vaelen/mini-xt/hardware/sheets/addr_decode.kicad_sch

## KiCad design hardware/sheets/addr_decode.kicad_sch (2026-07-23)

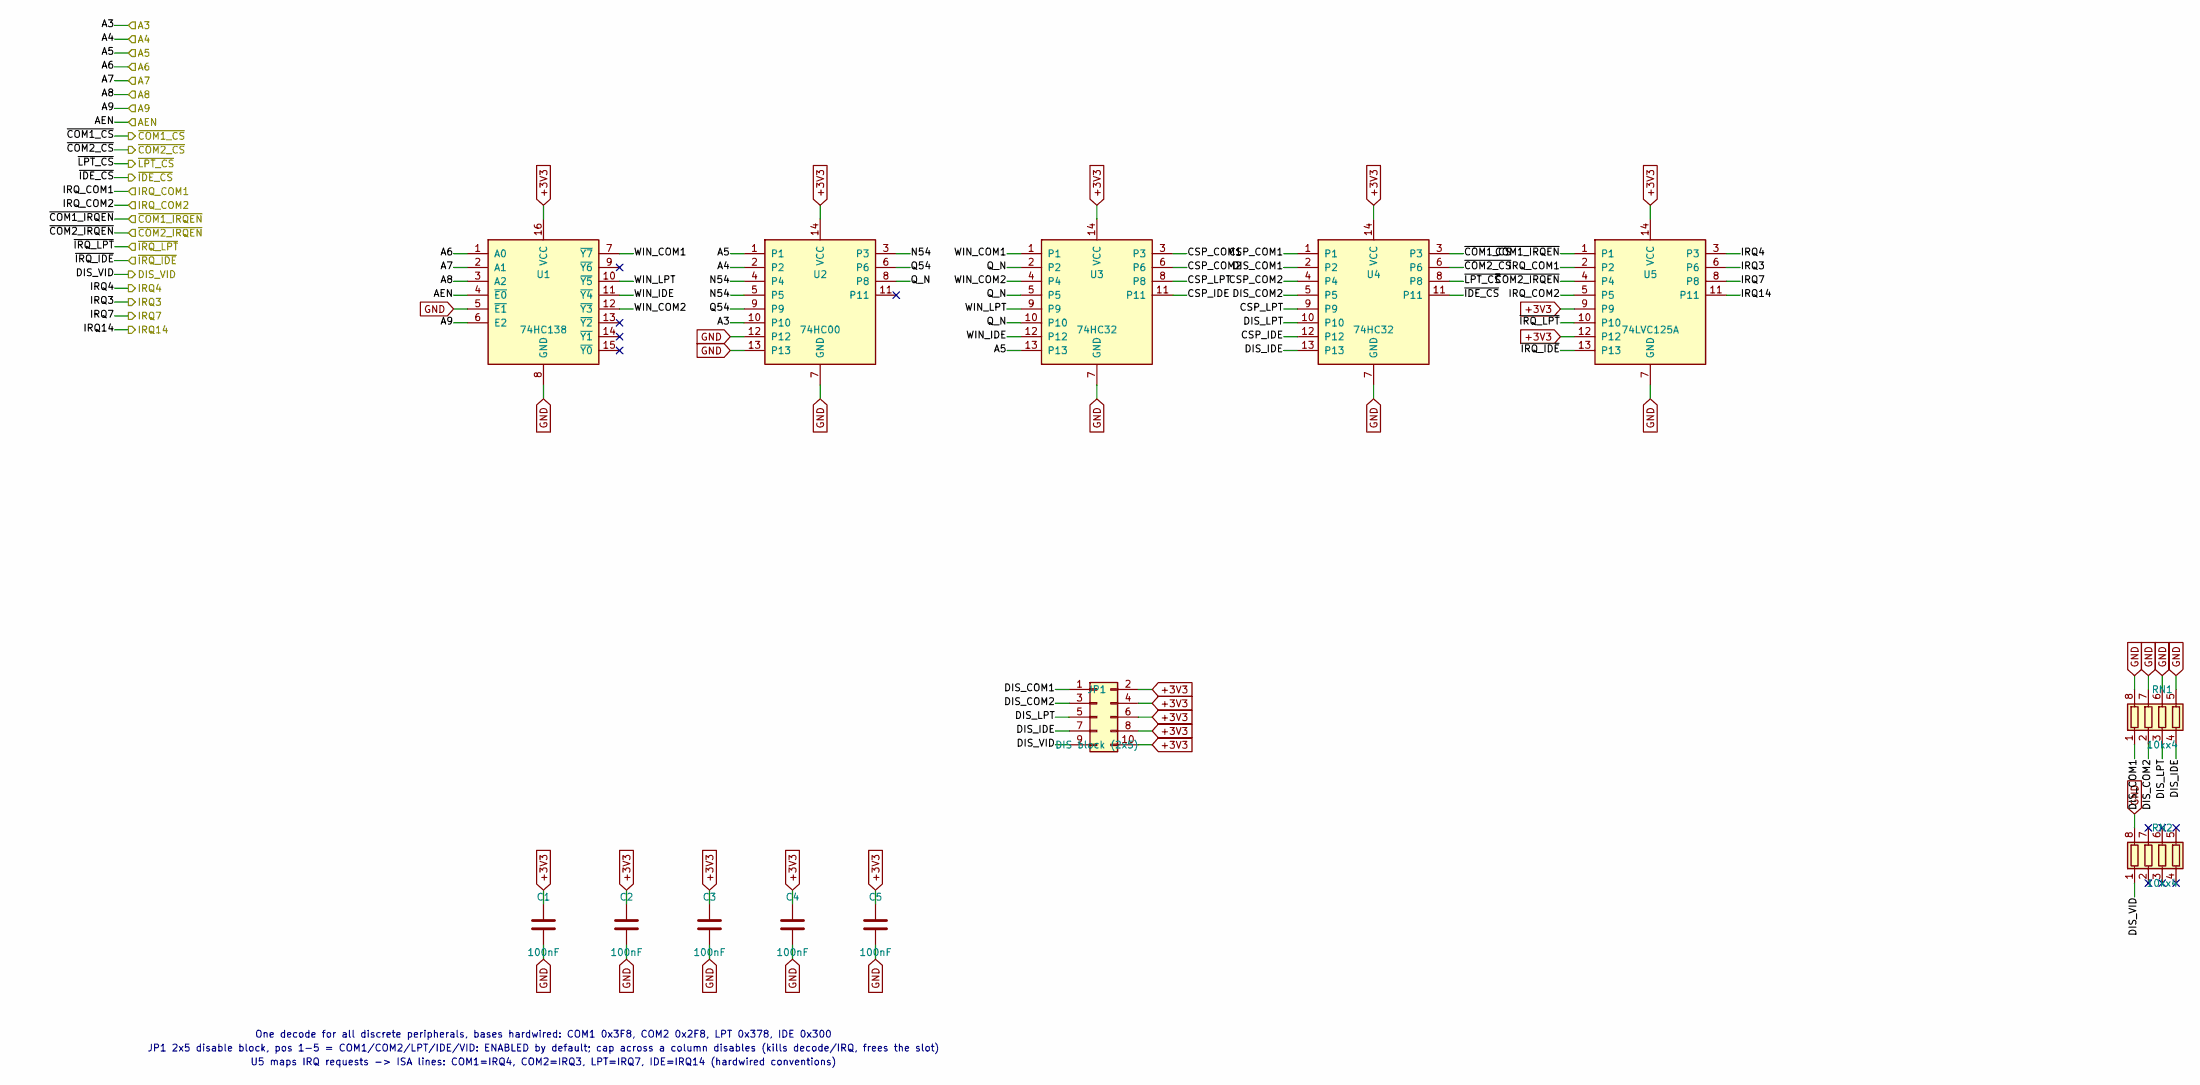
[picture p21: schematic addr_decode.kicad_sch]

Parts:
C1, C2, C3, C4, C5: 100nF; C_0603_1608Metric; LCSC Part Num C14663
JP1: DIS block (2x5); PinHeader_2x05_P2.54mm_Vertical; LCSC Part Num C492422
RN1, RN2: 10kx4; R_Array_Convex_4x0603; LCSC Part Num C29718
U1: 74HC138; SOIC-16_3.9x9.9mm_P1.27mm; LCSC Part Num C5602
U2: 74HC00; SOIC-14_3.9x8.7mm_P1.27mm; LCSC Part Num C699445
U3, U4: 74HC32; SOIC-14_3.9x8.7mm_P1.27mm; LCSC Part Num C52140395
U5: 74LVC125A; SOIC-14_3.9x8.7mm_P1.27mm; LCSC Part Num C6057

Connections:
+3V3: C1.1, C2.1, C3.1, C4.1, C5.1, JP1.2, JP1.4, JP1.6, JP1.8, JP1.10, U1.16 (VCC), U2.14 (VCC), U3.14 (VCC), U4.14 (VCC), U5.9, U5.12, U5.14 (VCC)
A3: U2.10
A4: U2.2
A5: U2.1, U3.13
A6: U1.1 (A0)
A7: U1.2 (A1)
A8: U1.3 (A2)
A9: U1.6 (E2)
AEN: U1.4 (~E0)
CSP_COM1: U3.3, U4.1
CSP_COM2: U3.6, U4.4
CSP_IDE: U3.11, U4.12
CSP_LPT: U3.8, U4.9
DIS_COM1: JP1.1, RN1.1 (R1.1), U4.2
DIS_COM2: JP1.3, RN1.2 (R2.1), U4.5
DIS_IDE: JP1.7, RN1.4 (R4.1), U4.13
DIS_LPT: JP1.5, RN1.3 (R3.1), U4.10
DIS_VID: JP1.9, RN2.1 (R1.1)
GND: C1.2, C2.2, C3.2, C4.2, C5.2, RN1.5 (R4.2), RN1.6 (R3.2), RN1.7 (R2.2), RN1.8 (R1.2), RN2.8 (R1.2), U1.5 (~E1), U1.8 (GND), U2.7 (GND), U2.12, U2.13, U3.7 (GND), U4.7 (GND), U5.7 (GND)
IRQ3: U5.6
IRQ4: U5.3
IRQ7: U5.8
IRQ14: U5.11
IRQ_COM1: U5.2
IRQ_COM2: U5.5
N54: U2.3, U2.4, U2.5
Q54: U2.6, U2.9
Q_N: U2.8, U3.2, U3.5, U3.10
WIN_COM1: U1.7 (~Y7), U3.1
WIN_COM2: U1.12 (~Y3), U3.4
WIN_IDE: U1.11 (~Y4), U3.12
WIN_LPT: U1.10 (~Y5), U3.9
~COM1_CS: U4.3
~COM1_IRQEN: U5.1
~COM2_CS: U4.6
~COM2_IRQEN: U5.4
~IDE_CS: U4.11
~IRQ_IDE: U5.13
~IRQ_LPT: U5.10
~LPT_CS: U4.8

Notes on the sheet:
One decode for all discrete peripherals, bases hardwired: COM1 0x3F8, COM2 0x2F8, LPT 0x378, IDE 0x300
JP1 2x5 disable block, pos 1-5 = COM1/COM2/LPT/IDE/VID: ENABLED by default; cap across a column disables (kills decode/IRQ, frees the slot)
U5 maps IRQ requests -> ISA lines: COM1=IRQ4, COM2=IRQ3, LPT=IRQ7, IDE=IRQ14 (hardwired conventions)
