vaelen/mini-xt/hardware/sheets/audio.kicad_sch

## KiCad design hardware/sheets/audio.kicad_sch (2026-07-23)

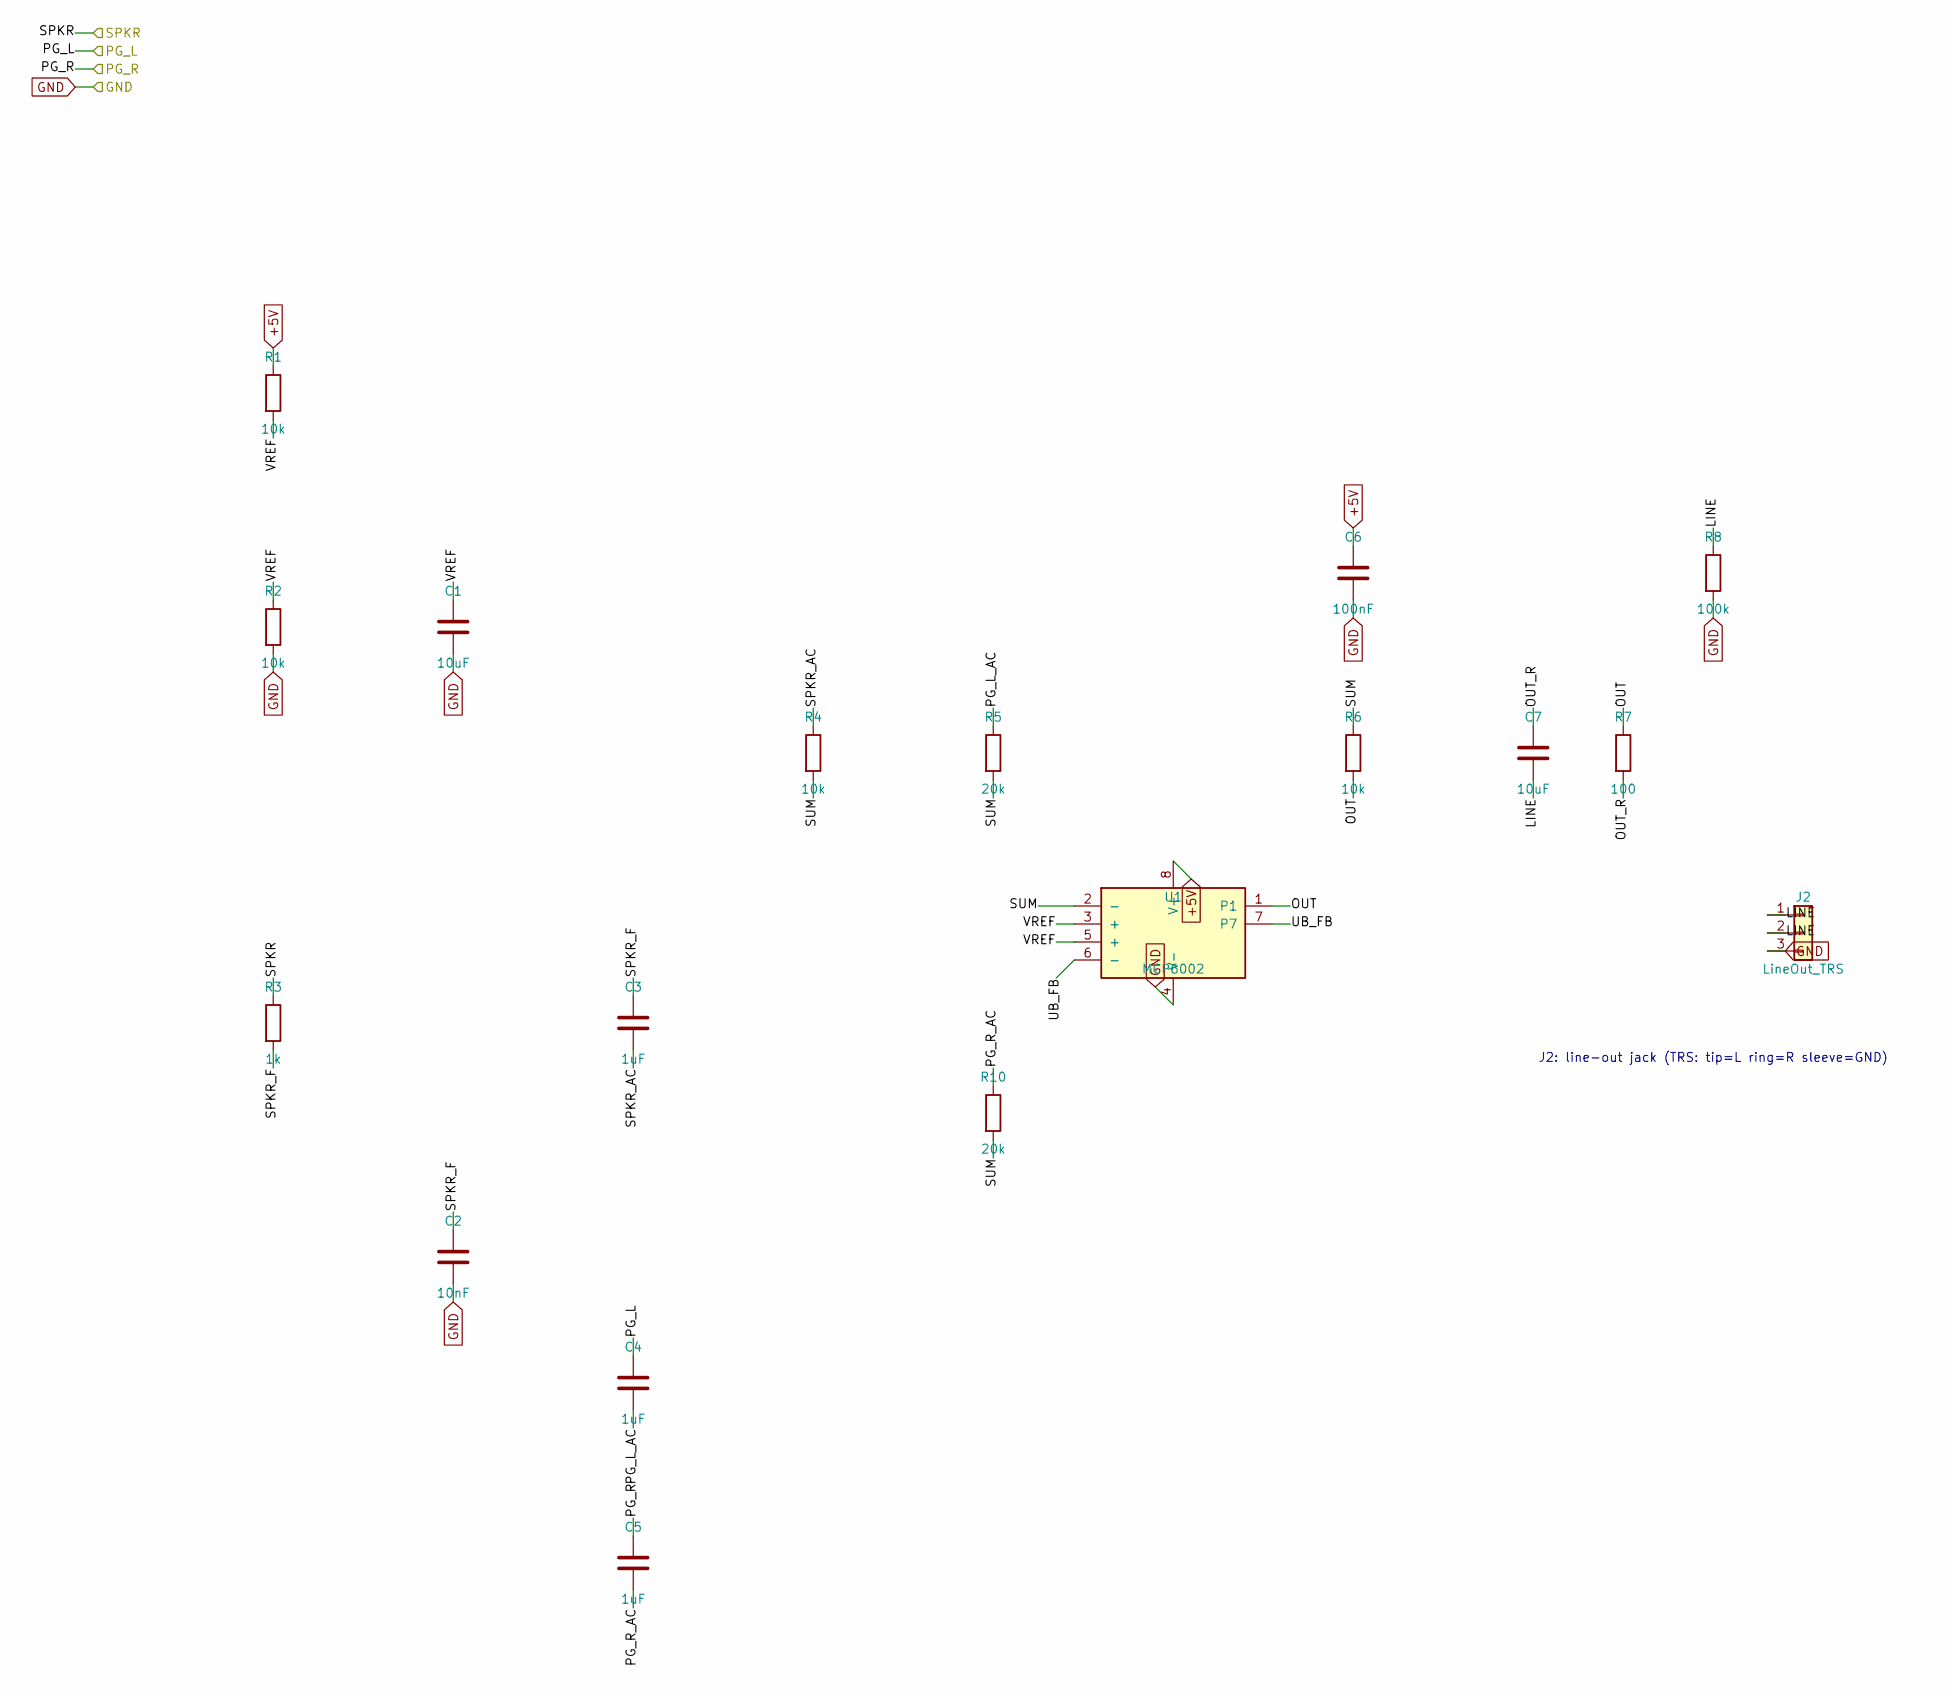
[picture p22: schematic audio.kicad_sch]

Parts:
C1, C7: 10uF; C_0805_2012Metric; LCSC Part Num C15850
C2: 10nF; C_0603_1608Metric; LCSC Part Num C57112
C3, C4, C5: 1uF; C_0603_1608Metric; LCSC Part Num C15849
C6: 100nF; C_0603_1608Metric; LCSC Part Num C14663
J2: LineOut_TRS; PinHeader_1x03_P2.54mm_Vertical; LCSC Part Num C2337
R1, R2, R4, R6: 10k; R_0805_2012Metric; LCSC Part Num C17414
R3: 1k; R_0603_1608Metric; LCSC Part Num C21190
R5, R10: 20k; R_0603_1608Metric; LCSC Part Num C4184
R7: 100; R_0603_1608Metric; LCSC Part Num C22775
R8: 100k; R_0603_1608Metric; LCSC Part Num C25803
U1: MCP6002; SOIC-8_3.9x4.9mm_P1.27mm; LCSC Part Num C7377

Connections:
+5V: C6.1, R1.1, U1.8 (V+)
GND: C1.2, C2.2, C6.2, J2.3, R2.2, R8.2, U1.4 (V-)
LINE: C7.2, J2.1, J2.2, R8.1
OUT: R6.2, R7.1, U1.1
OUT_R: C7.1, R7.2
PG_L: C4.1
PG_L_AC: C4.2, R5.1
PG_R: C5.1
PG_R_AC: C5.2, R10.1
SPKR: R3.1
SPKR_AC: C3.2, R4.1
SPKR_F: C2.1, C3.1, R3.2
SUM: R4.2, R5.2, R6.1, R10.2, U1.2 (-)
UB_FB: U1.6 (-), U1.7
VREF: C1.1, R1.2, R2.1, U1.3 (+), U1.5 (+)

Notes on the sheet:
J2: line-out jack (TRS: tip=L ring=R sleeve=GND)
