vaelen/mini-xt/hardware/sheets/bus_mcu.kicad_sch

## KiCad design hardware/sheets/bus_mcu.kicad_sch (2026-07-23)

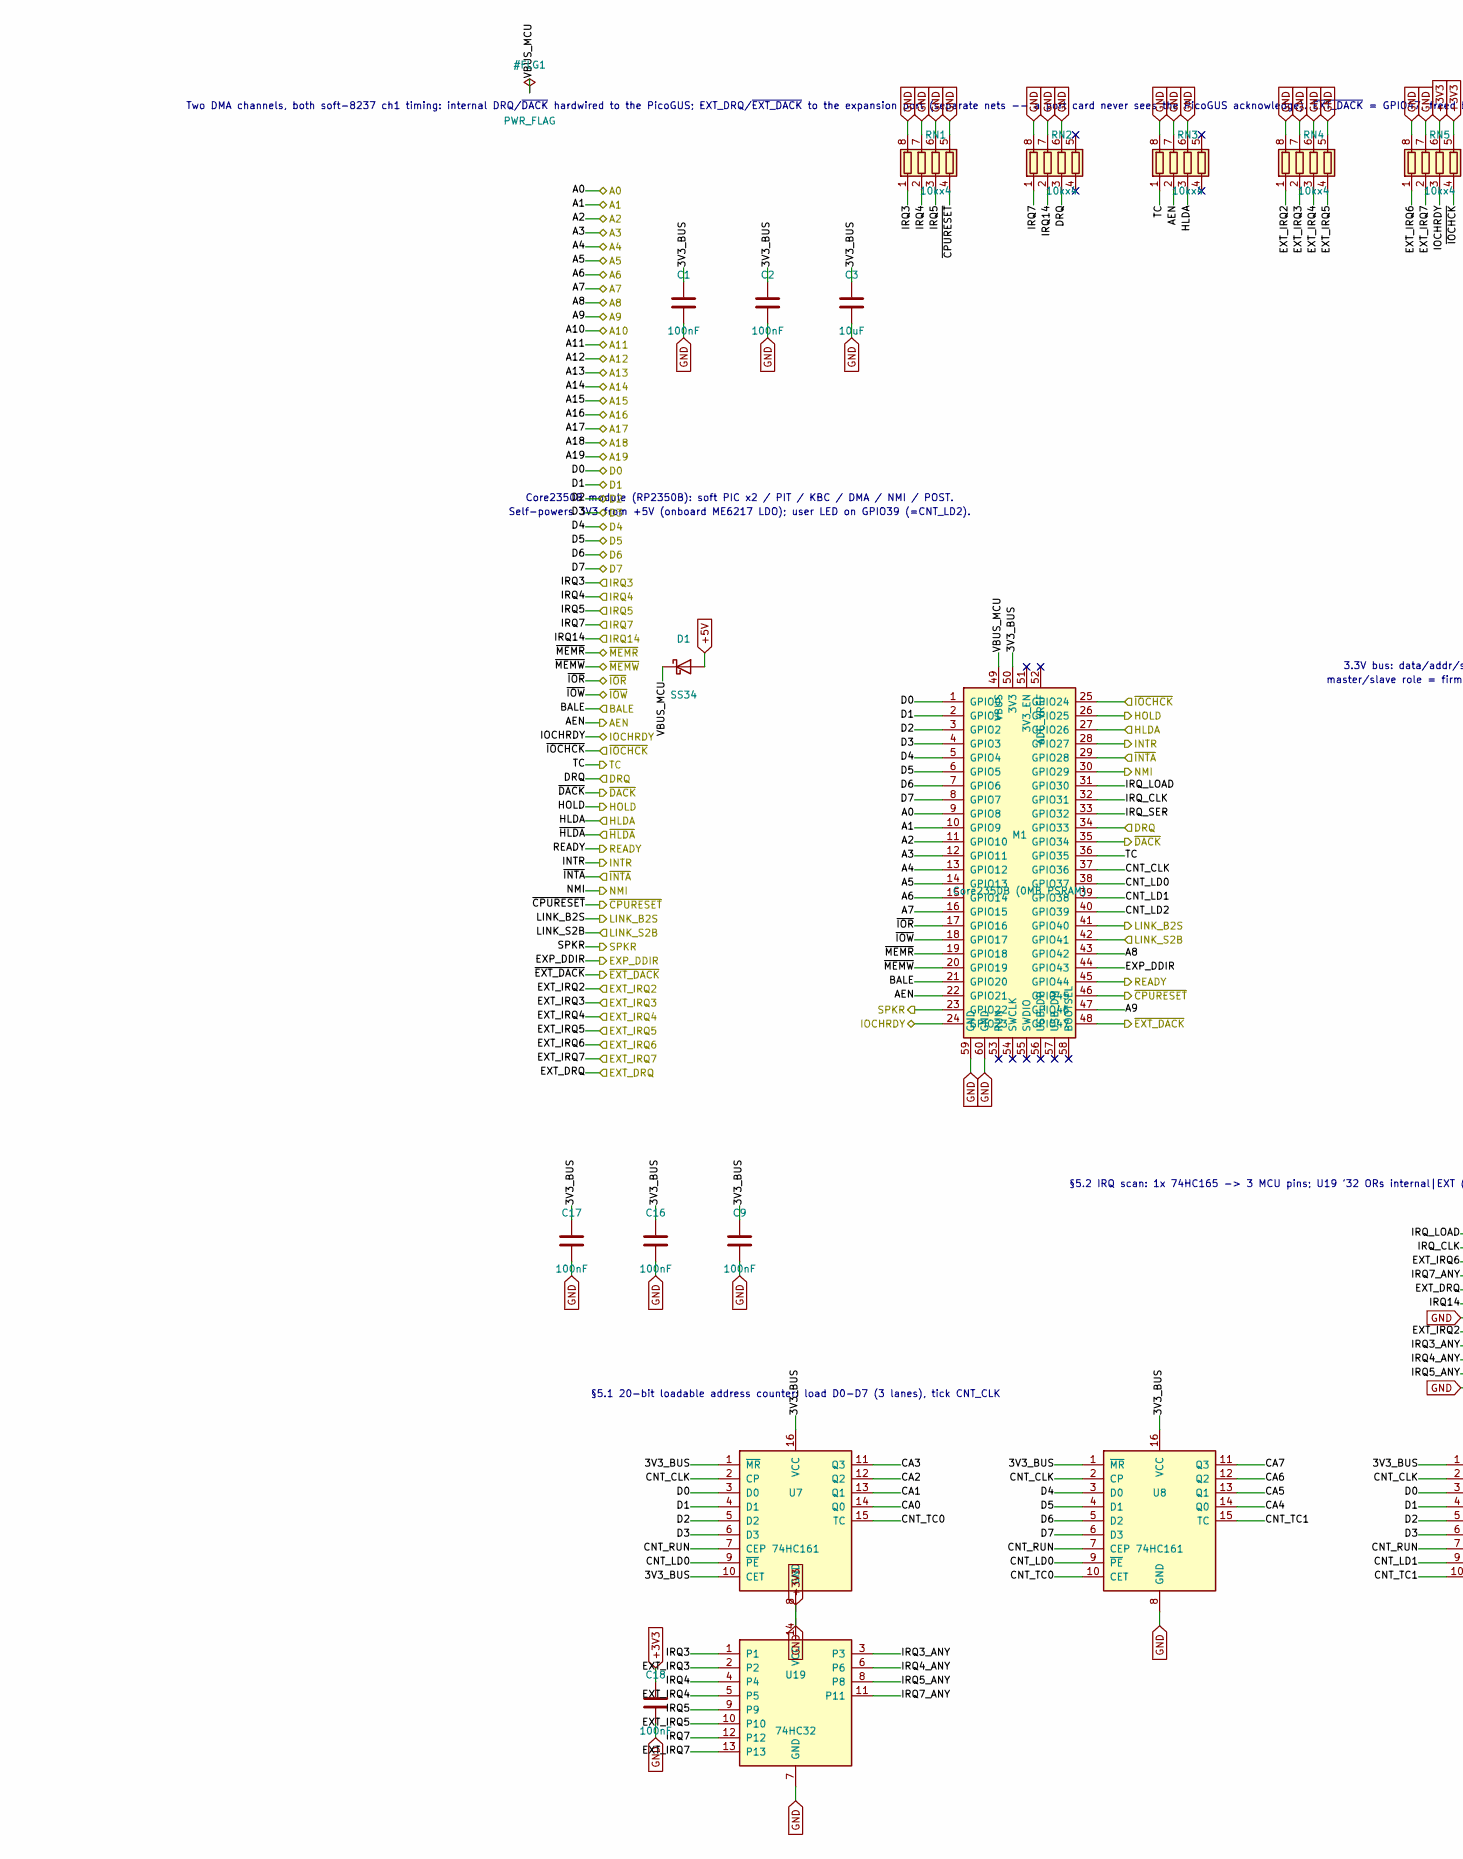
[picture p23: schematic bus_mcu.kicad_sch, part in row 1, column 1]

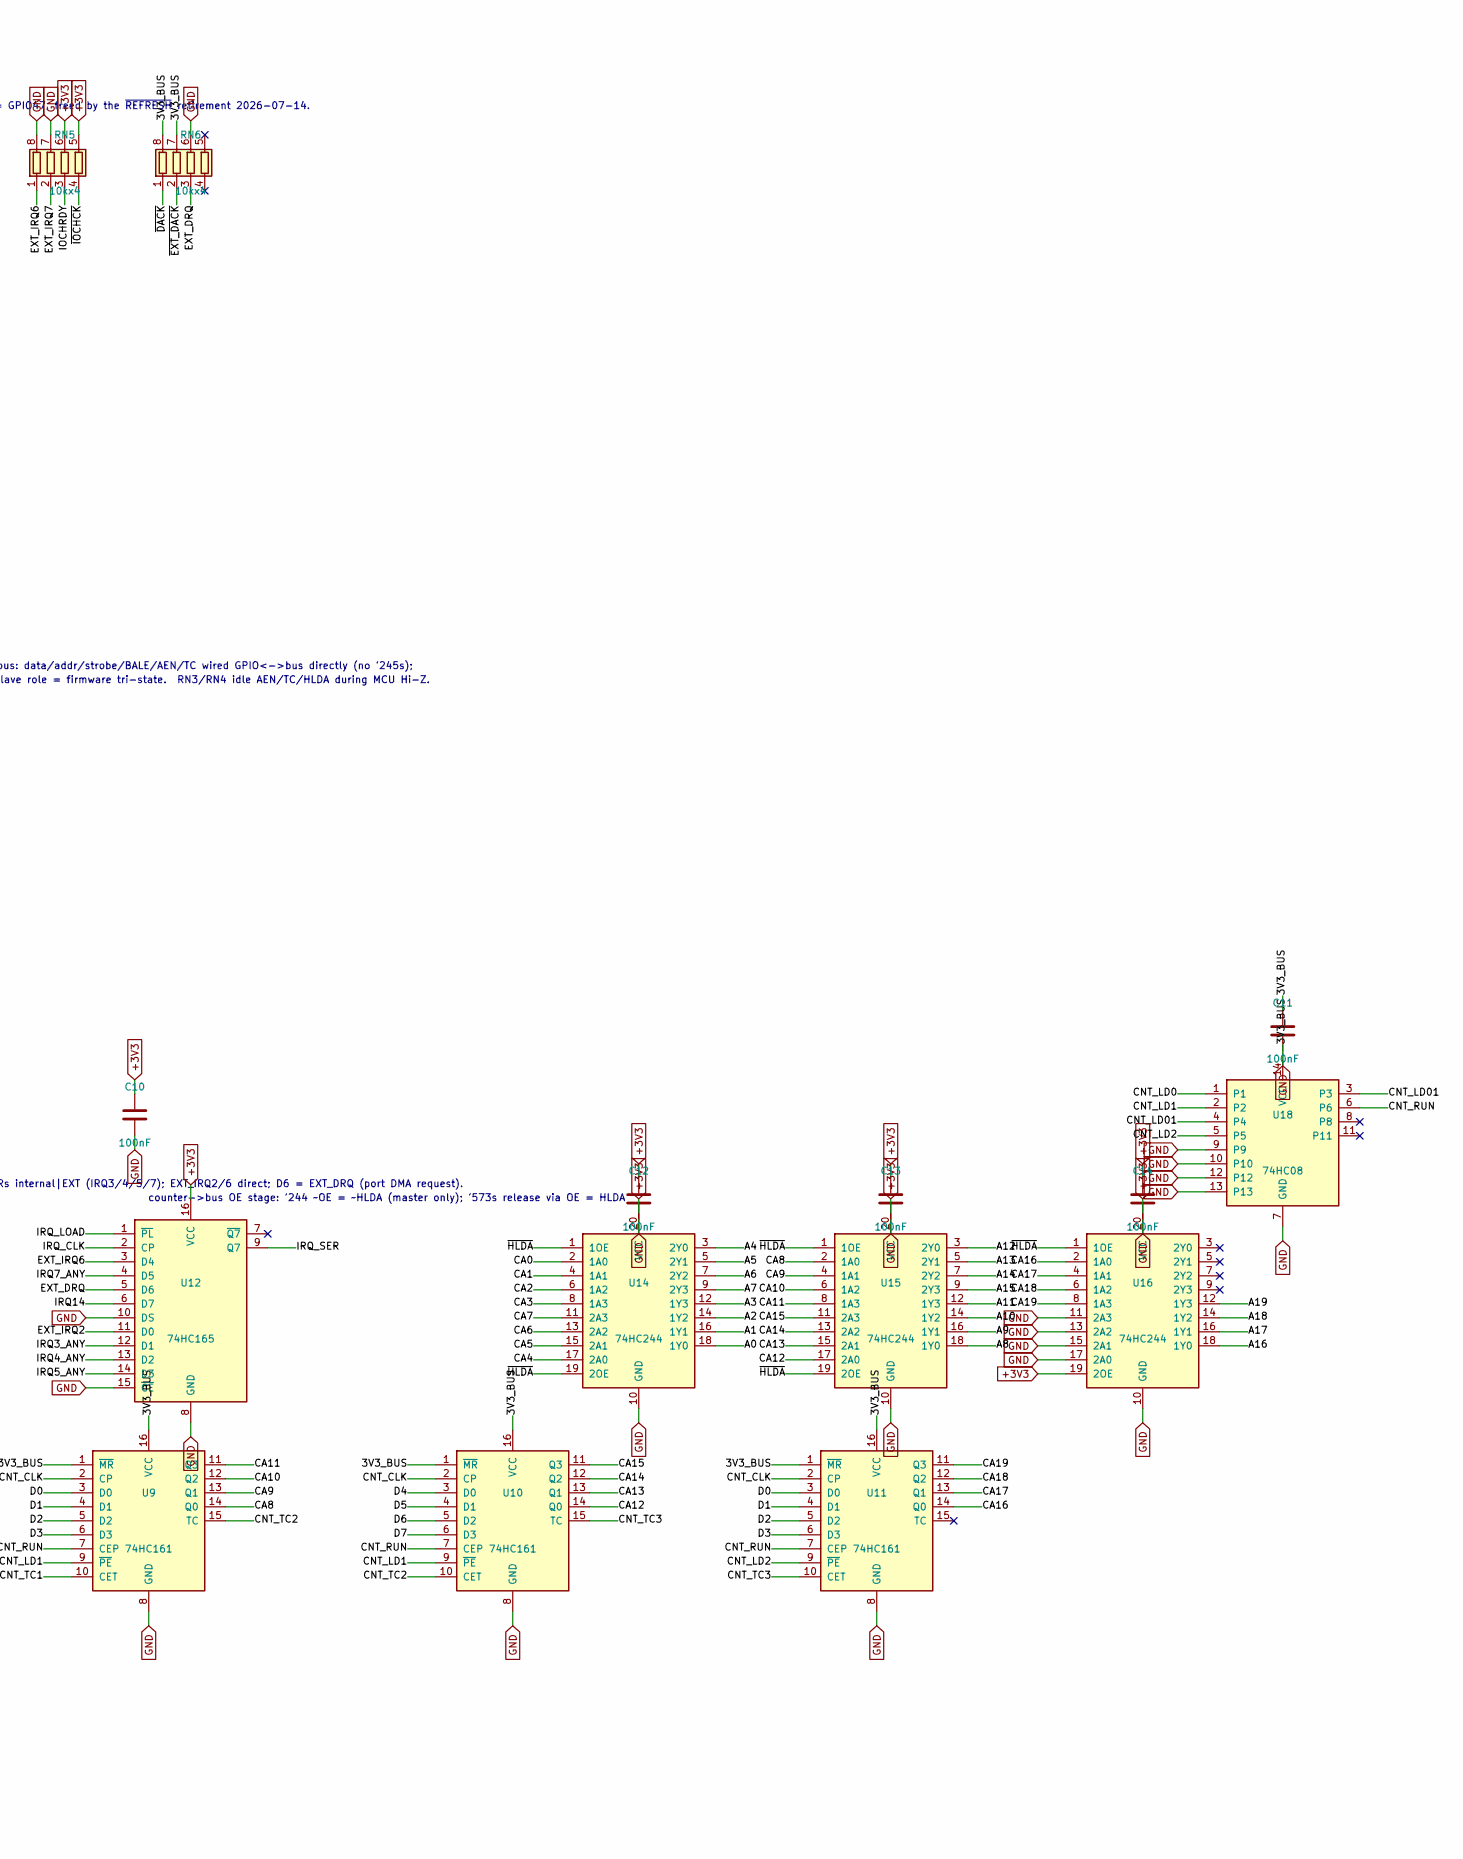
[picture p24: schematic bus_mcu.kicad_sch, part in row 1, column 2]

Parts:
C1, C2, C9, C10, C11, C12, C13, C14, C16, C17, C18: 100nF; C_0603_1608Metric; LCSC Part Num C14663
C3: 10uF; C_0805_2012Metric; LCSC Part Num C15850
D1: SS34; D_SMA; LCSC Part Num C8678
M1: Core2350B (0MB PSRAM); Core2350B_PGA; LCSC Part Num C2897411
RN1, RN2, RN3, RN4, RN5, RN6: 10kx4; R_Array_Convex_4x0603; LCSC Part Num C29718
U7, U8, U9, U10, U11: 74HC161; SOIC-16_3.9x9.9mm_P1.27mm; LCSC Part Num C5610
U12: 74HC165; SOIC-16_3.9x9.9mm_P1.27mm; LCSC Part Num C5613
U14, U15, U16: 74HC244; SOIC-20W_7.5x12.8mm_P1.27mm; LCSC Part Num C52140409
U18: 74HC08; SOIC-14_3.9x8.7mm_P1.27mm; LCSC Part Num C5593
U19: 74HC32; SOIC-14_3.9x8.7mm_P1.27mm; LCSC Part Num C52140395

Connections:
3V3_BUS: C1.1, C2.1, C3.1, C9.1, C11.1, C16.1, C17.1, M1.50 (3V3), RN6.7 (R2.2), RN6.8 (R1.2), U7.1 (~MR), U7.10 (CET), U7.16 (VCC), U8.1 (~MR), U8.16 (VCC), U9.1 (~MR), U9.16 (VCC), U10.1 (~MR), U10.16 (VCC), U11.1 (~MR), U11.16 (VCC), U18.14 (VCC)
+3V3: C10.1, C12.1, C13.1, C14.1, C18.1, RN5.5 (R4.2), RN5.6 (R3.2), U12.16 (VCC), U14.20 (VCC), U15.20 (VCC), U16.19 (2OE), U16.20 (VCC), U19.14 (VCC)
+5V: D1.2 (A)
A0: M1.9 (GPIO8), U14.18 (1Y0)
A1: M1.10 (GPIO9), U14.16 (1Y1)
A2: M1.11 (GPIO10), U14.14 (1Y2)
A3: M1.12 (GPIO11), U14.12 (1Y3)
A4: M1.13 (GPIO12), U14.3 (2Y0)
A5: M1.14 (GPIO13), U14.5 (2Y1)
A6: M1.15 (GPIO14), U14.7 (2Y2)
A7: M1.16 (GPIO15), U14.9 (2Y3)
A8: M1.43 (GPIO42), U15.18 (1Y0)
A9: M1.47 (GPIO46), U15.16 (1Y1)
A10: U15.14 (1Y2)
A11: U15.12 (1Y3)
A12: U15.3 (2Y0)
A13: U15.5 (2Y1)
A14: U15.7 (2Y2)
A15: U15.9 (2Y3)
A16: U16.18 (1Y0)
A17: U16.16 (1Y1)
A18: U16.14 (1Y2)
A19: U16.12 (1Y3)
AEN: M1.22 (GPIO21), RN3.2 (R2.1)
BALE: M1.21 (GPIO20)
CA0: U7.14 (Q0), U14.2 (1A0)
CA1: U7.13 (Q1), U14.4 (1A1)
CA2: U7.12 (Q2), U14.6 (1A2)
CA3: U7.11 (Q3), U14.8 (1A3)
CA4: U8.14 (Q0), U14.17 (2A0)
CA5: U8.13 (Q1), U14.15 (2A1)
CA6: U8.12 (Q2), U14.13 (2A2)
CA7: U8.11 (Q3), U14.11 (2A3)
CA8: U9.14 (Q0), U15.2 (1A0)
CA9: U9.13 (Q1), U15.4 (1A1)
CA10: U9.12 (Q2), U15.6 (1A2)
CA11: U9.11 (Q3), U15.8 (1A3)
CA12: U10.14 (Q0), U15.17 (2A0)
CA13: U10.13 (Q1), U15.15 (2A1)
CA14: U10.12 (Q2), U15.13 (2A2)
CA15: U10.11 (Q3), U15.11 (2A3)
CA16: U11.14 (Q0), U16.2 (1A0)
CA17: U11.13 (Q1), U16.4 (1A1)
CA18: U11.12 (Q2), U16.6 (1A2)
CA19: U11.11 (Q3), U16.8 (1A3)
CNT_CLK: M1.37 (GPIO36), U7.2 (CP), U8.2 (CP), U9.2 (CP), U10.2 (CP), U11.2 (CP)
CNT_LD0: M1.38 (GPIO37), U7.9 (~PE), U8.9 (~PE), U18.1
CNT_LD1: M1.39 (GPIO38), U9.9 (~PE), U10.9 (~PE), U18.2
CNT_LD01: U18.3, U18.4
CNT_LD2: M1.40 (GPIO39), U11.9 (~PE), U18.5
CNT_RUN: U7.7 (CEP), U8.7 (CEP), U9.7 (CEP), U10.7 (CEP), U11.7 (CEP), U18.6
CNT_TC0: U7.15 (TC), U8.10 (CET)
CNT_TC1: U8.15 (TC), U9.10 (CET)
CNT_TC2: U9.15 (TC), U10.10 (CET)
CNT_TC3: U10.15 (TC), U11.10 (CET)
D0: M1.1 (GPIO0), U7.3 (D0), U9.3 (D0), U11.3 (D0)
D1: M1.2 (GPIO1), U7.4 (D1), U9.4 (D1), U11.4 (D1)
D2: M1.3 (GPIO2), U7.5 (D2), U9.5 (D2), U11.5 (D2)
D3: M1.4 (GPIO3), U7.6 (D3), U9.6 (D3), U11.6 (D3)
D4: M1.5 (GPIO4), U8.3 (D0), U10.3 (D0)
D5: M1.6 (GPIO5), U8.4 (D1), U10.4 (D1)
D6: M1.7 (GPIO6), U8.5 (D2), U10.5 (D2)
D7: M1.8 (GPIO7), U8.6 (D3), U10.6 (D3)
DRQ: M1.34 (GPIO33), RN2.3 (R3.1)
EXP_DDIR: M1.44 (GPIO43)
EXT_DRQ: RN6.3 (R3.1), U12.5 (D6)
EXT_IRQ2: RN4.1 (R1.1), U12.11 (D0)
EXT_IRQ3: RN4.2 (R2.1), U19.2
EXT_IRQ4: RN4.3 (R3.1), U19.5
EXT_IRQ5: RN4.4 (R4.1), U19.10
EXT_IRQ6: RN5.1 (R1.1), U12.3 (D4)
EXT_IRQ7: RN5.2 (R2.1), U19.13
GND: C1.2, C2.2, C3.2, C9.2, C10.2, C11.2, C12.2, C13.2, C14.2, C16.2, C17.2, C18.2, M1.59 (GND), M1.60 (GND), RN1.5 (R4.2), RN1.6 (R3.2), RN1.7 (R2.2), RN1.8 (R1.2), RN2.6 (R3.2), RN2.7 (R2.2), RN2.8 (R1.2), RN3.6 (R3.2), RN3.7 (R2.2), RN3.8 (R1.2), RN4.5 (R4.2), RN4.6 (R3.2), RN4.7 (R2.2), RN4.8 (R1.2), RN5.7 (R2.2), RN5.8 (R1.2), RN6.6 (R3.2), U7.8 (GND), U8.8 (GND), U9.8 (GND), U10.8 (GND), U11.8 (GND), U12.8 (GND), U12.10 (DS), U12.15 (~CE), U14.10 (GND), U15.10 (GND), U16.10 (GND), U16.11 (2A3), U16.13 (2A2), U16.15 (2A1), U16.17 (2A0), U18.7 (GND), U18.9, U18.10, U18.12, U18.13, U19.7 (GND)
HLDA: M1.27 (GPIO26), RN3.3 (R3.1)
HOLD: M1.26 (GPIO25)
INTR: M1.28 (GPIO27)
IOCHRDY: M1.24 (GPIO23), RN5.3 (R3.1)
IRQ3: RN1.1 (R1.1), U19.1
IRQ3_ANY: U12.12 (D1), U19.3
IRQ4: RN1.2 (R2.1), U19.4
IRQ4_ANY: U12.13 (D2), U19.6
IRQ5: RN1.3 (R3.1), U19.9
IRQ5_ANY: U12.14 (D3), U19.8
IRQ7: RN2.1 (R1.1), U19.12
IRQ7_ANY: U12.4 (D5), U19.11
IRQ14: RN2.2 (R2.1), U12.6 (D7)
IRQ_CLK: M1.32 (GPIO31), U12.2 (CP)
IRQ_LOAD: M1.31 (GPIO30), U12.1 (~PL)
IRQ_SER: M1.33 (GPIO32), U12.9 (Q7)
LINK_B2S: M1.41 (GPIO40)
LINK_S2B: M1.42 (GPIO41)
NMI: M1.30 (GPIO29)
READY: M1.45 (GPIO44)
SPKR: M1.23 (GPIO22)
TC: M1.36 (GPIO35), RN3.1 (R1.1)
VBUS_MCU: D1.1 (K), M1.49 (VBUS)
~CPURESET: M1.46 (GPIO45), RN1.4 (R4.1)
~DACK: M1.35 (GPIO34), RN6.1 (R1.1)
~EXT_DACK: M1.48 (GPIO47), RN6.2 (R2.1)
~HLDA: U14.1 (1OE), U14.19 (2OE), U15.1 (1OE), U15.19 (2OE), U16.1 (1OE)
~INTA: M1.29 (GPIO28)
~IOCHCK: M1.25 (GPIO24), RN5.4 (R4.1)
~IOR: M1.17 (GPIO16)
~IOW: M1.18 (GPIO17)
~MEMR: M1.19 (GPIO18)
~MEMW: M1.20 (GPIO19)

Notes on the sheet:
Core2350B module (RP2350B): soft PIC x2 / PIT / KBC / DMA / NMI / POST.
Self-powers 3V3 from +5V (onboard ME6217 LDO); user LED on GPIO39 (=CNT_LD2).
§5.1 20-bit loadable address counter: load D0-D7 (3 lanes), tick CNT_CLK
counter->bus OE stage: '244 ~OE = ~HLDA (master only); '573s release via OE = HLDA
§5.2 IRQ scan: 1x 74HC165 -> 3 MCU pins; U19 '32 ORs internal|EXT (IRQ3/4/5/7); EXT_IRQ2/6 direct; D6 = EXT_DRQ (port DMA request).
Two DMA channels, both soft-8237 ch1 timing: internal DRQ/~{DACK} hardwired to the PicoGUS; EXT_DRQ/~{EXT_DACK} to the expansion port (separate nets -- a port card never sees the PicoGUS acknowledge). ~{EXT_DACK} = GPIO47, freed by the ~{REFRESH} retirement 2026-07-14.
3.3V bus: data/addr/strobe/BALE/AEN/TC wired GPIO<->bus directly (no '245s);
master/slave role = firmware tri-state. RN3/RN4 idle AEN/TC/HLDA during MCU Hi-Z.
