vaelen/mini-xt/hardware/sheets/com_port.kicad_sch

## KiCad design hardware/sheets/com_port.kicad_sch (2026-07-23)

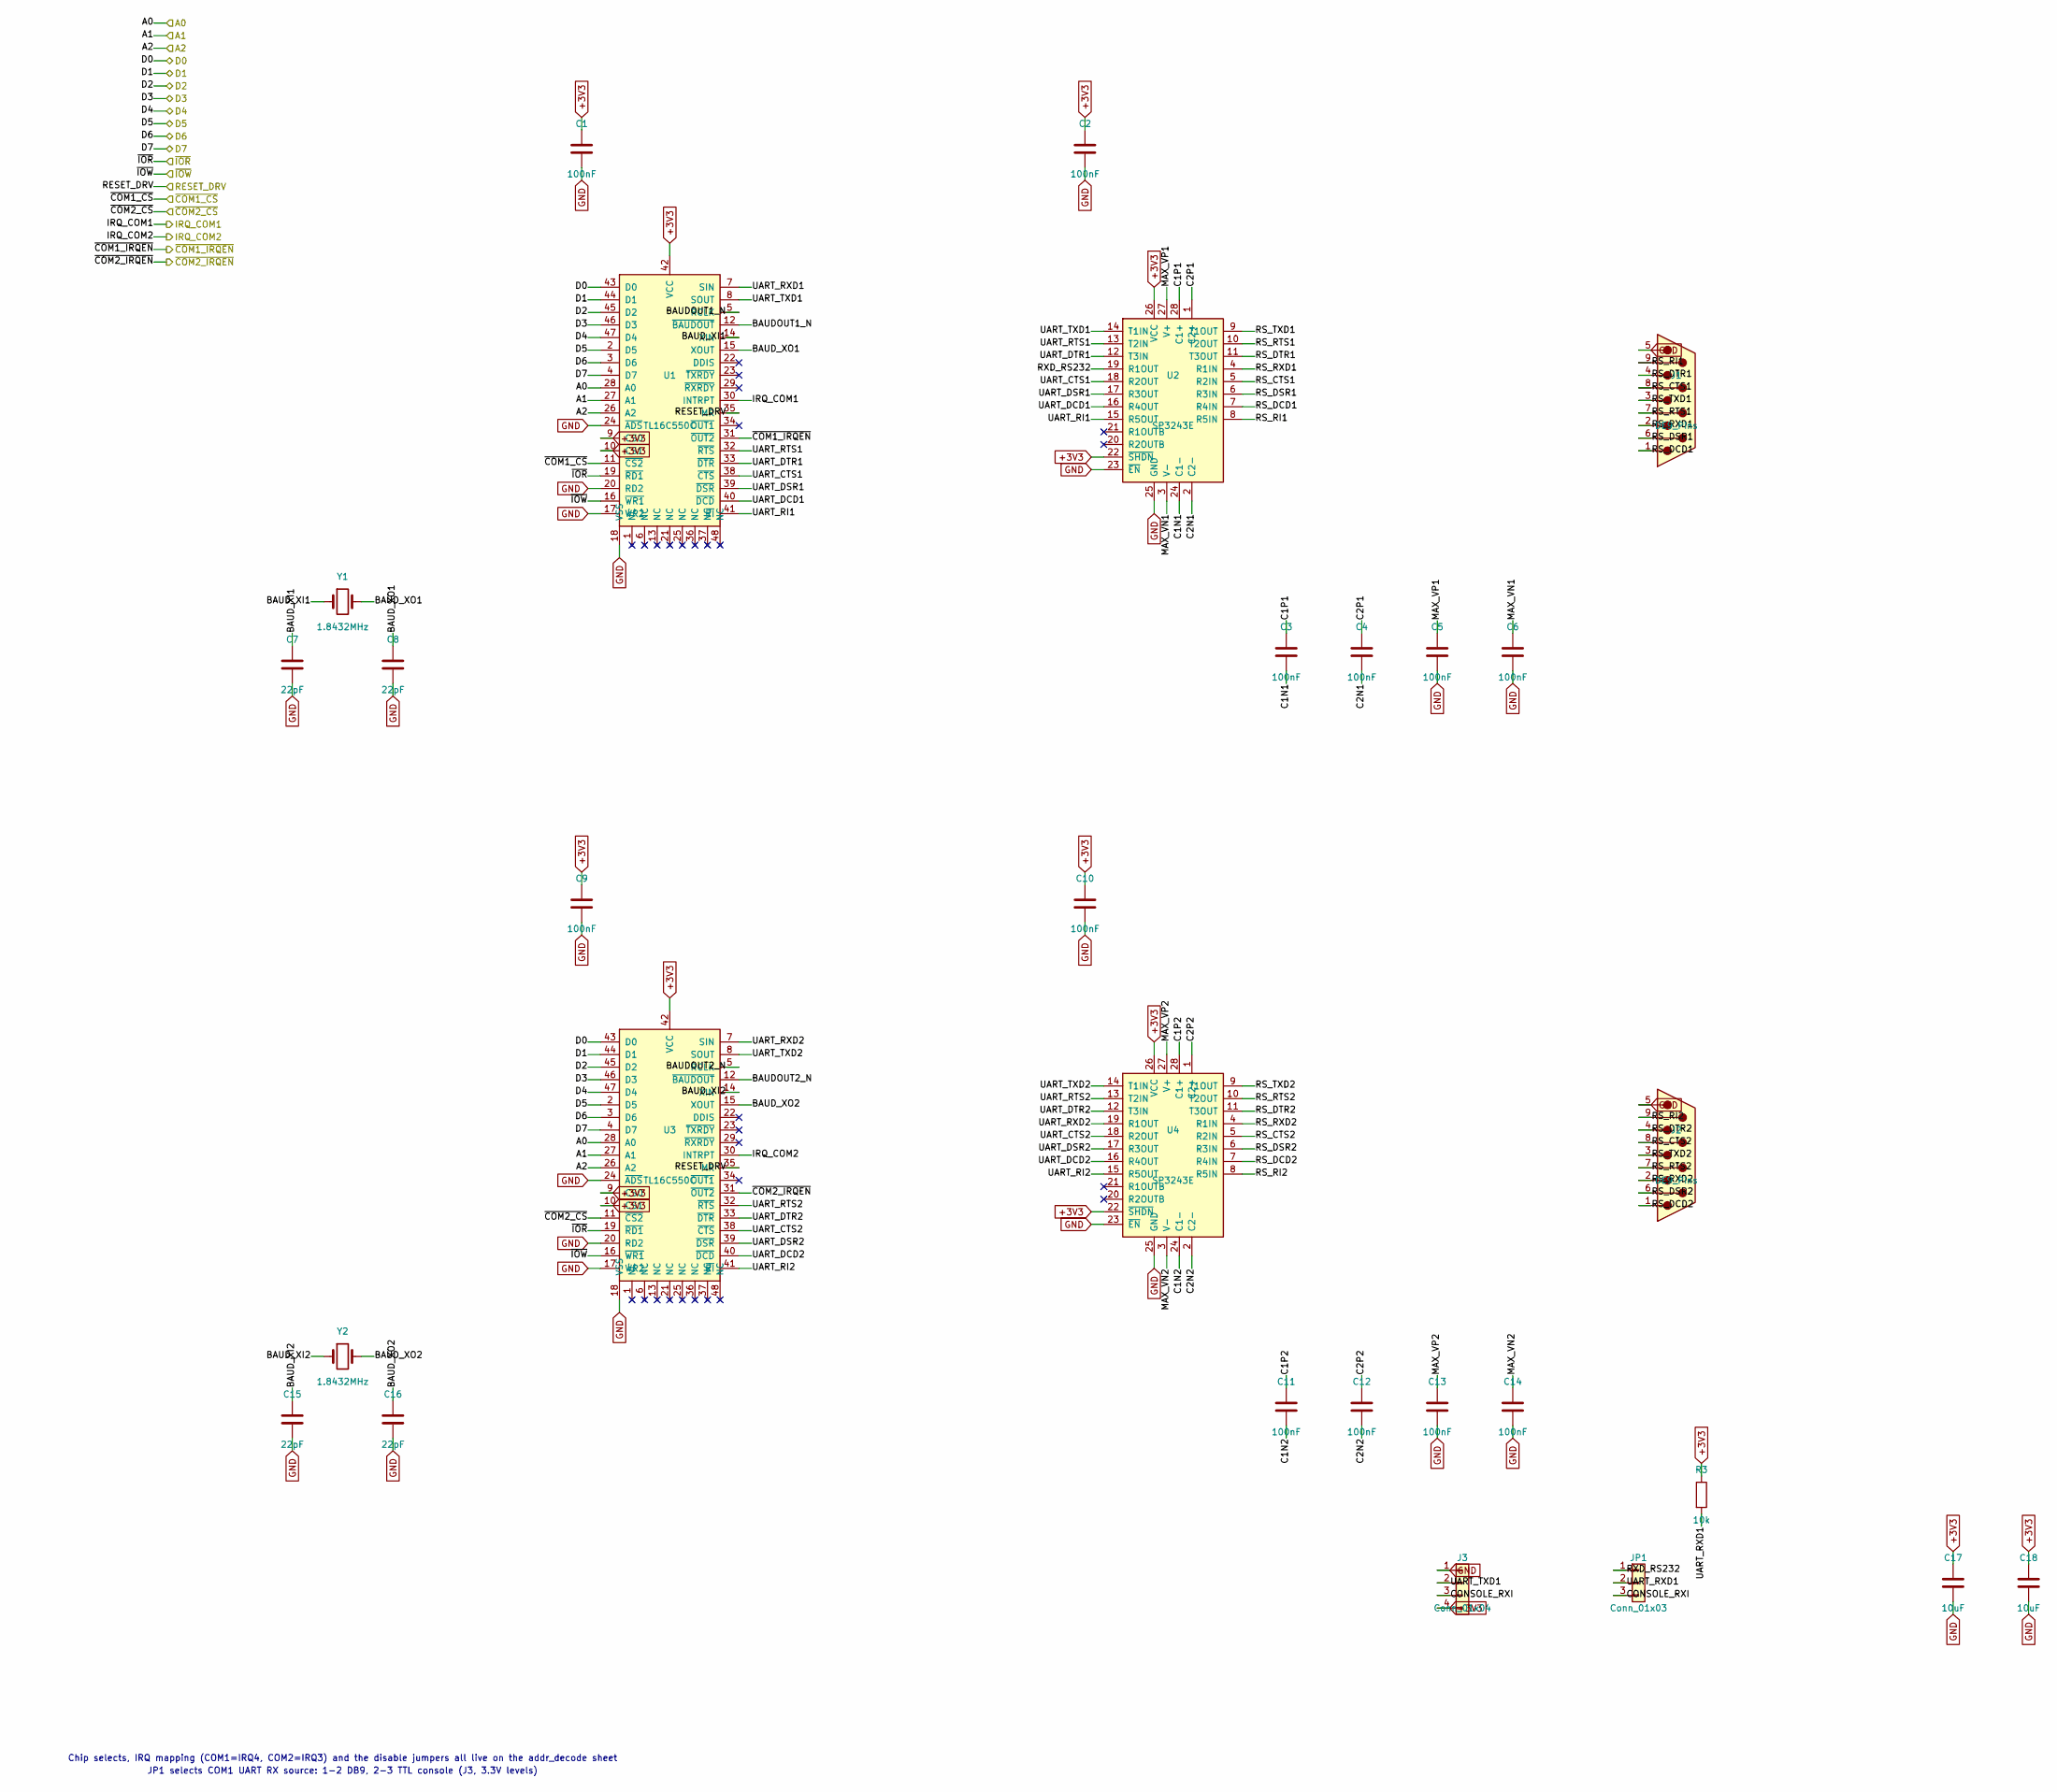
[picture p25: schematic com_port.kicad_sch]

Parts:
C1, C2, C3, C4, C5, C6, C9, C10, C11, C12, C13, C14: 100nF; C_0603_1608Metric; LCSC Part Num C14663
C7, C8, C15, C16: 22pF; C_0603_1608Metric; LCSC Part Num C1653
C17, C18: 10uF; C_0805_2012Metric; LCSC Part Num C15850
J1, J2: DE9_Pins; DSUB-9_Pins_Horizontal_P2.77x2.84mm_EdgePinOffset9.90mm_Hou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; LCSC Part Num C141880
J3: Conn_01x04; PinHeader_1x04_P2.54mm_Vertical; LCSC Part Num C2337
JP1: Conn_01x03; PinHeader_1x03_P2.54mm_Vertical; LCSC Part Num C2337
R3: 10k; R_0805_2012Metric; LCSC Part Num C17414
U1, U3: TL16C550C; TQFP-48_7x7mm_P0.5mm; LCSC Part Num C882798
U2, U4: SP3243E; SSOP-28_5.3x10.2mm_P0.65mm; LCSC Part Num C916165
Y1, Y2: 1.8432MHz; Crystal_HC49-U_Vertical; LCSC Part Num C47345430

Connections:
+3V3: C1.1, C2.1, C9.1, C10.1, C17.1, C18.1, J3.4, R3.1, U1.9 (CS0), U1.10 (CS1), U1.42 (VCC), U2.22 (~SHDN), U2.26 (VCC), U3.9 (CS0), U3.10 (CS1), U3.42 (VCC), U4.22 (~SHDN), U4.26 (VCC)
A0: U1.28 (A0), U3.28 (A0)
A1: U1.27 (A1), U3.27 (A1)
A2: U1.26 (A2), U3.26 (A2)
BAUDOUT1_N: U1.5 (RCLK), U1.12 (~BAUDOUT)
BAUDOUT2_N: U3.5 (RCLK), U3.12 (~BAUDOUT)
BAUD_XI1: C7.1, U1.14 (XIN), Y1.1
BAUD_XI2: C15.1, U3.14 (XIN), Y2.1
BAUD_XO1: C8.1, U1.15 (XOUT), Y1.2
BAUD_XO2: C16.1, U3.15 (XOUT), Y2.2
C1N1: C3.2, U2.24 (C1-)
C1N2: C11.2, U4.24 (C1-)
C1P1: C3.1, U2.28 (C1+)
C1P2: C11.1, U4.28 (C1+)
C2N1: C4.2, U2.2 (C2-)
C2N2: C12.2, U4.2 (C2-)
C2P1: C4.1, U2.1 (C2+)
C2P2: C12.1, U4.1 (C2+)
CONSOLE_RXI: J3.3, JP1.3
D0: U1.43 (D0), U3.43 (D0)
D1: U1.44 (D1), U3.44 (D1)
D2: U1.45 (D2), U3.45 (D2)
D3: U1.46 (D3), U3.46 (D3)
D4: U1.47 (D4), U3.47 (D4)
D5: U1.2 (D5), U3.2 (D5)
D6: U1.3 (D6), U3.3 (D6)
D7: U1.4 (D7), U3.4 (D7)
GND: C1.2, C2.2, C5.2, C6.2, C7.2, C8.2, C9.2, C10.2, C13.2, C14.2, C15.2, C16.2, C17.2, C18.2, J1.5, J2.5, J3.1, U1.17 (WR2), U1.18 (VSS), U1.20 (RD2), U1.24 (~ADS), U2.23 (~EN), U2.25 (GND), U3.17 (WR2), U3.18 (VSS), U3.20 (RD2), U3.24 (~ADS), U4.23 (~EN), U4.25 (GND)
IRQ_COM1: U1.30 (INTRPT)
IRQ_COM2: U3.30 (INTRPT)
MAX_VN1: C6.1, U2.3 (V-)
MAX_VN2: C14.1, U4.3 (V-)
MAX_VP1: C5.1, U2.27 (V+)
MAX_VP2: C13.1, U4.27 (V+)
RESET_DRV: U1.35 (MR), U3.35 (MR)
RS_CTS1: J1.8, U2.5 (R2IN)
RS_CTS2: J2.8, U4.5 (R2IN)
RS_DCD1: J1.1, U2.7 (R4IN)
RS_DCD2: J2.1, U4.7 (R4IN)
RS_DSR1: J1.6, U2.6 (R3IN)
RS_DSR2: J2.6, U4.6 (R3IN)
RS_DTR1: J1.4, U2.11 (T3OUT)
RS_DTR2: J2.4, U4.11 (T3OUT)
RS_RI1: J1.9, U2.8 (R5IN)
RS_RI2: J2.9, U4.8 (R5IN)
RS_RTS1: J1.7, U2.10 (T2OUT)
RS_RTS2: J2.7, U4.10 (T2OUT)
RS_RXD1: J1.2, U2.4 (R1IN)
RS_RXD2: J2.2, U4.4 (R1IN)
RS_TXD1: J1.3, U2.9 (T1OUT)
RS_TXD2: J2.3, U4.9 (T1OUT)
RXD_RS232: JP1.1, U2.19 (R1OUT)
UART_CTS1: U1.38 (~CTS), U2.18 (R2OUT)
UART_CTS2: U3.38 (~CTS), U4.18 (R2OUT)
UART_DCD1: U1.40 (~DCD), U2.16 (R4OUT)
UART_DCD2: U3.40 (~DCD), U4.16 (R4OUT)
UART_DSR1: U1.39 (~DSR), U2.17 (R3OUT)
UART_DSR2: U3.39 (~DSR), U4.17 (R3OUT)
UART_DTR1: U1.33 (~DTR), U2.12 (T3IN)
UART_DTR2: U3.33 (~DTR), U4.12 (T3IN)
UART_RI1: U1.41 (~RI), U2.15 (R5OUT)
UART_RI2: U3.41 (~RI), U4.15 (R5OUT)
UART_RTS1: U1.32 (~RTS), U2.13 (T2IN)
UART_RTS2: U3.32 (~RTS), U4.13 (T2IN)
UART_RXD1: JP1.2, R3.2, U1.7 (SIN)
UART_RXD2: U3.7 (SIN), U4.19 (R1OUT)
UART_TXD1: J3.2, U1.8 (SOUT), U2.14 (T1IN)
UART_TXD2: U3.8 (SOUT), U4.14 (T1IN)
~COM1_CS: U1.11 (~CS2)
~COM1_IRQEN: U1.31 (~OUT2)
~COM2_CS: U3.11 (~CS2)
~COM2_IRQEN: U3.31 (~OUT2)
~IOR: U1.19 (~RD1), U3.19 (~RD1)
~IOW: U1.16 (~WR1), U3.16 (~WR1)

Notes on the sheet:
Chip selects, IRQ mapping (COM1=IRQ4, COM2=IRQ3) and the disable jumpers all live on the addr_decode sheet
JP1 selects COM1 UART RX source: 1-2 DB9, 2-3 TTL console (J3, 3.3V levels)
