vaelen/mini-xt/hardware/sheets/cpu_core.kicad_sch

## KiCad design hardware/sheets/cpu_core.kicad_sch (2026-07-23)

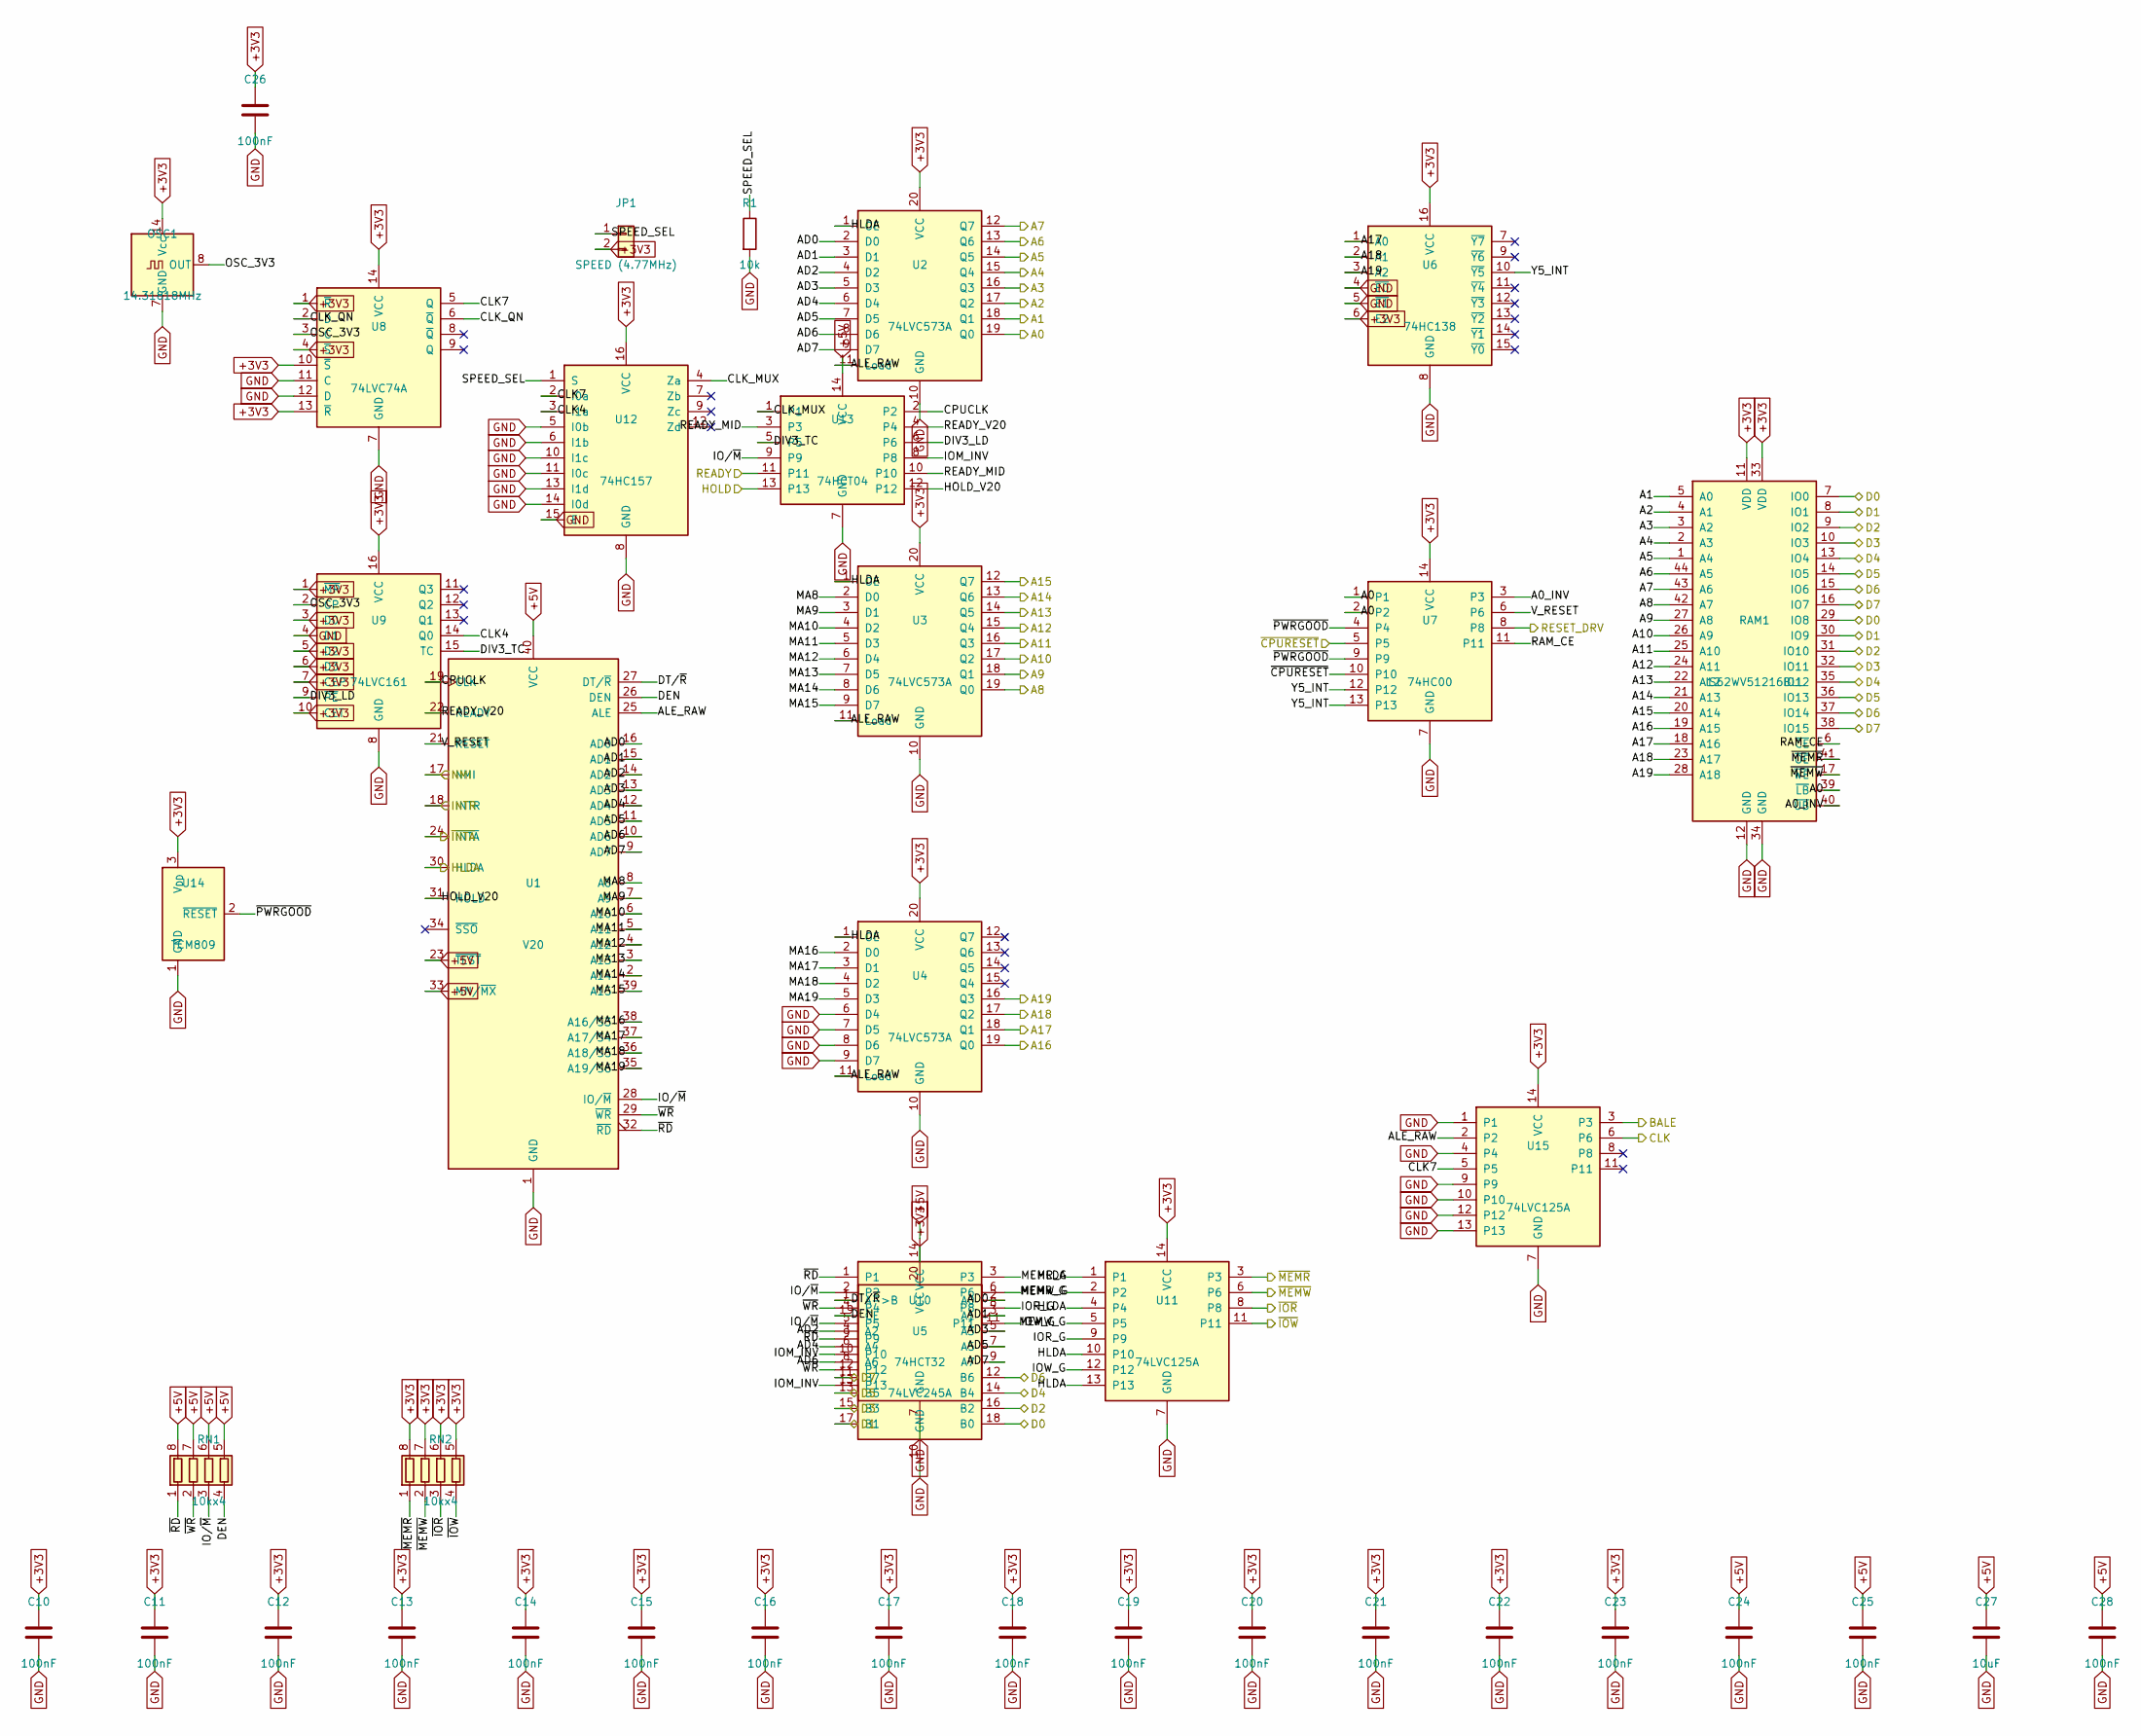
[picture p26: schematic cpu_core.kicad_sch]

Parts:
C10, C11, C12, C13, C14, C15, C16, C17, C18, C19, C20, C21, C22, C23, C24, C25, C26, C28: 100nF; C_0603_1608Metric; LCSC Part Num C14663
C27: 10uF; C_0805_2012Metric; LCSC Part Num C15850
JP1: SPEED (4.77MHz); PinHeader_1x02_P2.54mm_Vertical; LCSC Part Num C492401
OSC1: 14.31818MHz; Oscillator_SMD_EuroQuartz_XO32-4Pin_3.2x2.5mm; LCSC Part Num C49330311
R1: 10k; R_0805_2012Metric; LCSC Part Num C17414
RAM1: IS62WV51216BLL; TSOP-II-44_10.16x18.41mm_P0.8mm; LCSC Part Num C11315
RN1, RN2: 10kx4; R_Array_Convex_4x0603; LCSC Part Num C29718
U1: V20; DIP-40_W15.24mm_Socket; LCSC Part Num C2874018
U2, U3, U4: 74LVC573A; TSSOP-20_4.4x6.5mm_P0.65mm; LCSC Part Num C6096
U5: 74LVC245A; TSSOP-20_4.4x6.5mm_P0.65mm; LCSC Part Num C6082
U6: 74HC138; SOIC-16_3.9x9.9mm_P1.27mm; LCSC Part Num C5602
U7: 74HC00; SOIC-14_3.9x8.7mm_P1.27mm; LCSC Part Num C699445
U8: 74LVC74A; TSSOP-14_4.4x5mm_P0.65mm; LCSC Part Num C6100
U9: 74LVC161; TSSOP-16_4.4x5mm_P0.65mm; LCSC Part Num C548136
U10: 74HCT32; SOIC-14_3.9x8.7mm_P1.27mm; LCSC Part Num C5985
U11, U15: 74LVC125A; SOIC-14_3.9x8.7mm_P1.27mm; LCSC Part Num C6057
U12: 74HC157; SOIC-16_3.9x9.9mm_P1.27mm; LCSC Part Num C5609
U13: 74HCT04; SOIC-14_3.9x8.7mm_P1.27mm; LCSC Part Num C672096
U14: TCM809; SOT-23; LCSC Part Num C47195

Connections:
+3V3: C10.1, C11.1, C12.1, C13.1, C14.1, C15.1, C16.1, C17.1, C18.1, C19.1, C20.1, C21.1, C22.1, C23.1, C26.1, JP1.2, OSC1.14 (Vcc), RAM1.11 (VDD), RAM1.33 (VDD), RN2.5 (R4.2), RN2.6 (R3.2), RN2.7 (R2.2), RN2.8 (R1.2), U2.20 (VCC), U3.20 (VCC), U4.20 (VCC), U5.20 (VCC), U6.6 (E2), U6.16 (VCC), U7.14 (VCC), U8.1 (~R), U8.4 (~S), U8.10 (~S), U8.13 (~R), U8.14 (VCC), U9.1 (~MR), U9.3 (D0), U9.5 (D2), U9.6 (D3), U9.7 (CEP), U9.10 (CET), U9.16 (VCC), U11.14 (VCC), U12.16 (VCC), U14.3 (V_{DD}), U15.14 (VCC)
+5V: C24.1, C25.1, C27.1, C28.1, RN1.5 (R4.2), RN1.6 (R3.2), RN1.7 (R2.2), RN1.8 (R1.2), U1.23 (~TEST), U1.33 (MN/~MX), U1.40 (VCC), U10.14 (VCC), U13.14 (VCC)
A0: RAM1.39 (~LB), U2.19 (Q0), U7.1, U7.2
A0_INV: RAM1.40 (~UB), U7.3
A1: RAM1.5 (A0), U2.18 (Q1)
A2: RAM1.4 (A1), U2.17 (Q2)
A3: RAM1.3 (A2), U2.16 (Q3)
A4: RAM1.2 (A3), U2.15 (Q4)
A5: RAM1.1 (A4), U2.14 (Q5)
A6: RAM1.44 (A5), U2.13 (Q6)
A7: RAM1.43 (A6), U2.12 (Q7)
A8: RAM1.42 (A7), U3.19 (Q0)
A9: RAM1.27 (A8), U3.18 (Q1)
A10: RAM1.26 (A9), U3.17 (Q2)
A11: RAM1.25 (A10), U3.16 (Q3)
A12: RAM1.24 (A11), U3.15 (Q4)
A13: RAM1.22 (A12), U3.14 (Q5)
A14: RAM1.21 (A13), U3.13 (Q6)
A15: RAM1.20 (A14), U3.12 (Q7)
A16: RAM1.19 (A15), U4.19 (Q0)
A17: RAM1.18 (A16), U4.18 (Q1), U6.1 (A0)
A18: RAM1.23 (A17), U4.17 (Q2), U6.2 (A1)
A19: RAM1.28 (A18), U4.16 (Q3), U6.3 (A2)
AD0: U1.16 (AD0), U2.2 (D0), U5.2 (A0)
AD1: U1.15 (AD1), U2.3 (D1), U5.3 (A1)
AD2: U1.14 (AD2), U2.4 (D2), U5.4 (A2)
AD3: U1.13 (AD3), U2.5 (D3), U5.5 (A3)
AD4: U1.12 (AD4), U2.6 (D4), U5.6 (A4)
AD5: U1.11 (AD5), U2.7 (D5), U5.7 (A5)
AD6: U1.10 (AD6), U2.8 (D6), U5.8 (A6)
AD7: U1.9 (AD7), U2.9 (D7), U5.9 (A7)
ALE_RAW: U1.25 (ALE), U2.11 (Load), U3.11 (Load), U4.11 (Load), U15.2
BALE: U15.3
CLK: U15.6
CLK4: U9.14 (Q0), U12.3 (I1a)
CLK7: U8.5 (Q), U12.2 (I0a), U15.5
CLK_MUX: U12.4 (Za), U13.1
CLK_QN: U8.2 (D), U8.6 (~Q)
CPUCLK: U1.19 (CLK), U13.2
D0: RAM1.7 (IO0), RAM1.29 (IO8), U5.18 (B0)
D1: RAM1.8 (IO1), RAM1.30 (IO9), U5.17 (B1)
D2: RAM1.9 (IO2), RAM1.31 (IO10), U5.16 (B2)
D3: RAM1.10 (IO3), RAM1.32 (IO11), U5.15 (B3)
D4: RAM1.13 (IO4), RAM1.35 (IO12), U5.14 (B4)
D5: RAM1.14 (IO5), RAM1.36 (IO13), U5.13 (B5)
D6: RAM1.15 (IO6), RAM1.37 (IO14), U5.12 (B6)
D7: RAM1.16 (IO7), RAM1.38 (IO15), U5.11 (B7)
DEN: RN1.4 (R4.1), U1.26 (DEN), U5.19 (CE)
DIV3_LD: U9.9 (~PE), U13.6
DIV3_TC: U9.15 (TC), U13.5
DT/~R: U1.27 (DT/~R), U5.1 (A->B)
GND: C10.2, C11.2, C12.2, C13.2, C14.2, C15.2, C16.2, C17.2, C18.2, C19.2, C20.2, C21.2, C22.2, C23.2, C24.2, C25.2, C26.2, C27.2, C28.2, OSC1.7 (GND), R1.2, RAM1.12 (GND), RAM1.34 (GND), U1.1 (GND), U1.20 (GND), U2.10 (GND), U3.10 (GND), U4.6 (D4), U4.7 (D5), U4.8 (D6), U4.9 (D7), U4.10 (GND), U5.10 (GND), U6.4 (~E0), U6.5 (~E1), U6.8 (GND), U7.7 (GND), U8.7 (GND), U8.11 (C), U8.12 (D), U9.4 (D1), U9.8 (GND), U10.7 (GND), U11.7 (GND), U12.5 (I0b), U12.6 (I1b), U12.8 (GND), U12.10 (I1c), U12.11 (I0c), U12.13 (I1d), U12.14 (I0d), U12.15 (E), U13.7 (GND), U14.1 (GND), U15.1, U15.4, U15.7 (GND), U15.9, U15.10, U15.12, U15.13
HLDA: U1.30 (HLDA), U2.1 (OE), U3.1 (OE), U4.1 (OE), U11.1, U11.4, U11.10, U11.13
HOLD: U13.13
HOLD_V20: U1.31 (HOLD), U13.12
INTR: U1.18 (INTR)
IO/~M: RN1.3 (R3.1), U1.28 (IO/~M), U10.2, U10.5, U13.9
IOM_INV: U10.10, U10.13, U13.8
IOR_G: U10.8, U11.9
IOW_G: U10.11, U11.12
MA8: U1.8 (A8), U3.2 (D0)
MA9: U1.7 (A9), U3.3 (D1)
MA10: U1.6 (A10), U3.4 (D2)
MA11: U1.5 (A11), U3.5 (D3)
MA12: U1.4 (A12), U3.6 (D4)
MA13: U1.3 (A13), U3.7 (D5)
MA14: U1.2 (A14), U3.8 (D6)
MA15: U1.39 (A15), U3.9 (D7)
MA16: U1.38 (A16/S3), U4.2 (D0)
MA17: U1.37 (A17/S4), U4.3 (D1)
MA18: U1.36 (A18/S5), U4.4 (D2)
MA19: U1.35 (A19/S6), U4.5 (D3)
MEMR_G: U10.3, U11.2
MEMW_G: U10.6, U11.5
NMI: U1.17 (NMI)
OSC_3V3: OSC1.8 (OUT), U8.3 (C), U9.2 (CP)
RAM_CE: RAM1.6 (~CE), U7.11
READY: U13.11
READY_MID: U13.3, U13.10
READY_V20: U1.22 (READY), U13.4
RESET_DRV: U7.8
SPEED_SEL: JP1.1, R1.1, U12.1 (S)
V_RESET: U1.21 (RESET), U7.6
Y5_INT: U6.10 (~Y5), U7.12, U7.13
~CPURESET: U7.5, U7.10
~INTA: U1.24 (~INTA)
~IOR: RN2.3 (R3.1), U11.8
~IOW: RN2.4 (R4.1), U11.11
~MEMR: RAM1.41 (~OE), RN2.1 (R1.1), U11.3
~MEMW: RAM1.17 (~WE), RN2.2 (R2.1), U11.6
~PWRGOOD: U7.4, U7.9, U14.2 (~RESET)
~RD: RN1.1 (R1.1), U1.32 (~RD), U10.1, U10.9
~WR: RN1.2 (R2.1), U1.29 (~WR), U10.4, U10.12
