vaelen/mini-xt/hardware/sheets/parallel.kicad_sch

## KiCad design hardware/sheets/parallel.kicad_sch (2026-07-23)

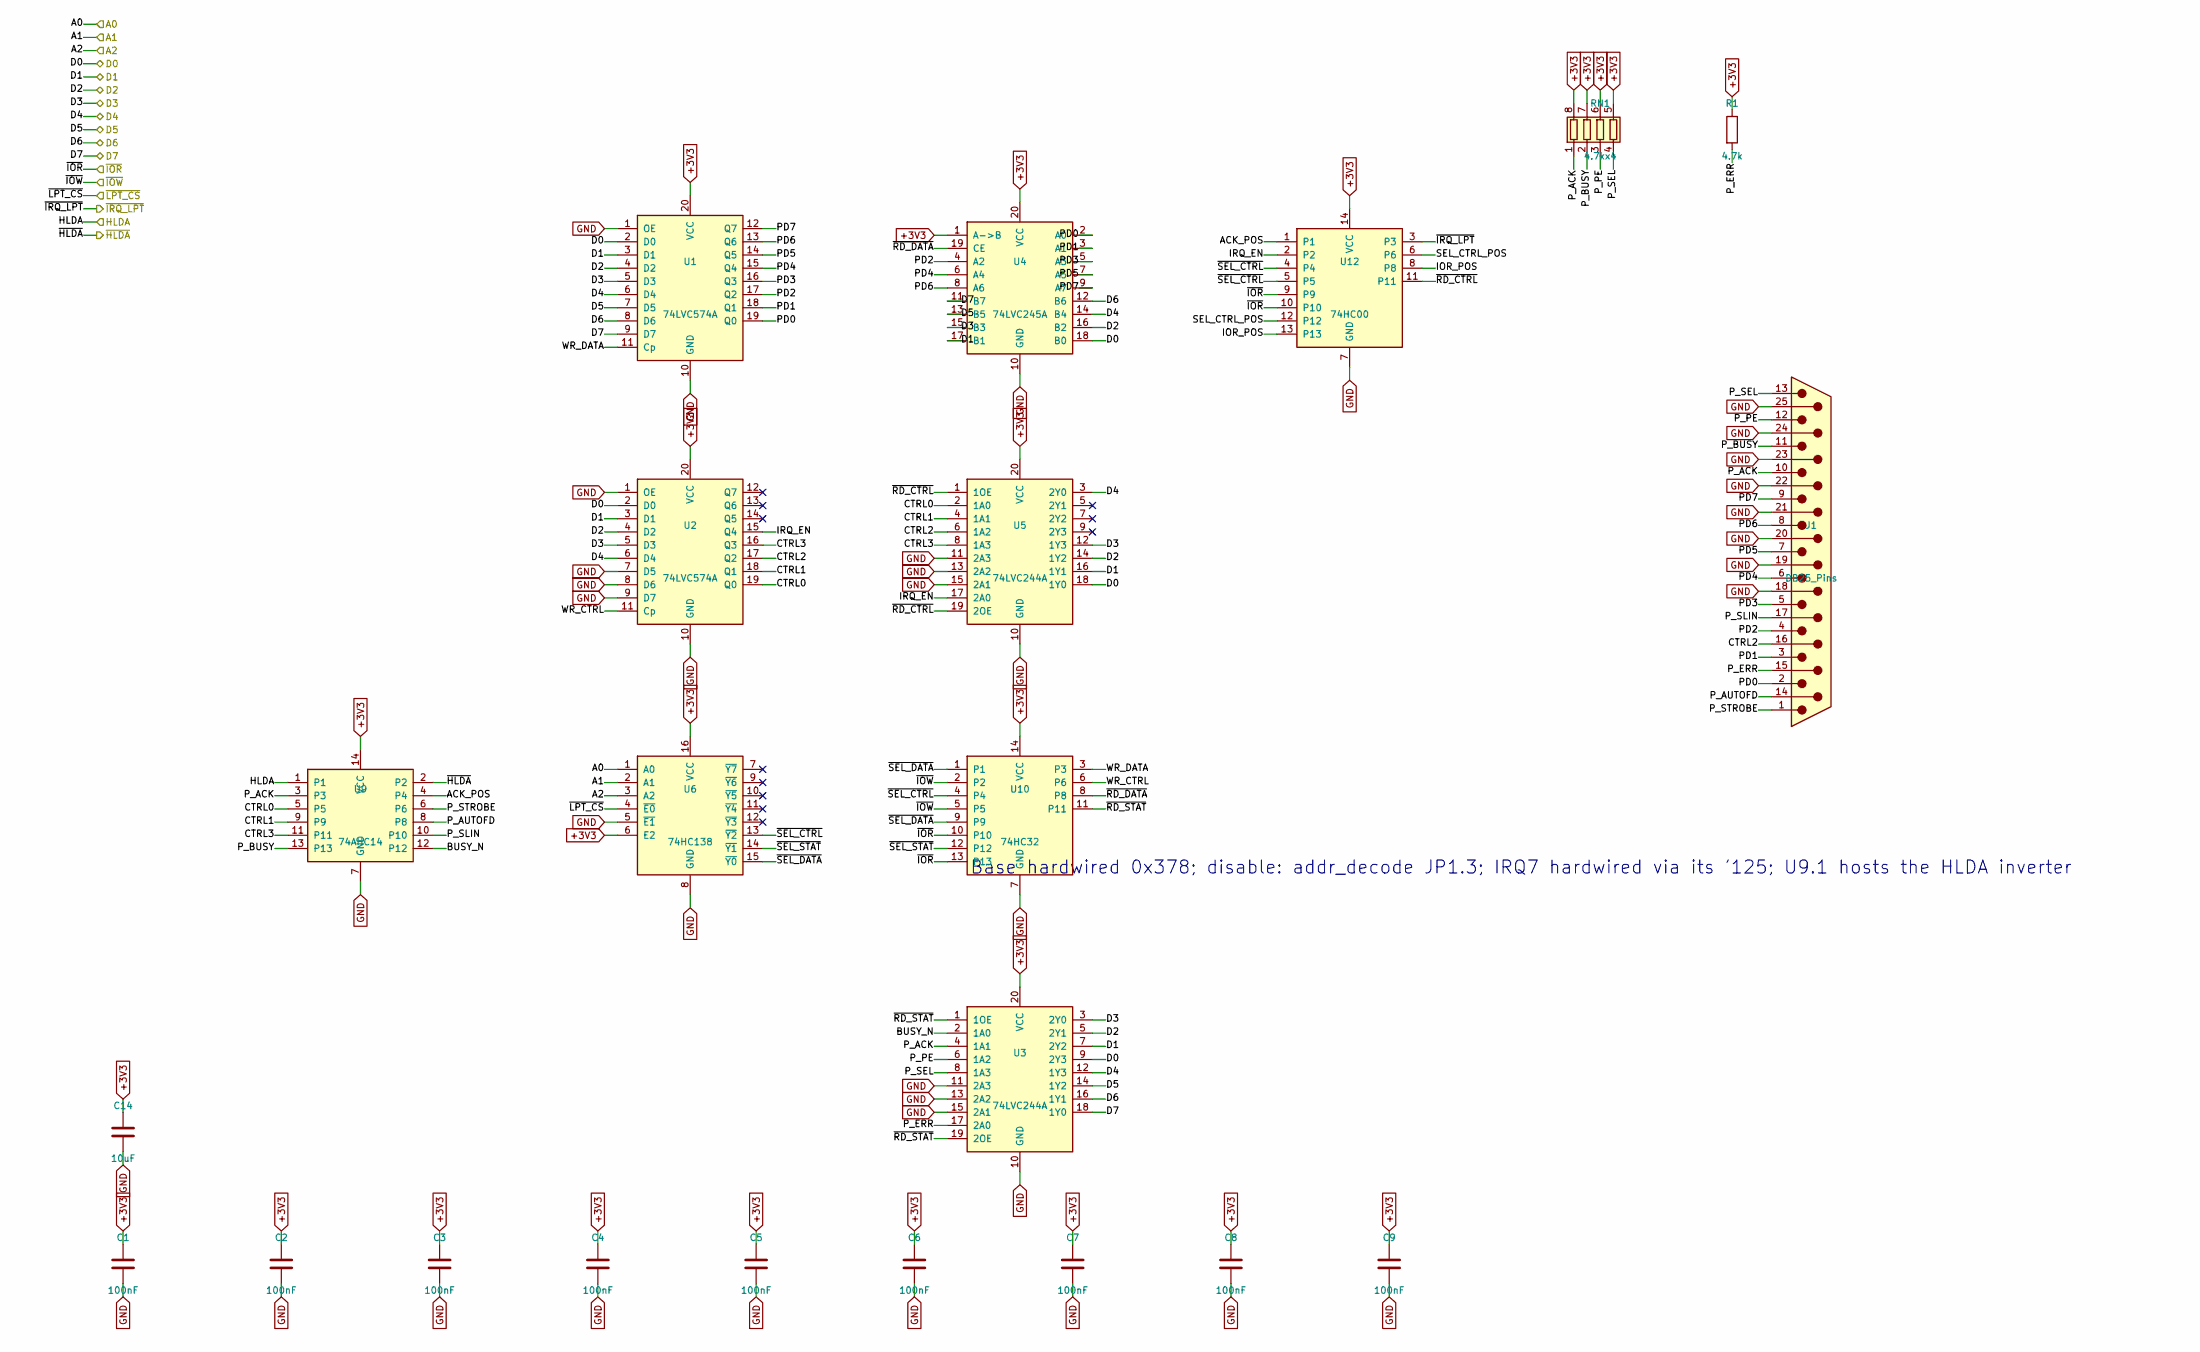
[picture p27: schematic parallel.kicad_sch]

Parts:
C1, C2, C3, C4, C5, C6, C7, C8, C9: 100nF; C_0603_1608Metric; LCSC Part Num C14663
C14: 10uF; C_0805_2012Metric; LCSC Part Num C15850
J1: DB25_Pins; DSUB-25_Socket_Horizontal_P2.77x2.84mm_EdgePinOffset9.90mm_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; LCSC Part Num C190083
R1: 4.7k; R_0603_1608Metric; LCSC Part Num C23162
RN1: 4.7kx4; R_Array_Convex_4x0603; LCSC Part Num C1980
U1, U2: 74LVC574A; TSSOP-20_4.4x6.5mm_P0.65mm; LCSC Part Num C842658
U3, U5: 74LVC244A; TSSOP-20_4.4x6.5mm_P0.65mm; LCSC Part Num C6079
U4: 74LVC245A; TSSOP-20_4.4x6.5mm_P0.65mm; LCSC Part Num C6082
U6: 74HC138; SOIC-16_3.9x9.9mm_P1.27mm; LCSC Part Num C5602
U9: 74AHC14; TSSOP-14_4.4x5mm_P0.65mm; LCSC Part Num C54561786
U10: 74HC32; SOIC-14_3.9x8.7mm_P1.27mm; LCSC Part Num C52140395
U12: 74HC00; SOIC-14_3.9x8.7mm_P1.27mm; LCSC Part Num C699445

Connections:
+3V3: C1.1, C2.1, C3.1, C4.1, C5.1, C6.1, C7.1, C8.1, C9.1, C14.1, R1.1, RN1.5 (R4.2), RN1.6 (R3.2), RN1.7 (R2.2), RN1.8 (R1.2), U1.20 (VCC), U2.20 (VCC), U3.20 (VCC), U4.1 (A->B), U4.20 (VCC), U5.20 (VCC), U6.6 (E2), U6.16 (VCC), U9.14 (VCC), U10.14 (VCC), U12.14 (VCC)
A0: U6.1 (A0)
A1: U6.2 (A1)
A2: U6.3 (A2)
ACK_POS: U9.4, U12.1
BUSY_N: U3.2 (1A0), U9.12
CTRL0: U2.19 (Q0), U5.2 (1A0), U9.5
CTRL1: U2.18 (Q1), U5.4 (1A1), U9.9
CTRL2: J1.16, U2.17 (Q2), U5.6 (1A2)
CTRL3: U2.16 (Q3), U5.8 (1A3), U9.11
D0: U1.2 (D0), U2.2 (D0), U3.9 (2Y3), U4.18 (B0), U5.18 (1Y0)
D1: U1.3 (D1), U2.3 (D1), U3.7 (2Y2), U4.17 (B1), U5.16 (1Y1)
D2: U1.4 (D2), U2.4 (D2), U3.5 (2Y1), U4.16 (B2), U5.14 (1Y2)
D3: U1.5 (D3), U2.5 (D3), U3.3 (2Y0), U4.15 (B3), U5.12 (1Y3)
D4: U1.6 (D4), U2.6 (D4), U3.12 (1Y3), U4.14 (B4), U5.3 (2Y0)
D5: U1.7 (D5), U3.14 (1Y2), U4.13 (B5)
D6: U1.8 (D6), U3.16 (1Y1), U4.12 (B6)
D7: U1.9 (D7), U3.18 (1Y0), U4.11 (B7)
GND: C1.2, C2.2, C3.2, C4.2, C5.2, C6.2, C7.2, C8.2, C9.2, C14.2, J1.18, J1.19, J1.20, J1.21, J1.22, J1.23, J1.24, J1.25, U1.1 (OE), U1.10 (GND), U2.1 (OE), U2.7 (D5), U2.8 (D6), U2.9 (D7), U2.10 (GND), U3.10 (GND), U3.11 (2A3), U3.13 (2A2), U3.15 (2A1), U4.10 (GND), U5.10 (GND), U5.11 (2A3), U5.13 (2A2), U5.15 (2A1), U6.5 (~E1), U6.8 (GND), U9.7 (GND), U10.7 (GND), U12.7 (GND)
HLDA: U9.1
IOR_POS: U12.8, U12.13
IRQ_EN: U2.15 (Q4), U5.17 (2A0), U12.2
PD0: J1.2, U1.19 (Q0), U4.2 (A0)
PD1: J1.3, U1.18 (Q1), U4.3 (A1)
PD2: J1.4, U1.17 (Q2), U4.4 (A2)
PD3: J1.5, U1.16 (Q3), U4.5 (A3)
PD4: J1.6, U1.15 (Q4), U4.6 (A4)
PD5: J1.7, U1.14 (Q5), U4.7 (A5)
PD6: J1.8, U1.13 (Q6), U4.8 (A6)
PD7: J1.9, U1.12 (Q7), U4.9 (A7)
P_ACK: J1.10, RN1.1 (R1.1), U3.4 (1A1), U9.3
P_AUTOFD: J1.14, U9.8
P_BUSY: J1.11, RN1.2 (R2.1), U9.13
P_ERR: J1.15, R1.2, U3.17 (2A0)
P_PE: J1.12, RN1.3 (R3.1), U3.6 (1A2)
P_SEL: J1.13, RN1.4 (R4.1), U3.8 (1A3)
P_SLIN: J1.17, U9.10
P_STROBE: J1.1, U9.6
SEL_CTRL_POS: U12.6, U12.12
WR_CTRL: U2.11 (Cp), U10.6
WR_DATA: U1.11 (Cp), U10.3
~HLDA: U9.2
~IOR: U10.10, U10.13, U12.9, U12.10
~IOW: U10.2, U10.5
~IRQ_LPT: U12.3
~LPT_CS: U6.4 (~E0)
~RD_CTRL: U5.1 (1OE), U5.19 (2OE), U12.11
~RD_DATA: U4.19 (CE), U10.8
~RD_STAT: U3.1 (1OE), U3.19 (2OE), U10.11
~SEL_CTRL: U6.13 (~Y2), U10.4, U12.4, U12.5
~SEL_DATA: U6.15 (~Y0), U10.1, U10.9
~SEL_STAT: U6.14 (~Y1), U10.12

Notes on the sheet:
Base hardwired 0x378; disable: addr_decode JP1.3; IRQ7 hardwired via its '125; U9.1 hosts the HLDA inverter
