vaelen/mini-xt/hardware/sheets/picogus.kicad_sch

## KiCad design hardware/sheets/picogus.kicad_sch (2026-07-23)

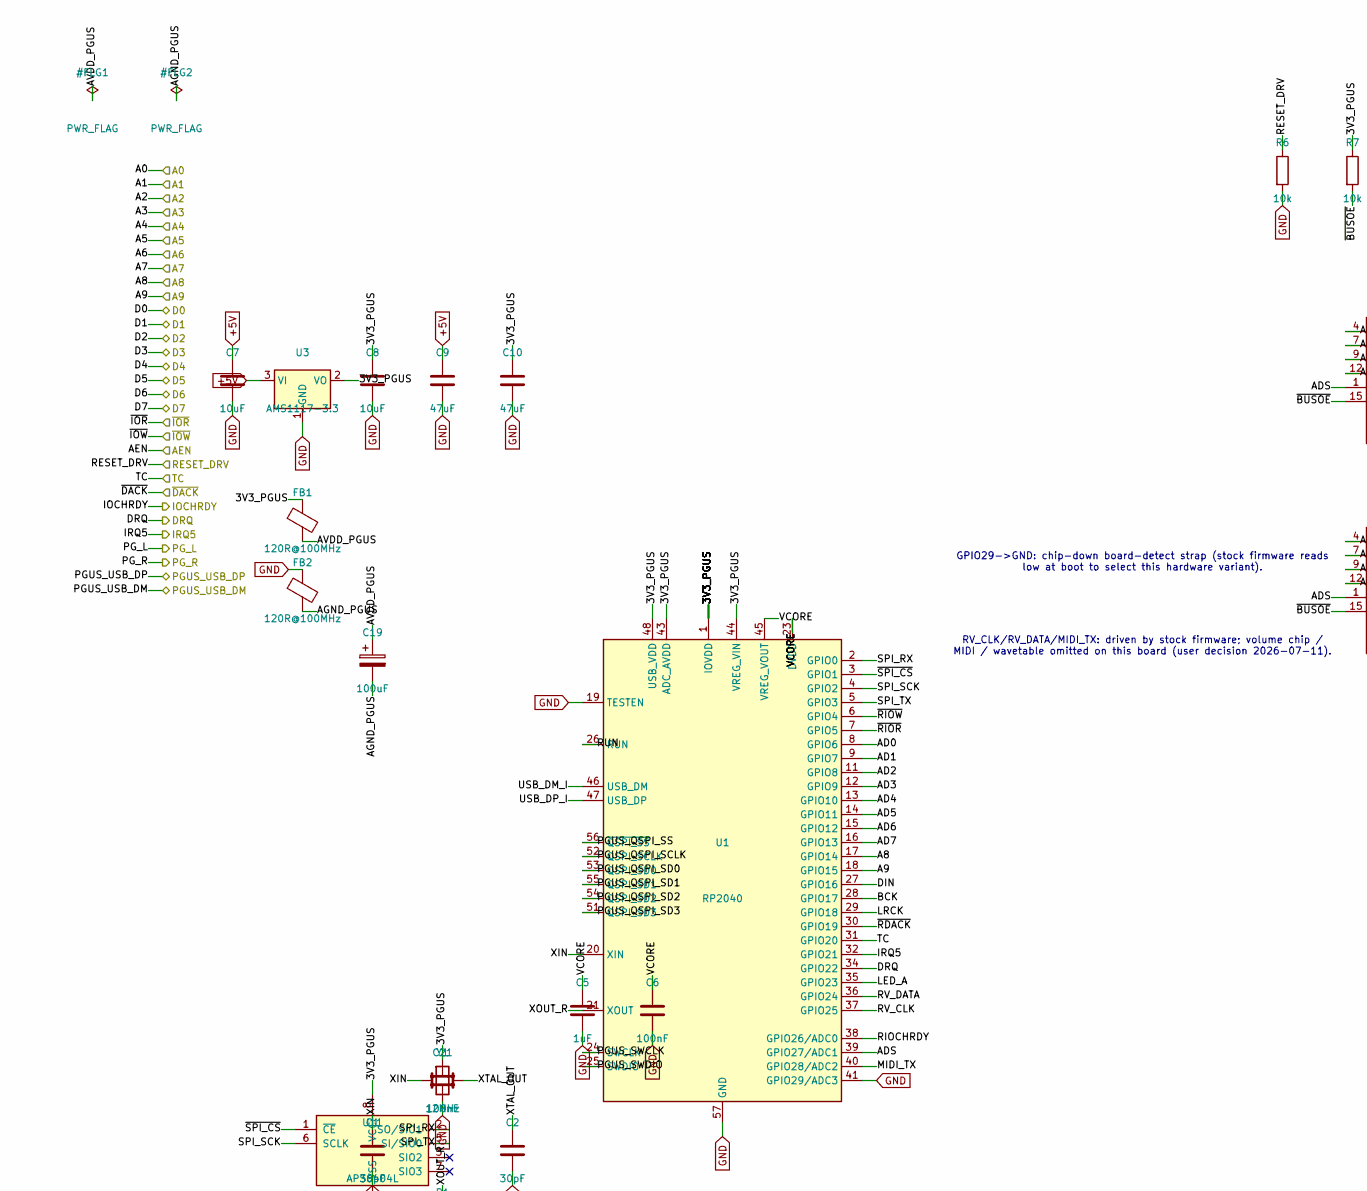
[picture p28: schematic picogus.kicad_sch, part in row 1, column 1]

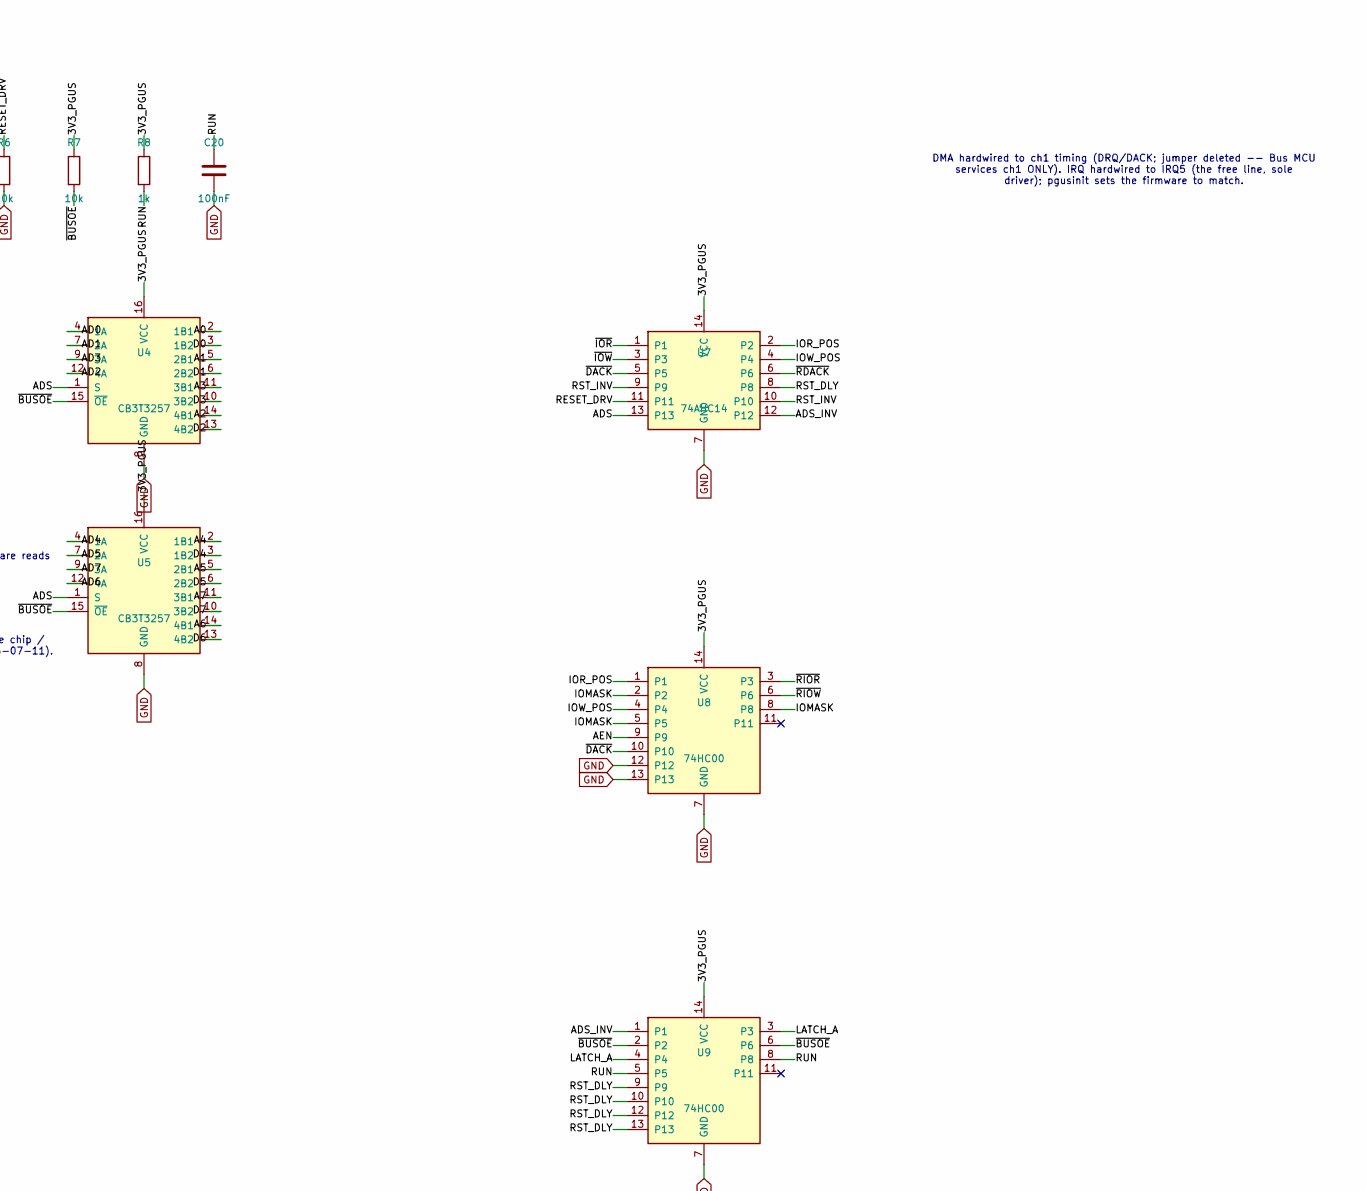
[picture p29: schematic picogus.kicad_sch, part in row 1, column 2]

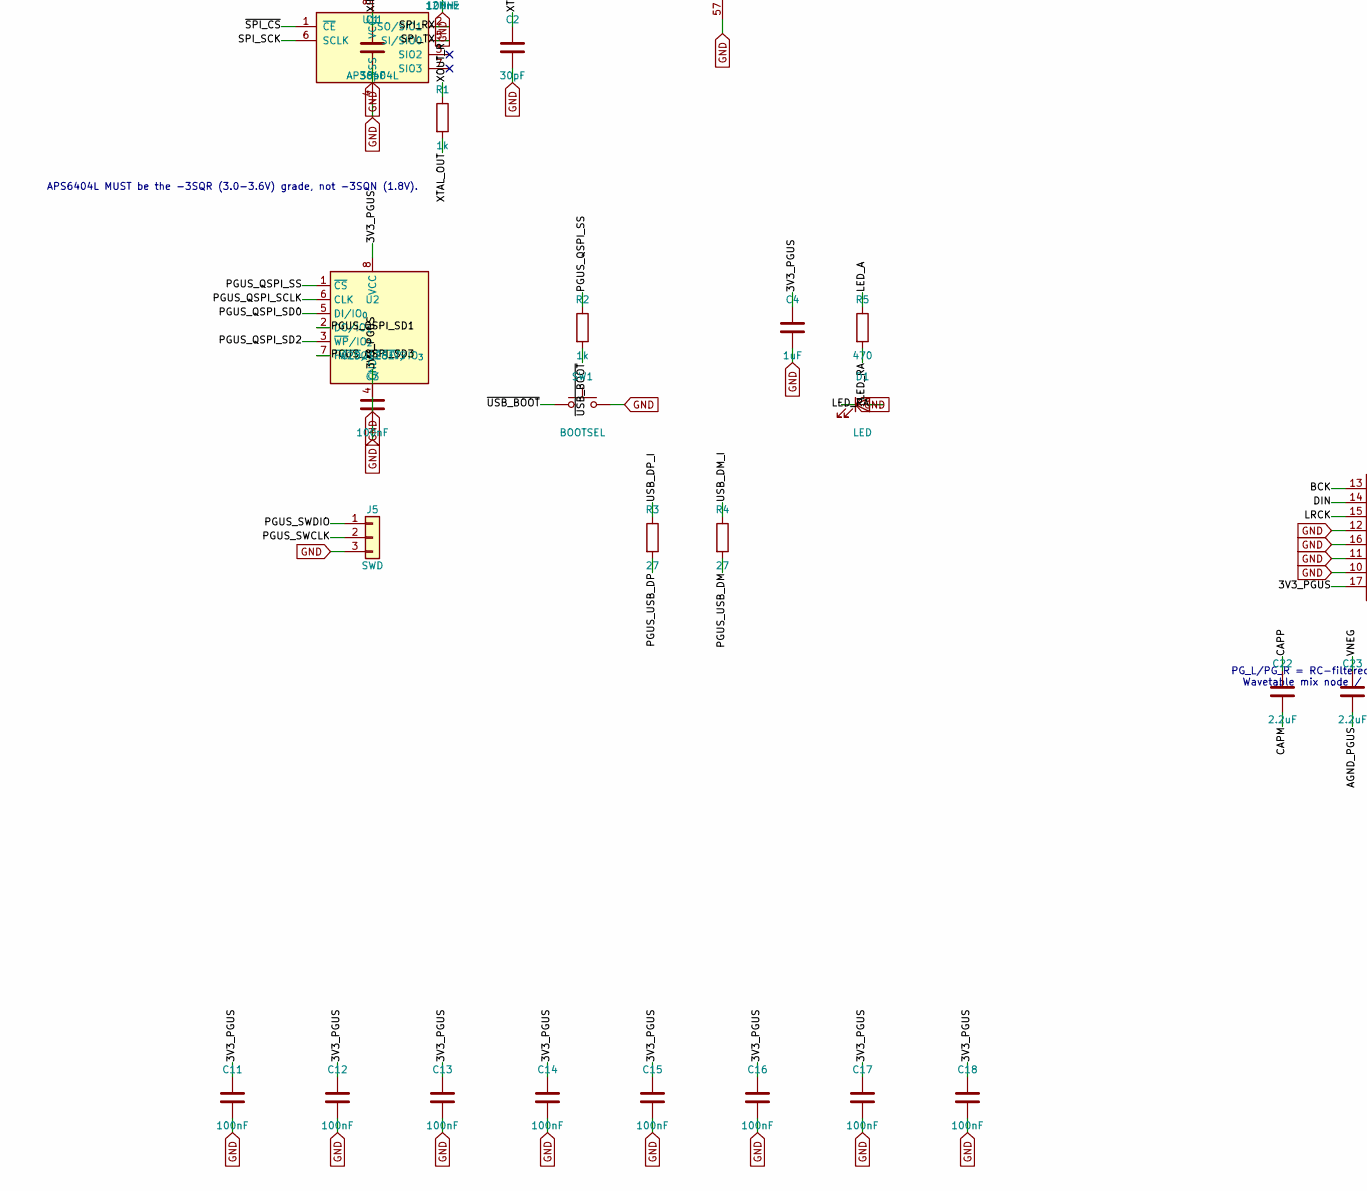
[picture p30: schematic picogus.kicad_sch, part in row 2, column 1]

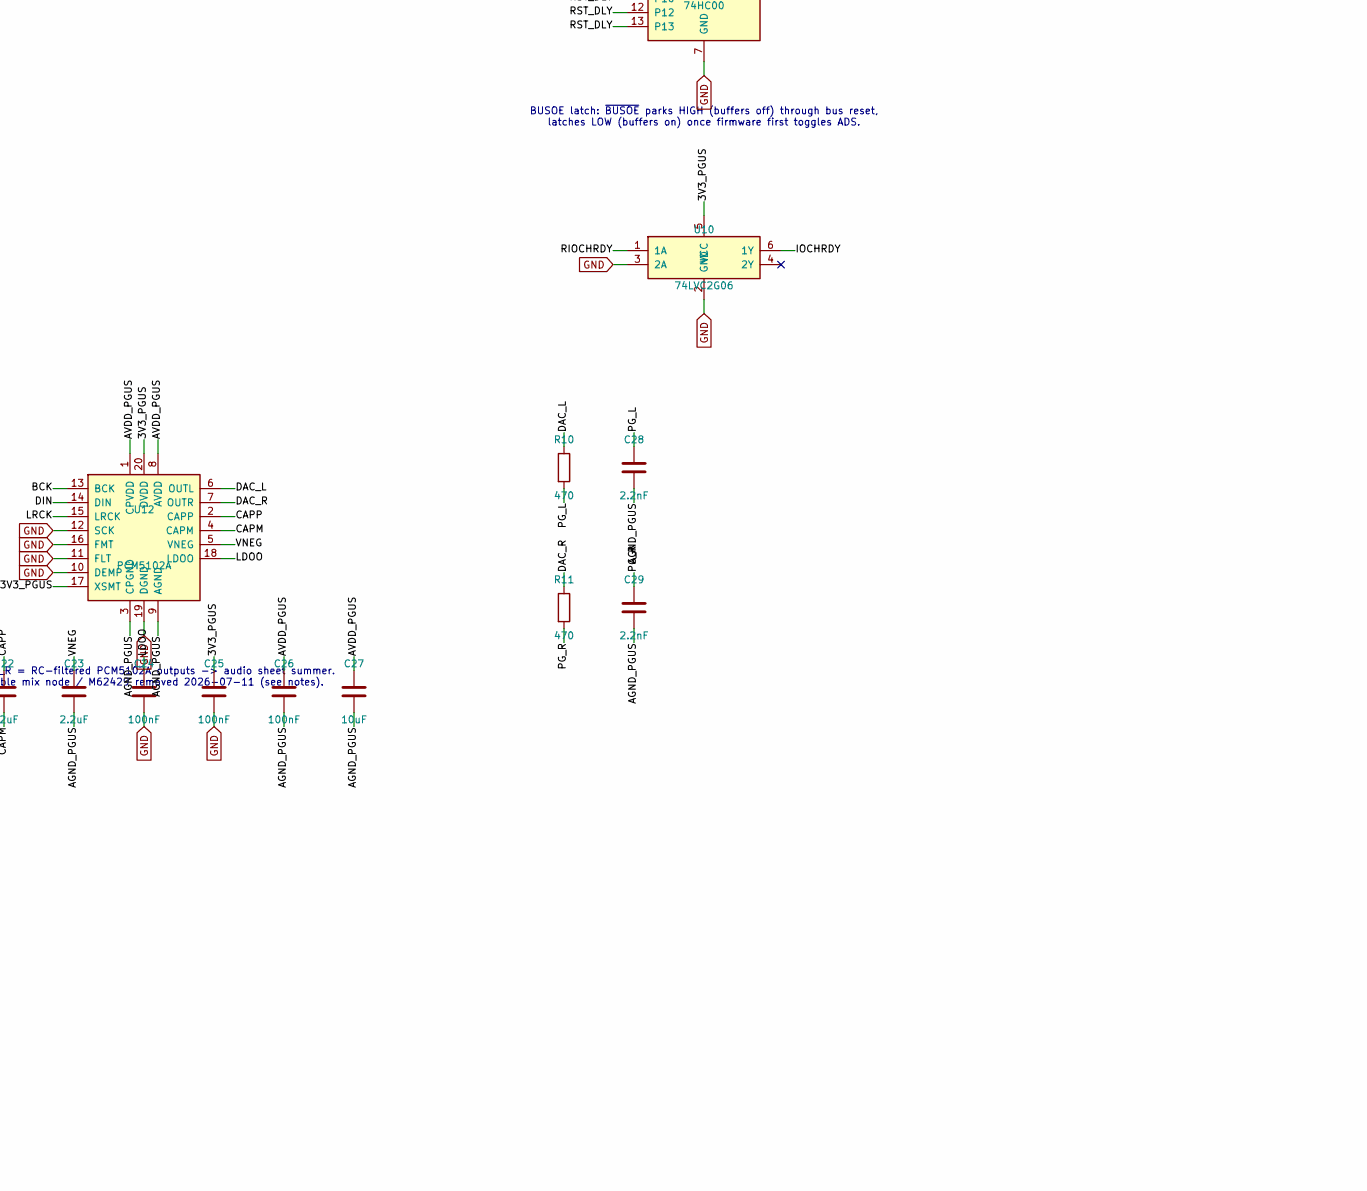
[picture p31: schematic picogus.kicad_sch, part in row 2, column 2]

Parts:
C1, C2: 30pF; C_0603_1608Metric; LCSC Part Num C1658
C3, C6, C11, C12, C13, C14, C15, C16, C17, C18, C20, C21, C24, C25, C26: 100nF; C_0603_1608Metric; LCSC Part Num C14663
C4, C5: 1uF; C_0603_1608Metric; LCSC Part Num C15849
C7, C8, C27: 10uF; C_0805_2012Metric; LCSC Part Num C15850
C9, C10: 47uF; C_0805_2012Metric; LCSC Part Num C16780
C19: 100uF; CP_Elec_6.3x5.4; LCSC Part Num C2887276
C22, C23: 2.2uF; C_0603_1608Metric; LCSC Part Num C23630
C28, C29: 2.2nF; C_0603_1608Metric; LCSC Part Num C1604
D1: LED; LED_0603_1608Metric; LCSC Part Num C2286
FB1, FB2: 120R@100MHz; L_0603_1608Metric; LCSC Part Num C14709
J5: SWD; PinHeader_1x03_P2.54mm_Vertical; LCSC Part Num C2337
R1, R2, R8: 1k; R_0603_1608Metric; LCSC Part Num C21190
R3, R4: 27; R_0603_1608Metric; LCSC Part Num C25190
R5, R10, R11: 470; R_0603_1608Metric; LCSC Part Num C23179
R6, R7: 10k; R_0805_2012Metric; LCSC Part Num C17414
SW1: BOOTSEL; SW_TS-1187A_5.1x5.1mm; LCSC Part Num C318884
U1: RP2040; QFN-56-1EP_7x7mm_P0.4mm_EP3.2x3.2mm; LCSC Part Num C2040
U2: W25Q128JVS; SOIC-8_5.3x5.3mm_P1.27mm; LCSC Part Num C97521
U3: AMS1117-3.3; SOT-223-3_TabPin2; LCSC Part Num C6186
U4, U5: CB3T3257; TSSOP-16_4.4x5mm_P0.65mm; LCSC Part Num C544573
U7: 74AHC14; TSSOP-14_4.4x5mm_P0.65mm; LCSC Part Num C54561786
U8, U9: 74HC00; SOIC-14_3.9x8.7mm_P1.27mm; LCSC Part Num C699445
U10: 74LVC2G06; SOT-23-6; LCSC Part Num C52145914
U11: APS6404L; SOIC-8_3.9x4.9mm_P1.27mm; LCSC Part Num C5333729
U12: PCM5102A; TSSOP-20_4.4x6.5mm_P0.65mm; LCSC Part Num C107671
Y1: 12MHz; Crystal_SMD_3225-4Pin_3.2x2.5mm; LCSC Part Num C9002

Connections:
3V3_PGUS: C3.1, C4.1, C8.1, C10.1, C11.1, C12.1, C13.1, C14.1, C15.1, C16.1, C17.1, C18.1, C21.1, C25.1, FB1.1, R7.1, R8.1, U1.1 (IOVDD), U1.10 (IOVDD), U1.22 (IOVDD), U1.33 (IOVDD), U1.42 (IOVDD), U1.43 (ADC_AVDD), U1.44 (VREG_VIN), U1.48 (USB_VDD), U1.49 (IOVDD), U2.8 (VCC), U3.2 (VO), U4.16 (VCC), U5.16 (VCC), U7.14 (VCC), U8.14 (VCC), U9.14 (VCC), U10.5 (VCC), U11.8 (VCC), U12.17 (XSMT), U12.20 (DVDD)
+5V: C7.1, C9.1, U3.3 (VI)
A0: U4.2 (1B1)
A1: U4.5 (2B1)
A2: U4.14 (4B1)
A3: U4.11 (3B1)
A4: U5.2 (1B1)
A5: U5.5 (2B1)
A6: U5.14 (4B1)
A7: U5.11 (3B1)
A8: U1.17 (GPIO14)
A9: U1.18 (GPIO15)
AD0: U1.8 (GPIO6), U4.4 (1A)
AD1: U1.9 (GPIO7), U4.7 (2A)
AD2: U1.11 (GPIO8), U4.12 (4A)
AD3: U1.12 (GPIO9), U4.9 (3A)
AD4: U1.13 (GPIO10), U5.4 (1A)
AD5: U1.14 (GPIO11), U5.7 (2A)
AD6: U1.15 (GPIO12), U5.12 (4A)
AD7: U1.16 (GPIO13), U5.9 (3A)
ADS: U1.39 (GPIO27/ADC1), U4.1 (S), U5.1 (S), U7.13
ADS_INV: U7.12, U9.1
AEN: U8.9
AGND_PGUS: C19.2, C23.2, C26.2, C27.2, C28.2, C29.2, FB2.2, U12.3 (CPGND), U12.9 (AGND)
AVDD_PGUS: C19.1, C26.1, C27.1, FB1.2, U12.1 (CPVDD), U12.8 (AVDD)
BCK: U1.28 (GPIO17), U12.13 (BCK)
CAPM: C22.2, U12.4 (CAPM)
CAPP: C22.1, U12.2 (CAPP)
D0: U4.3 (1B2)
D1: U4.6 (2B2)
D2: U4.13 (4B2)
D3: U4.10 (3B2)
D4: U5.3 (1B2)
D5: U5.6 (2B2)
D6: U5.13 (4B2)
D7: U5.10 (3B2)
DAC_L: R10.1, U12.6 (OUTL)
DAC_R: R11.1, U12.7 (OUTR)
DIN: U1.27 (GPIO16), U12.14 (DIN)
DRQ: U1.34 (GPIO22)
GND: C1.2, C2.2, C3.2, C4.2, C5.2, C6.2, C7.2, C8.2, C9.2, C10.2, C11.2, C12.2, C13.2, C14.2, C15.2, C16.2, C17.2, C18.2, C20.2, C21.2, C24.2, C25.2, D1.1 (K), FB2.1, J5.3, R6.2, SW1.2, U1.19 (TESTEN), U1.41 (GPIO29/ADC3), U1.57 (GND), U2.4 (GND), U3.1 (GND), U4.8 (GND), U5.8 (GND), U7.7 (GND), U8.7 (GND), U8.12, U8.13, U9.7 (GND), U10.2 (GND), U10.3 (2A), U11.4 (VSS), U12.10 (DEMP), U12.11 (FLT), U12.12 (SCK), U12.16 (FMT), U12.19 (DGND)
IOCHRDY: U10.6 (1Y)
IOMASK: U8.2, U8.5, U8.8
IOR_POS: U7.2, U8.1
IOW_POS: U7.4, U8.4
IRQ5: U1.32 (GPIO21)
LATCH_A: U9.3, U9.4
LDOO: C24.1, U12.18 (LDOO)
LED_A: R5.1, U1.35 (GPIO23)
LED_RA: D1.2 (A), R5.2
LRCK: U1.29 (GPIO18), U12.15 (LRCK)
MIDI_TX: U1.40 (GPIO28/ADC2)
PGUS_QSPI_SCLK: U1.52 (QSPI_SCLK), U2.6 (CLK)
PGUS_QSPI_SD0: U1.53 (QSPI_SD0), U2.5 (DI/IO_{0})
PGUS_QSPI_SD1: U1.55 (QSPI_SD1), U2.2 (DO/IO_{1})
PGUS_QSPI_SD2: U1.54 (QSPI_SD2), U2.3 (~WP/IO_{2})
PGUS_QSPI_SD3: U1.51 (QSPI_SD3), U2.7 (~HOLD/~RESET/IO_{3})
PGUS_QSPI_SS: R2.1, U1.56 (~QSPI_SS), U2.1 (~CS)
PGUS_SWCLK: J5.2, U1.24 (SWCLK)
PGUS_SWDIO: J5.1, U1.25 (SWDIO)
PGUS_USB_DM: R4.2
PGUS_USB_DP: R3.2
PG_L: C28.1, R10.2
PG_R: C29.1, R11.2
RESET_DRV: R6.1, U7.11
RIOCHRDY: U1.38 (GPIO26/ADC0), U10.1 (1A)
RST_DLY: U7.8, U9.9, U9.10, U9.12, U9.13
RST_INV: U7.9, U7.10
RUN: C20.1, R8.2, U1.26 (RUN), U9.5, U9.8
RV_CLK: U1.37 (GPIO25)
RV_DATA: U1.36 (GPIO24)
SPI_RX: U1.2 (GPIO0), U11.2 (SO/SIO1)
SPI_SCK: U1.4 (GPIO2), U11.6 (SCLK)
SPI_TX: U1.5 (GPIO3), U11.5 (SI/SIO0)
TC: U1.31 (GPIO20)
USB_DM_I: R4.1, U1.46 (USB_DM)
USB_DP_I: R3.1, U1.47 (USB_DP)
VCORE: C5.1, C6.1, U1.23 (DVDD), U1.45 (VREG_VOUT), U1.50 (DVDD)
VNEG: C23.1, U12.5 (VNEG)
XIN: C1.1, U1.20 (XIN), Y1.1
XOUT_R: R1.1, U1.21 (XOUT)
XTAL_OUT: C2.1, R1.2, Y1.2
~BUSOE: R7.2, U4.15 (~OE), U5.15 (~OE), U9.2, U9.6
~DACK: U7.5, U8.10
~IOR: U7.1
~IOW: U7.3
~RDACK: U1.30 (GPIO19), U7.6
~RIOR: U1.7 (GPIO5), U8.3
~RIOW: U1.6 (GPIO4), U8.6
~SPI_CS: U1.3 (GPIO1), U11.1 (~CE)
~USB_BOOT: R2.2, SW1.1

Notes on the sheet:
GPIO29->GND: chip-down board-detect strap (stock firmware reads low at boot to select this hardware variant).
RV_CLK/RV_DATA/MIDI_TX: driven by stock firmware; volume chip / MIDI / wavetable omitted on this board (user decision 2026-07-11).
BUSOE latch: ~{BUSOE} parks HIGH (buffers off) through bus reset, latches LOW (buffers on) once firmware first toggles ADS.
DMA hardwired to ch1 timing (DRQ/DACK; jumper deleted -- Bus MCU services ch1 ONLY). IRQ hardwired to IRQ5 (the free line, sole driver); pgusinit sets the firmware to match.
APS6404L MUST be the -3SQR (3.0-3.6V) grade, not -3SQN (1.8V).
PG_L/PG_R = RC-filtered PCM5102A outputs -> audio sheet summer. Wavetable mix node / M62429 removed 2026-07-11 (see notes).
