vaelen/mini-xt/hardware/sheets/power.kicad_sch

## KiCad design hardware/sheets/power.kicad_sch (2026-07-23)

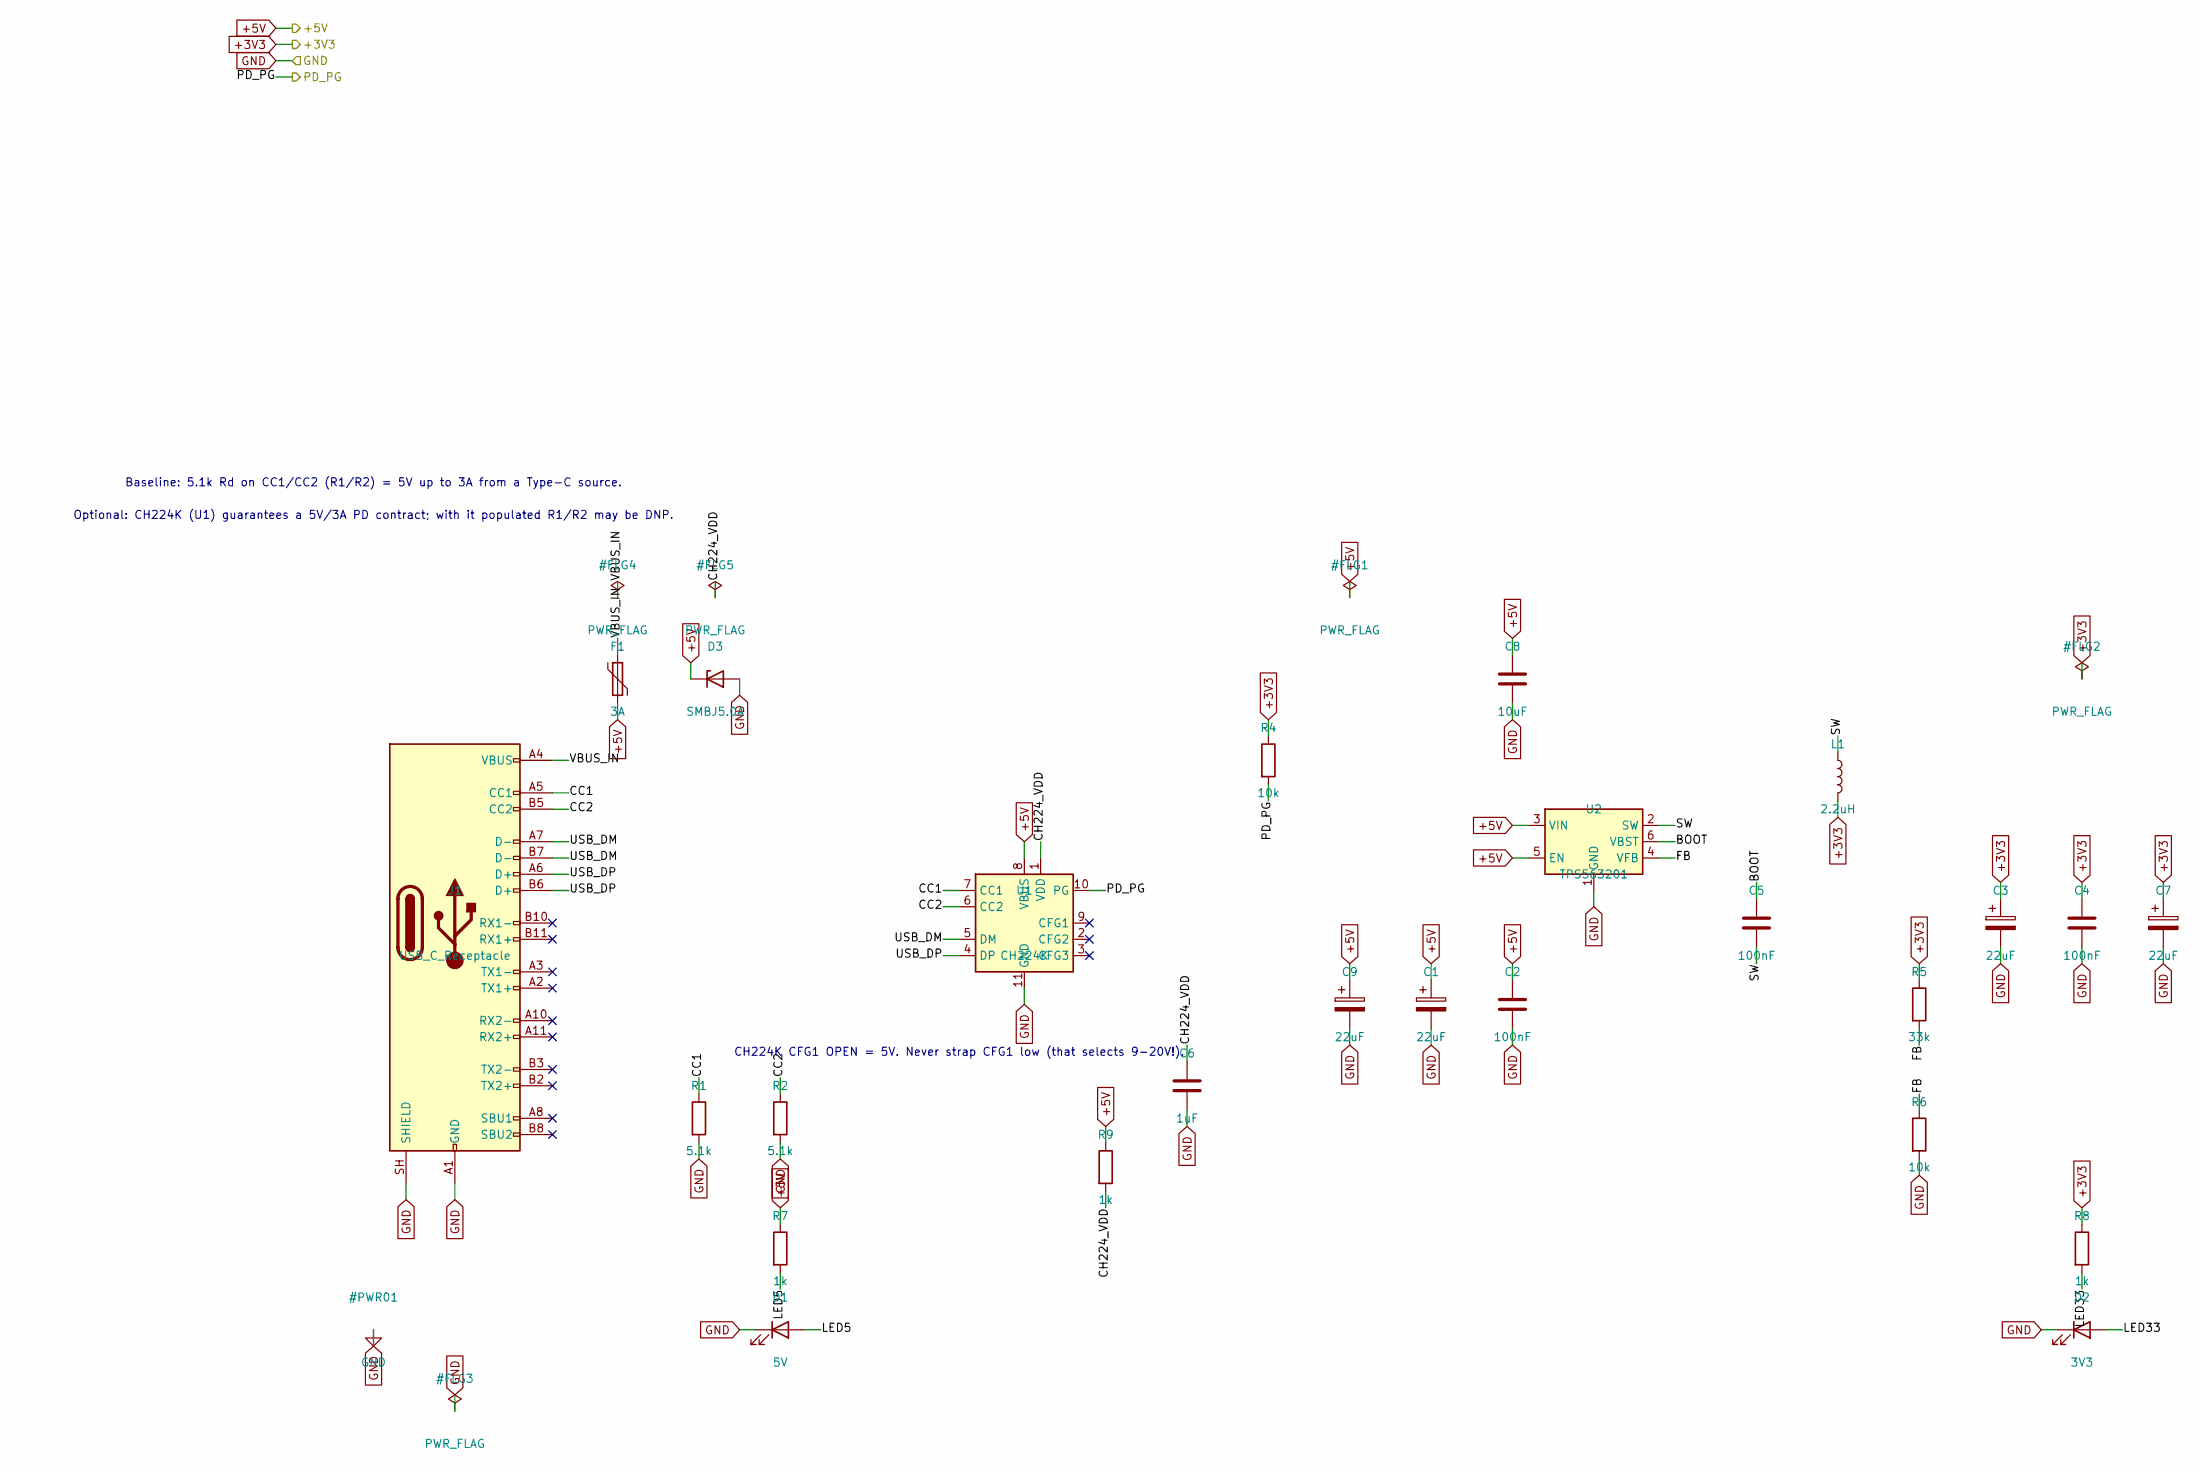
[picture p32: schematic power.kicad_sch]

Parts:
C1, C3, C7, C9: 22uF; C_1206_3216Metric; LCSC Part Num C12891
C2, C4, C5: 100nF; C_0603_1608Metric; LCSC Part Num C14663
C6: 1uF; C_0603_1608Metric; LCSC Part Num C15849
C8: 10uF; C_0805_2012Metric; LCSC Part Num C15850
D1: 5V; LED_0603_1608Metric; LCSC Part Num C2286
D2: 3V3; LED_0603_1608Metric; LCSC Part Num C2286
D3: SMBJ5.0A; D_SMB; LCSC Part Num C19077558
F1: 3A; Fuse_1812_4532Metric; LCSC Part Num C7500481
J1: USB_C_Receptacle; USB_C_Receptacle_HRO_TYPE-C-31-M-12; LCSC Part Num C2765186
L1: 2.2uH; L_Taiyo-Yuden_NR-40xx; LCSC Part Num C602029
R1, R2: 5.1k; R_0603_1608Metric; LCSC Part Num C23186
R4, R6: 10k; R_0805_2012Metric; LCSC Part Num C17414
R5: 33k; R_0603_1608Metric; LCSC Part Num C4216
R7, R8, R9: 1k; R_0603_1608Metric; LCSC Part Num C21190
U1: CH224K; ESSOP-10_150mil_P1.0mm; LCSC Part Num C970725
U2: TPS563201; TSOT-23-6; LCSC Part Num C116592

Connections:
+3V3: C3.1, C4.1, C7.1, L1.2, R4.1, R5.1, R8.1
+5V: C1.1, C2.1, C8.1, C9.1, D3.1 (K), F1.2, R7.1, R9.1, U1.8 (VBUS), U2.3 (VIN), U2.5 (EN)
BOOT: C5.1, U2.6 (VBST)
CC1: J1.A5 (CC1), R1.1, U1.7 (CC1)
CC2: J1.B5 (CC2), R2.1, U1.6 (CC2)
CH224_VDD: C6.1, R9.2, U1.1 (VDD)
FB: R5.2, R6.1, U2.4 (VFB)
GND: C1.2, C2.2, C3.2, C4.2, C6.2, C7.2, C8.2, C9.2, D1.1 (K), D2.1 (K), D3.2 (A), J1.A1 (GND), J1.A12 (GND), J1.B1 (GND), J1.B12 (GND), J1.SH (SHIELD), R1.2, R2.2, R6.2, U1.11 (GND), U2.1 (GND)
LED5: D1.2 (A), R7.2
LED33: D2.2 (A), R8.2
PD_PG: R4.2, U1.10 (PG)
SW: C5.2, L1.1, U2.2 (SW)
USB_DM: J1.A7 (D-), J1.B7 (D-), U1.5 (DM)
USB_DP: J1.A6 (D+), J1.B6 (D+), U1.4 (DP)
VBUS_IN: F1.1, J1.A4 (VBUS), J1.A9 (VBUS), J1.B4 (VBUS), J1.B9 (VBUS)

Notes on the sheet:
CH224K CFG1 OPEN = 5V. Never strap CFG1 low (that selects 9-20V!).
Baseline: 5.1k Rd on CC1/CC2 (R1/R2) = 5V up to 3A from a Type-C source.
Optional: CH224K (U1) guarantees a 5V/3A PD contract; with it populated R1/R2 may be DNP.
