vaelen/mini-xt/hardware/sheets/sidecar.kicad_sch

## KiCad design hardware/sheets/sidecar.kicad_sch (2026-07-23)

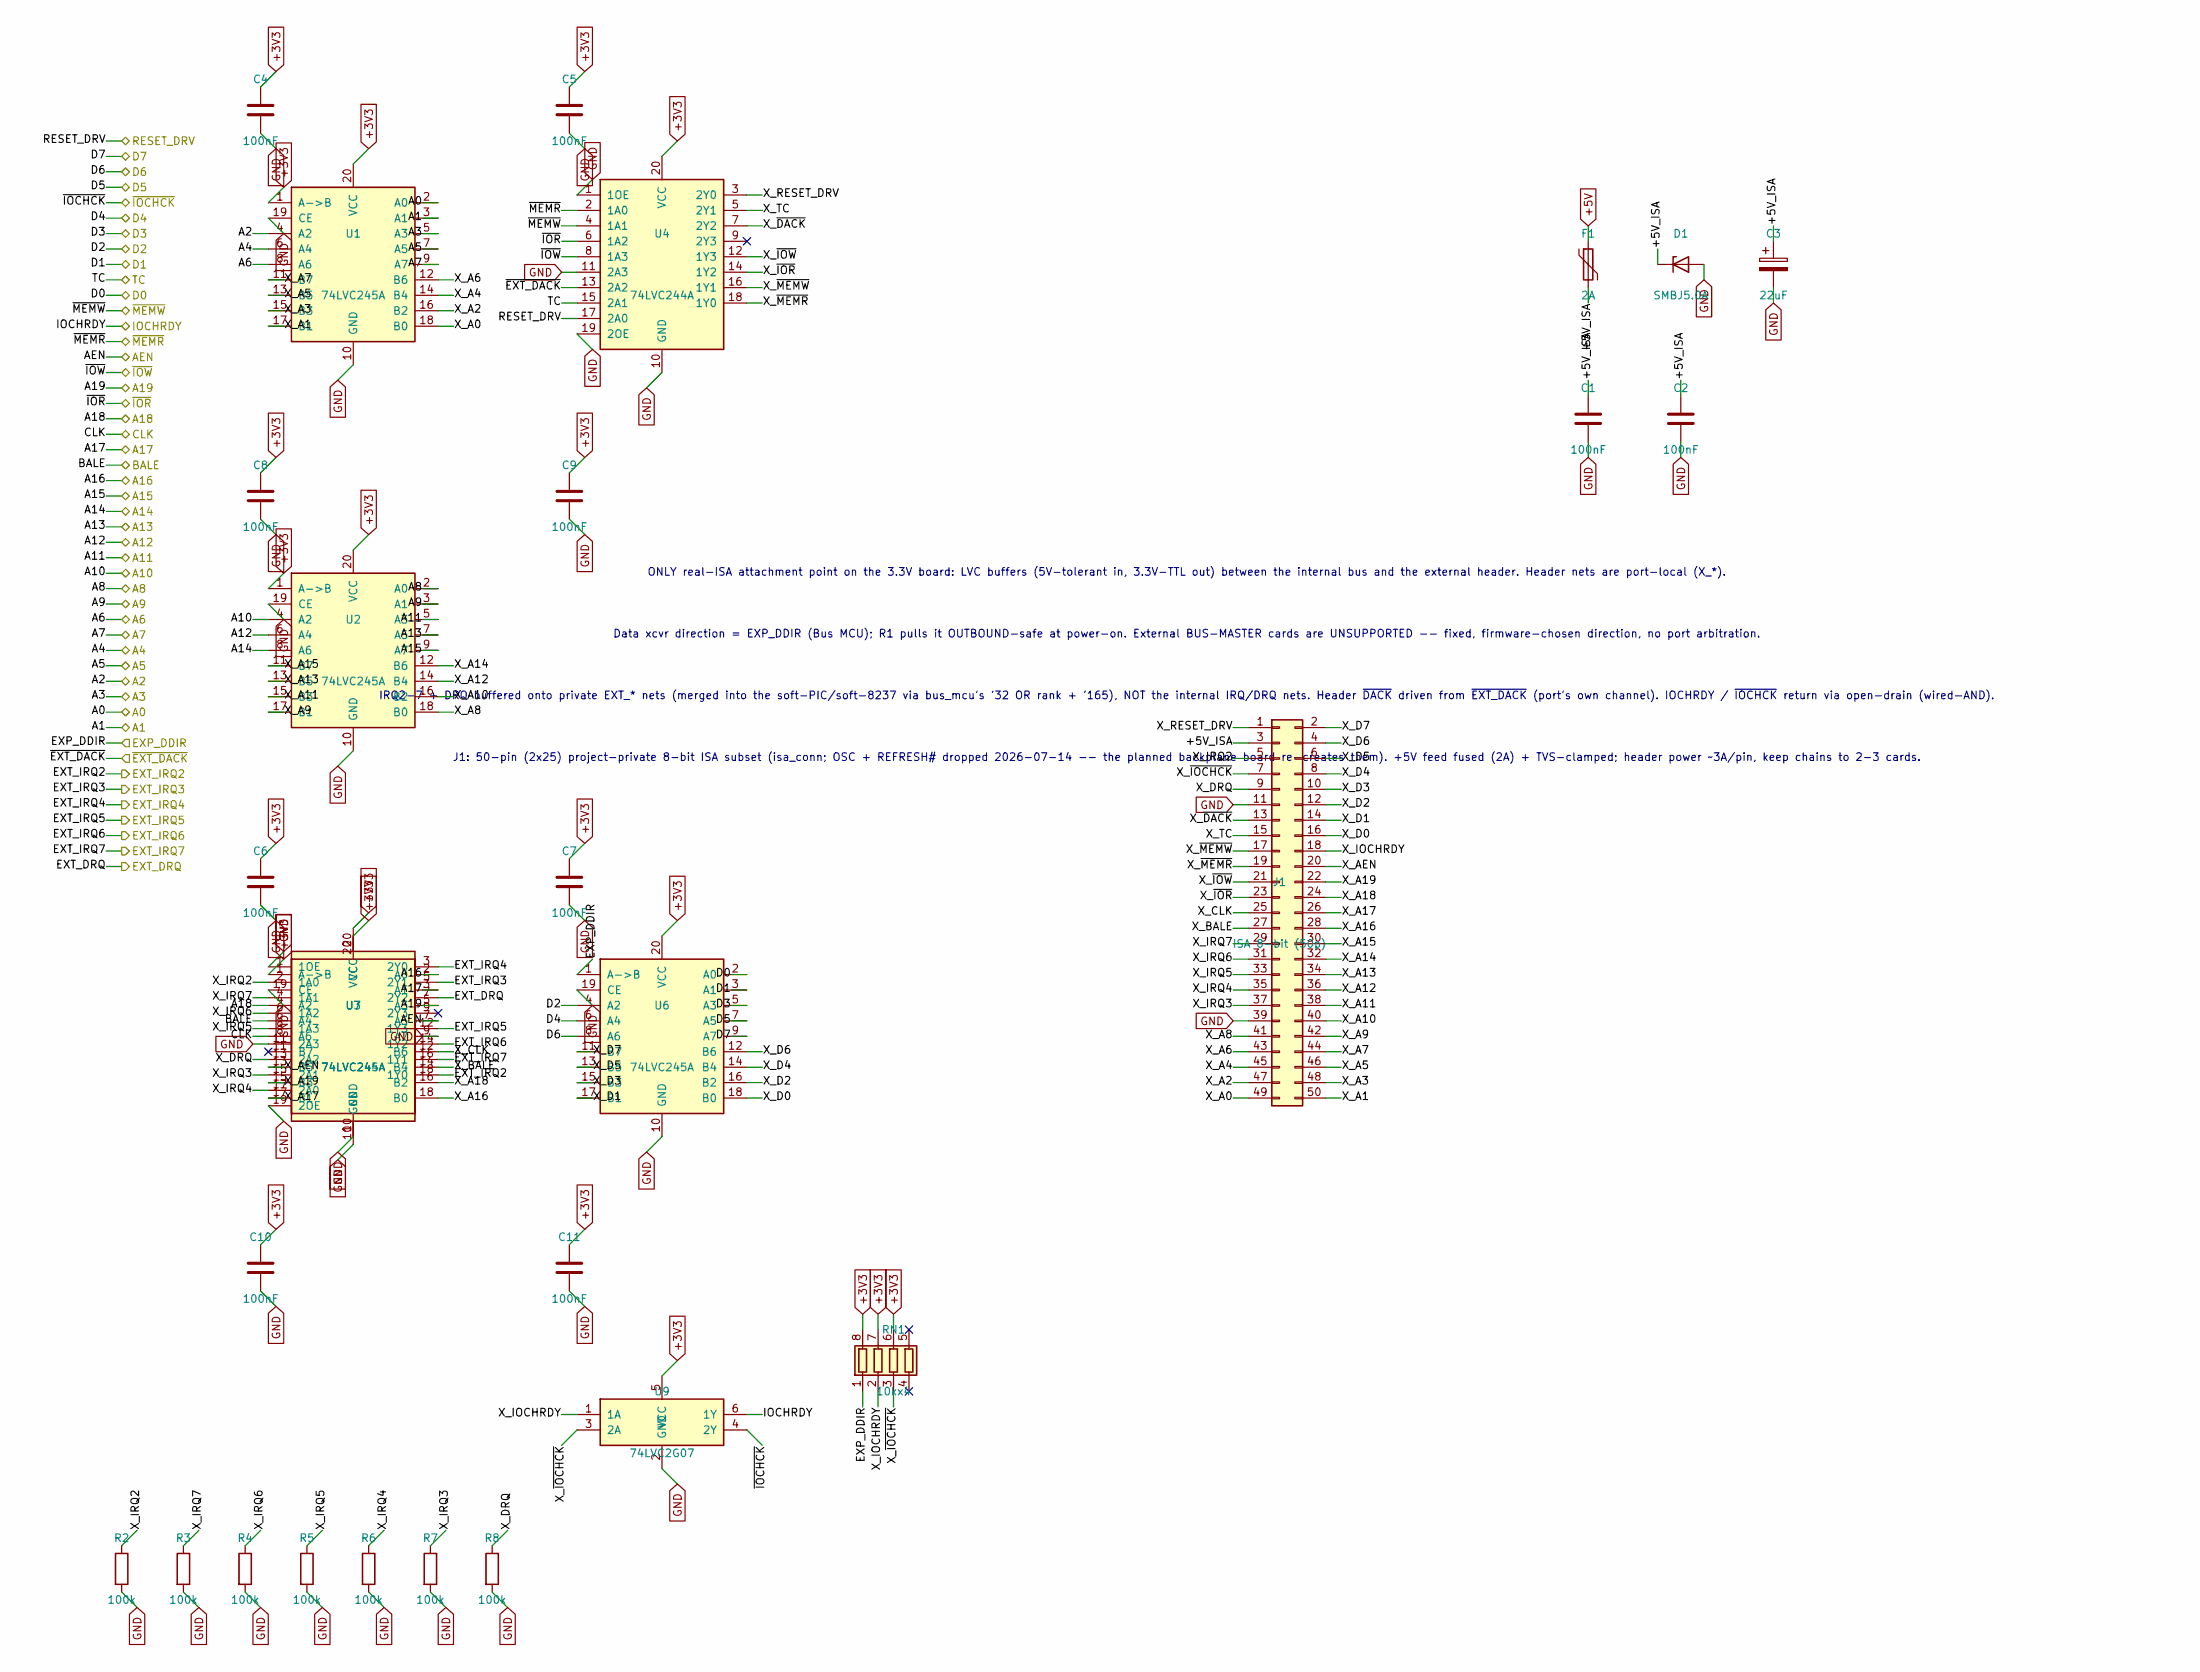
[picture p33: schematic sidecar.kicad_sch]

Parts:
C1, C2, C4, C5, C6, C7, C8, C9, C10, C11: 100nF; C_0603_1608Metric; LCSC Part Num C14663
C3: 22uF; C_1206_3216Metric; LCSC Part Num C12891
D1: SMBJ5.0A; D_SMB; LCSC Part Num C19077558
F1: 2A; Fuse_1812_4532Metric; LCSC Part Num C883156
J1: ISA 8-bit (50p); PinSocket_2x25_P2.54mm_Horizontal; LCSC Part Num C21262364
R2, R3, R4, R5, R6, R7, R8: 100k; R_0603_1608Metric; LCSC Part Num C25803
RN1: 10kx4; R_Array_Convex_4x0603; LCSC Part Num C29718
U1, U2, U3, U6: 74LVC245A; TSSOP-20_4.4x6.5mm_P0.65mm; LCSC Part Num C6082
U4, U7: 74LVC244A; TSSOP-20_4.4x6.5mm_P0.65mm; LCSC Part Num C6079
U9: 74LVC2G07; SOT-23-6; LCSC Part Num C24478

Connections:
+3V3: C4.1, C5.1, C6.1, C7.1, C8.1, C9.1, C10.1, C11.1, RN1.6 (R3.2), RN1.7 (R2.2), RN1.8 (R1.2), U1.1 (A->B), U1.20 (VCC), U2.1 (A->B), U2.20 (VCC), U3.1 (A->B), U3.20 (VCC), U4.20 (VCC), U6.20 (VCC), U7.20 (VCC), U9.5 (VCC)
+5V: F1.1
+5V_ISA: C1.1, C2.1, C3.1, D1.1 (K), F1.2, J1.3
A0: U1.2 (A0)
A1: U1.3 (A1)
A2: U1.4 (A2)
A3: U1.5 (A3)
A4: U1.6 (A4)
A5: U1.7 (A5)
A6: U1.8 (A6)
A7: U1.9 (A7)
A8: U2.2 (A0)
A9: U2.3 (A1)
A10: U2.4 (A2)
A11: U2.5 (A3)
A12: U2.6 (A4)
A13: U2.7 (A5)
A14: U2.8 (A6)
A15: U2.9 (A7)
A16: U3.2 (A0)
A17: U3.3 (A1)
A18: U3.4 (A2)
A19: U3.5 (A3)
AEN: U3.7 (A5)
BALE: U3.6 (A4)
CLK: U3.8 (A6)
D0: U6.2 (A0)
D1: U6.3 (A1)
D2: U6.4 (A2)
D3: U6.5 (A3)
D4: U6.6 (A4)
D5: U6.7 (A5)
D6: U6.8 (A6)
D7: U6.9 (A7)
EXP_DDIR: RN1.1 (R1.1), U6.1 (A->B)
EXT_DRQ: U7.7 (2Y2)
EXT_IRQ2: U7.18 (1Y0)
EXT_IRQ3: U7.5 (2Y1)
EXT_IRQ4: U7.3 (2Y0)
EXT_IRQ5: U7.12 (1Y3)
EXT_IRQ6: U7.14 (1Y2)
EXT_IRQ7: U7.16 (1Y1)
GND: C1.2, C2.2, C3.2, C4.2, C5.2, C6.2, C7.2, C8.2, C9.2, C10.2, C11.2, D1.2 (A), J1.11, J1.39, R2.2, R3.2, R4.2, R5.2, R6.2, R7.2, R8.2, U1.10 (GND), U1.19 (CE), U2.10 (GND), U2.19 (CE), U3.9 (A7), U3.10 (GND), U3.19 (CE), U4.1 (1OE), U4.10 (GND), U4.11 (2A3), U4.19 (2OE), U6.10 (GND), U6.19 (CE), U7.1 (1OE), U7.10 (GND), U7.11 (2A3), U7.19 (2OE), U9.2 (GND)
IOCHRDY: U9.6 (1Y)
RESET_DRV: U4.17 (2A0)
TC: U4.15 (2A1)
X_A0: J1.49, U1.18 (B0)
X_A1: J1.50, U1.17 (B1)
X_A2: J1.47, U1.16 (B2)
X_A3: J1.48, U1.15 (B3)
X_A4: J1.45, U1.14 (B4)
X_A5: J1.46, U1.13 (B5)
X_A6: J1.43, U1.12 (B6)
X_A7: J1.44, U1.11 (B7)
X_A8: J1.41, U2.18 (B0)
X_A9: J1.42, U2.17 (B1)
X_A10: J1.40, U2.16 (B2)
X_A11: J1.38, U2.15 (B3)
X_A12: J1.36, U2.14 (B4)
X_A13: J1.34, U2.13 (B5)
X_A14: J1.32, U2.12 (B6)
X_A15: J1.30, U2.11 (B7)
X_A16: J1.28, U3.18 (B0)
X_A17: J1.26, U3.17 (B1)
X_A18: J1.24, U3.16 (B2)
X_A19: J1.22, U3.15 (B3)
X_AEN: J1.20, U3.13 (B5)
X_BALE: J1.27, U3.14 (B4)
X_CLK: J1.25, U3.12 (B6)
X_D0: J1.16, U6.18 (B0)
X_D1: J1.14, U6.17 (B1)
X_D2: J1.12, U6.16 (B2)
X_D3: J1.10, U6.15 (B3)
X_D4: J1.8, U6.14 (B4)
X_D5: J1.6, U6.13 (B5)
X_D6: J1.4, U6.12 (B6)
X_D7: J1.2, U6.11 (B7)
X_DRQ: J1.9, R8.1, U7.13 (2A2)
X_IOCHRDY: J1.18, RN1.2 (R2.1), U9.1 (1A)
X_IRQ2: J1.5, R2.1, U7.2 (1A0)
X_IRQ3: J1.37, R7.1, U7.15 (2A1)
X_IRQ4: J1.35, R6.1, U7.17 (2A0)
X_IRQ5: J1.33, R5.1, U7.8 (1A3)
X_IRQ6: J1.31, R4.1, U7.6 (1A2)
X_IRQ7: J1.29, R3.1, U7.4 (1A1)
X_RESET_DRV: J1.1, U4.3 (2Y0)
X_TC: J1.15, U4.5 (2Y1)
X_~DACK: J1.13, U4.7 (2Y2)
X_~IOCHCK: J1.7, RN1.3 (R3.1), U9.3 (2A)
X_~IOR: J1.23, U4.14 (1Y2)
X_~IOW: J1.21, U4.12 (1Y3)
X_~MEMR: J1.19, U4.18 (1Y0)
X_~MEMW: J1.17, U4.16 (1Y1)
~EXT_DACK: U4.13 (2A2)
~IOCHCK: U9.4 (2Y)
~IOR: U4.6 (1A2)
~IOW: U4.8 (1A3)
~MEMR: U4.2 (1A0)
~MEMW: U4.4 (1A1)

Notes on the sheet:
ONLY real-ISA attachment point on the 3.3V board: LVC buffers (5V-tolerant in, 3.3V-TTL out) between the internal bus and the external header. Header nets are port-local (X_*).
Data xcvr direction = EXP_DDIR (Bus MCU); R1 pulls it OUTBOUND-safe at power-on. External BUS-MASTER cards are UNSUPPORTED -- fixed, firmware-chosen direction, no port arbitration.
IRQ2-7 + DRQ buffered onto private EXT_* nets (merged into the soft-PIC/soft-8237 via bus_mcu's '32 OR rank + '165), NOT the internal IRQ/DRQ nets. Header ~{DACK} driven from ~{EXT_DACK} (port's own channel). IOCHRDY / ~{IOCHCK} return via open-drain (wired-AND).
J1: 50-pin (2x25) project-private 8-bit ISA subset (isa_conn; OSC + REFRESH# dropped 2026-07-14 -- the planned backplane board re-creates them). +5V feed fused (2A) + TVS-clamped; header power ~3A/pin, keep chains to 2-3 cards.
