vaelen/mini-xt/hardware/sheets/storage.kicad_sch

## KiCad design hardware/sheets/storage.kicad_sch (2026-07-23)

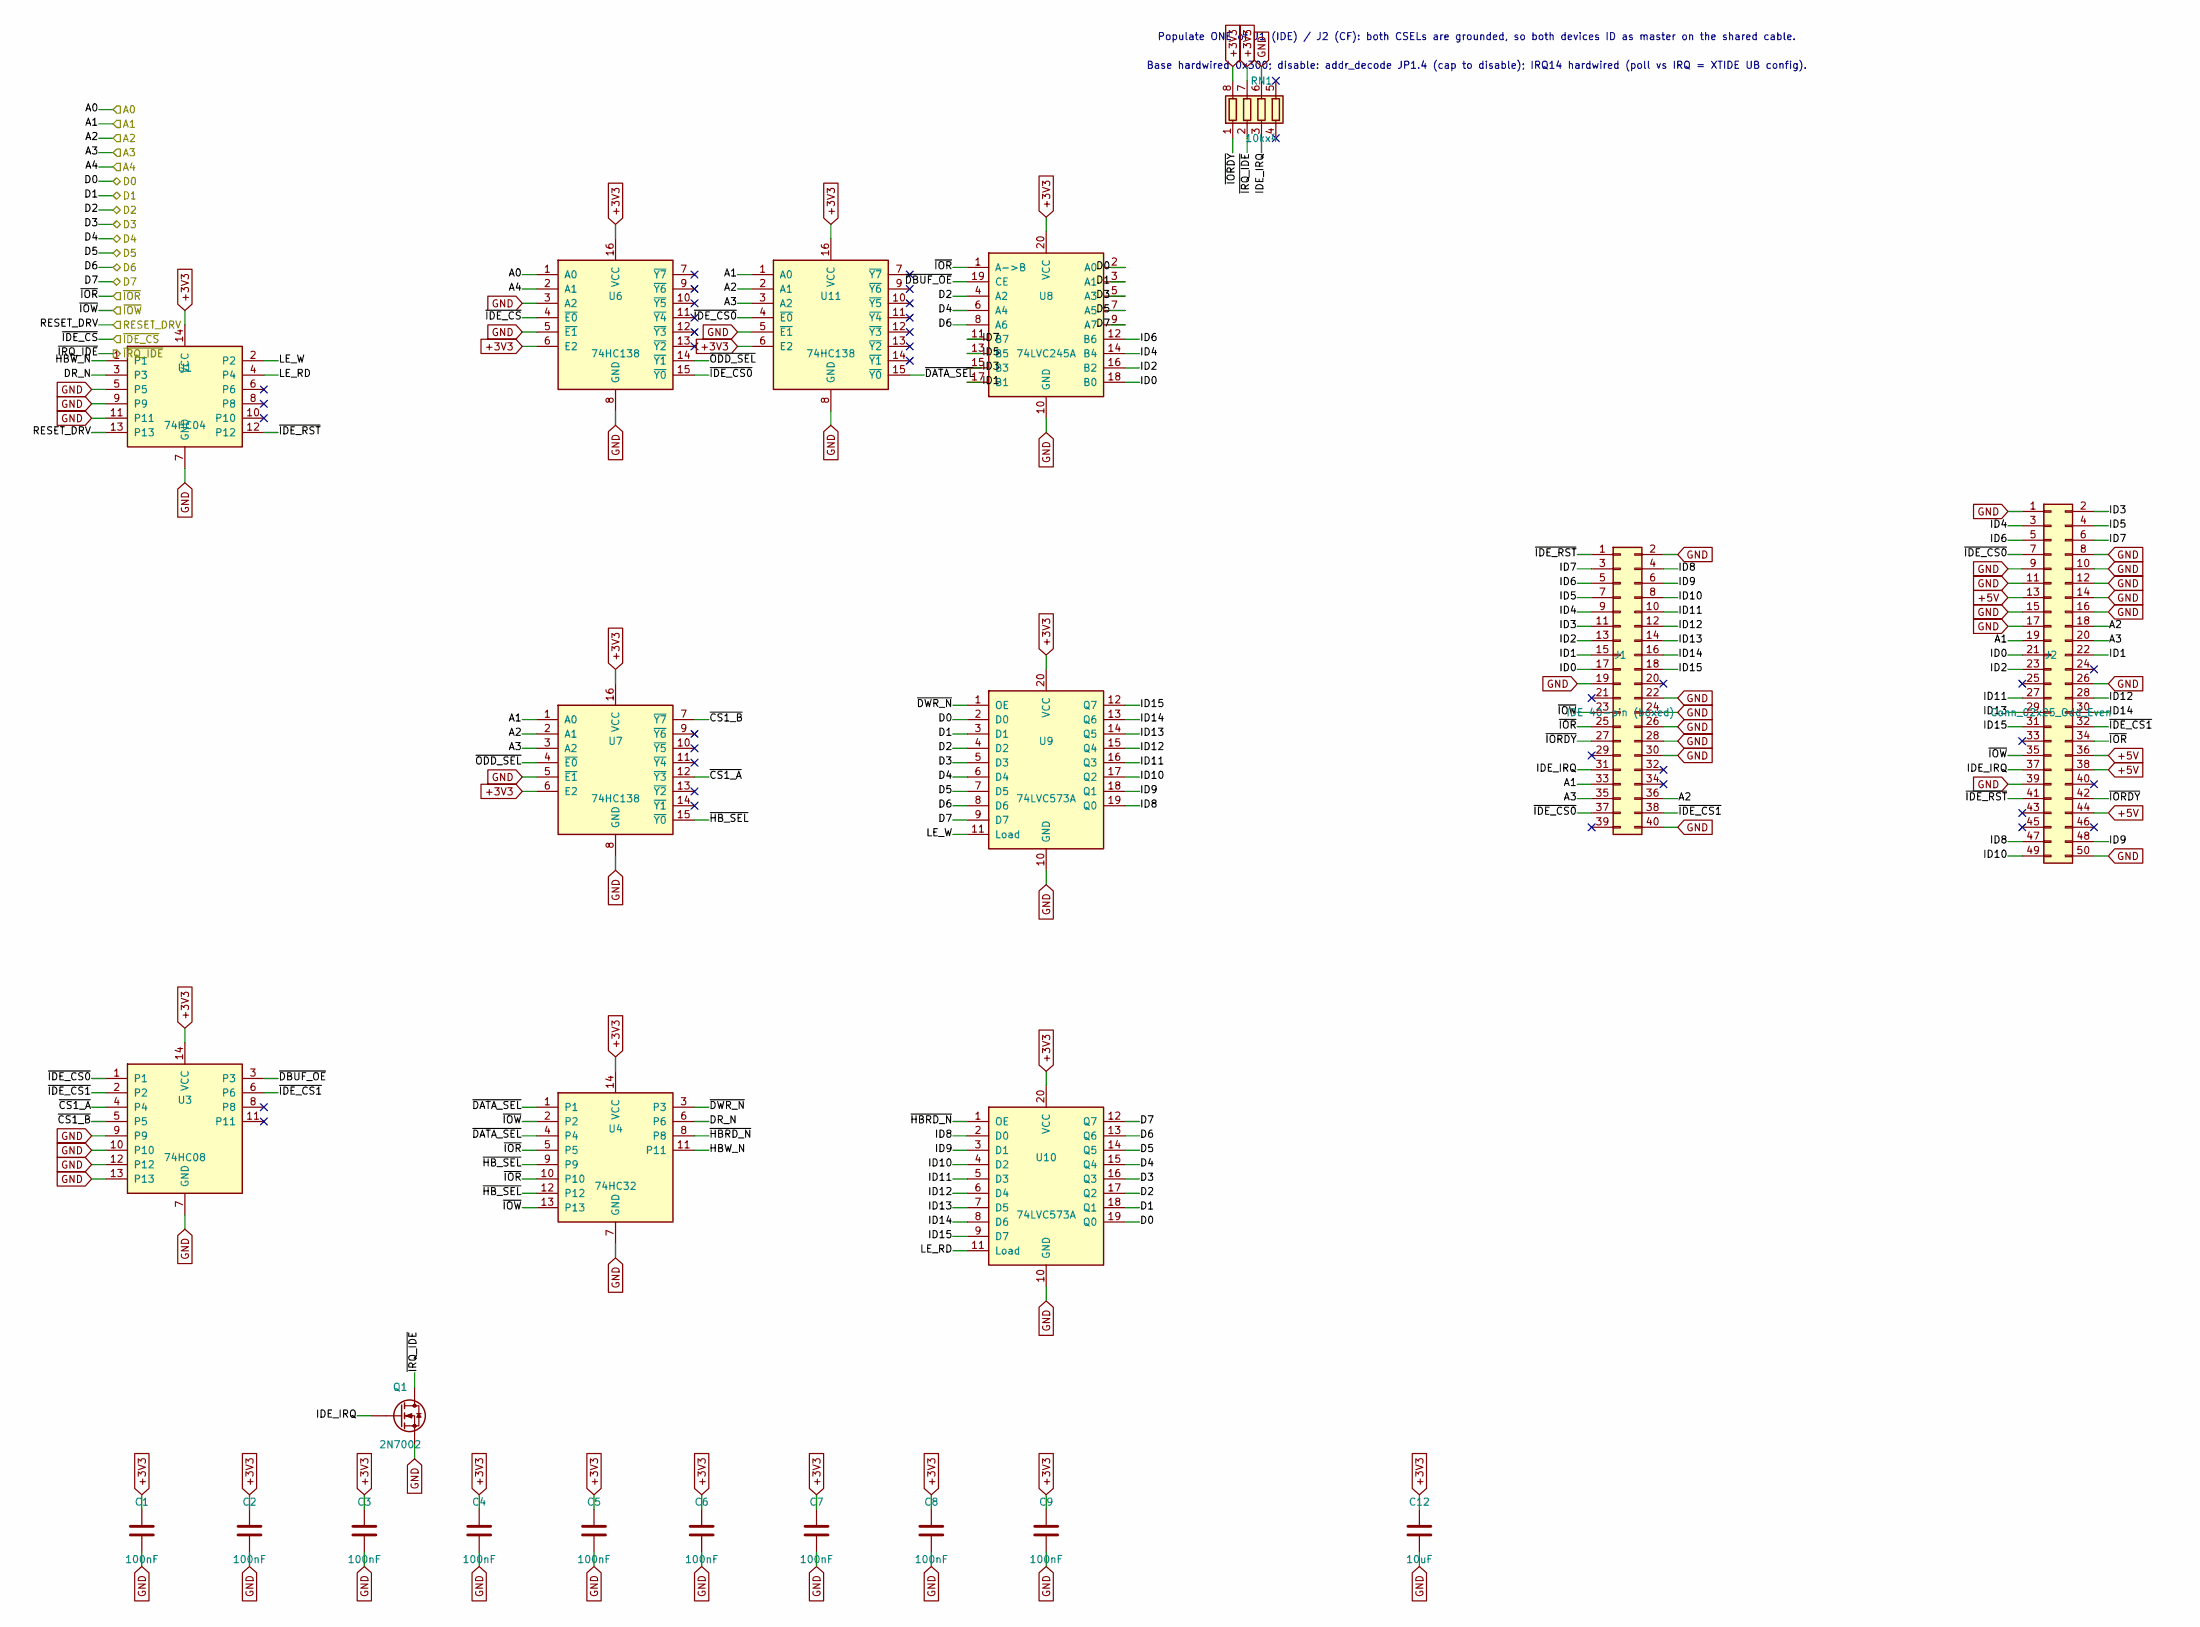
[picture p34: schematic storage.kicad_sch]

Parts:
C1, C2, C3, C4, C5, C6, C7, C8, C9: 100nF; C_0603_1608Metric; LCSC Part Num C14663
C12: 10uF; C_0805_2012Metric; LCSC Part Num C15850
J1: IDE 40-pin (boxed); IDC-Header_2x20_P2.54mm_Vertical; LCSC Part Num C9138
J2: Conn_02x25_Odd_Even; CF_HYCW01-CF50-395B; LCSC Part Num C2962036
Q1: 2N7002; SOT-23; LCSC Part Num C8545
RN1: 10kx4; R_Array_Convex_4x0603; LCSC Part Num C29718
U1: 74HC04; SOIC-14_3.9x8.7mm_P1.27mm; LCSC Part Num C86613
U3: 74HC08; SOIC-14_3.9x8.7mm_P1.27mm; LCSC Part Num C5593
U4: 74HC32; SOIC-14_3.9x8.7mm_P1.27mm; LCSC Part Num C52140395
U6, U7, U11: 74HC138; SOIC-16_3.9x9.9mm_P1.27mm; LCSC Part Num C5602
U8: 74LVC245A; TSSOP-20_4.4x6.5mm_P0.65mm; LCSC Part Num C6082
U9, U10: 74LVC573A; TSSOP-20_4.4x6.5mm_P0.65mm; LCSC Part Num C6096

Connections:
+3V3: C1.1, C2.1, C3.1, C4.1, C5.1, C6.1, C7.1, C8.1, C9.1, C12.1, RN1.7 (R2.2), RN1.8 (R1.2), U1.14 (VCC), U3.14 (VCC), U4.14 (VCC), U6.6 (E2), U6.16 (VCC), U7.6 (E2), U7.16 (VCC), U8.20 (VCC), U9.20 (VCC), U10.20 (VCC), U11.6 (E2), U11.16 (VCC)
+5V: J2.13, J2.36, J2.38, J2.44
A0: U6.1 (A0)
A1: J1.33, J2.19, U7.1 (A0), U11.1 (A0)
A2: J1.36, J2.18, U7.2 (A1), U11.2 (A1)
A3: J1.35, J2.20, U7.3 (A2), U11.3 (A2)
A4: U6.2 (A1)
D0: U8.2 (A0), U9.2 (D0), U10.19 (Q0)
D1: U8.3 (A1), U9.3 (D1), U10.18 (Q1)
D2: U8.4 (A2), U9.4 (D2), U10.17 (Q2)
D3: U8.5 (A3), U9.5 (D3), U10.16 (Q3)
D4: U8.6 (A4), U9.6 (D4), U10.15 (Q4)
D5: U8.7 (A5), U9.7 (D5), U10.14 (Q5)
D6: U8.8 (A6), U9.8 (D6), U10.13 (Q6)
D7: U8.9 (A7), U9.9 (D7), U10.12 (Q7)
DR_N: U1.3, U4.6
GND: C1.2, C2.2, C3.2, C4.2, C5.2, C6.2, C7.2, C8.2, C9.2, C12.2, J1.2, J1.19, J1.22, J1.24, J1.26, J1.28, J1.30, J1.40, J2.1, J2.8, J2.9, J2.10, J2.11, J2.12, J2.14, J2.15, J2.16, J2.17, J2.26, J2.39, J2.50, Q1.S, RN1.6 (R3.2), U1.5, U1.7 (GND), U1.9, U1.11, U3.7 (GND), U3.9, U3.10, U3.12, U3.13, U4.7 (GND), U6.3 (A2), U6.5 (~E1), U6.8 (GND), U7.5 (~E1), U7.8 (GND), U8.10 (GND), U9.10 (GND), U10.10 (GND), U11.5 (~E1), U11.8 (GND)
HBW_N: U1.1, U4.11
ID0: J1.17, J2.21, U8.18 (B0)
ID1: J1.15, J2.22, U8.17 (B1)
ID2: J1.13, J2.23, U8.16 (B2)
ID3: J1.11, J2.2, U8.15 (B3)
ID4: J1.9, J2.3, U8.14 (B4)
ID5: J1.7, J2.4, U8.13 (B5)
ID6: J1.5, J2.5, U8.12 (B6)
ID7: J1.3, J2.6, U8.11 (B7)
ID8: J1.4, J2.47, U9.19 (Q0), U10.2 (D0)
ID9: J1.6, J2.48, U9.18 (Q1), U10.3 (D1)
ID10: J1.8, J2.49, U9.17 (Q2), U10.4 (D2)
ID11: J1.10, J2.27, U9.16 (Q3), U10.5 (D3)
ID12: J1.12, J2.28, U9.15 (Q4), U10.6 (D4)
ID13: J1.14, J2.29, U9.14 (Q5), U10.7 (D5)
ID14: J1.16, J2.30, U9.13 (Q6), U10.8 (D6)
ID15: J1.18, J2.31, U9.12 (Q7), U10.9 (D7)
IDE_IRQ: J1.31, J2.37, Q1.G, RN1.3 (R3.1)
LE_RD: U1.4, U10.11 (Load)
LE_W: U1.2, U9.11 (Load)
RESET_DRV: U1.13
~CS1_A: U3.4, U7.12 (~Y3)
~CS1_B: U3.5, U7.7 (~Y7)
~DATA_SEL: U4.1, U4.4, U11.15 (~Y0)
~DBUF_OE: U3.3, U8.19 (CE)
~DWR_N: U4.3, U9.1 (OE)
~HBRD_N: U4.8, U10.1 (OE)
~HB_SEL: U4.9, U4.12, U7.15 (~Y0)
~IDE_CS0: J1.37, J2.7, U3.1, U6.15 (~Y0), U11.4 (~E0)
~IDE_CS1: J1.38, J2.32, U3.2, U3.6
~IDE_CS: U6.4 (~E0)
~IDE_RST: J1.1, J2.41, U1.12
~IORDY: J1.27, J2.42, RN1.1 (R1.1)
~IOR: J1.25, J2.34, U4.5, U4.10, U8.1 (A->B)
~IOW: J1.23, J2.35, U4.2, U4.13
~IRQ_IDE: Q1.D, RN1.2 (R2.1)
~ODD_SEL: U6.14 (~Y1), U7.4 (~E0)

Notes on the sheet:
Base hardwired 0x300; disable: addr_decode JP1.4 (cap to disable); IRQ14 hardwired (poll vs IRQ = XTIDE UB config).
Populate ONE of J1 (IDE) / J2 (CF): both CSELs are grounded, so both devices ID as master on the shared cable.
