vaelen/mini-xt/hardware/sheets/supervisor.kicad_sch

## KiCad design hardware/sheets/supervisor.kicad_sch (2026-07-23)

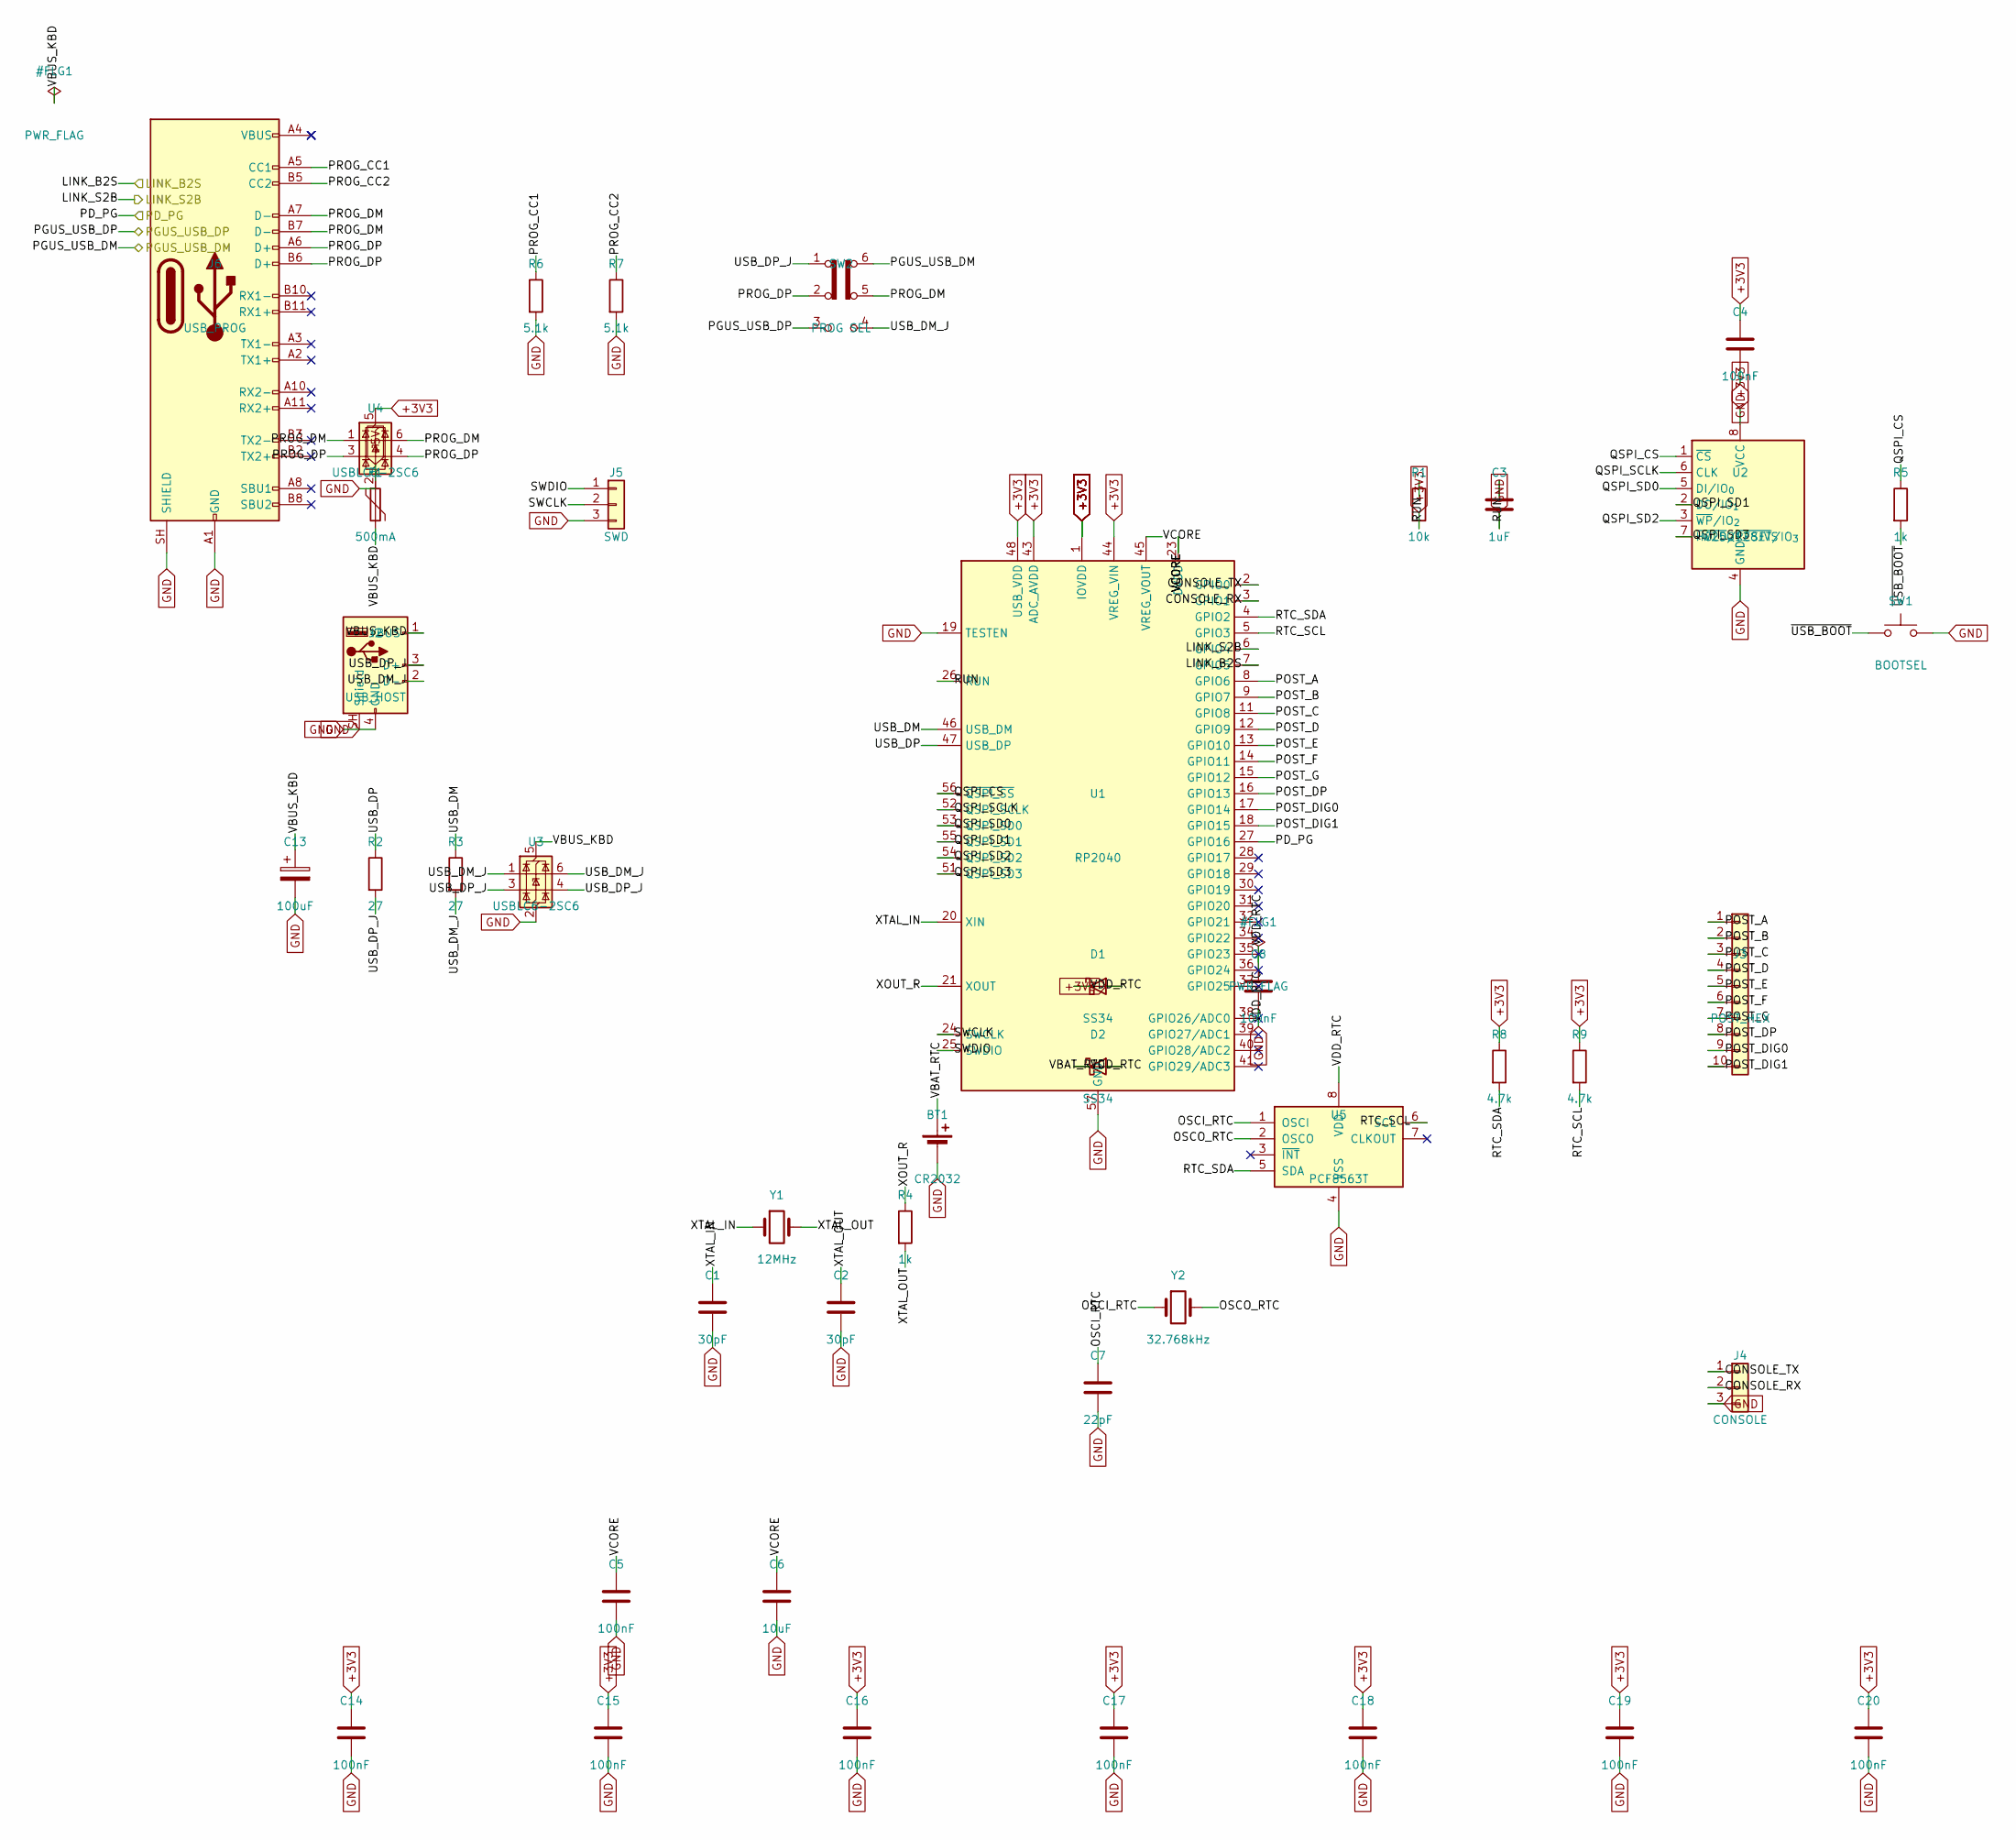
[picture p35: schematic supervisor.kicad_sch]

Parts:
BT1: CR2032; BatteryHolder_Keystone_1058_1x2032; LCSC Part Num C22363833
C1, C2: 30pF; C_0603_1608Metric; LCSC Part Num C1658
C3: 1uF; C_0603_1608Metric; LCSC Part Num C15849
C4, C5, C8, C14, C15, C16, C17, C18, C19, C20: 100nF; C_0603_1608Metric; LCSC Part Num C14663
C6: 10uF; C_0805_2012Metric; LCSC Part Num C15850
C7: 22pF; C_0603_1608Metric; LCSC Part Num C1653
C13: 100uF; CP_Elec_6.3x5.4; LCSC Part Num C2887276
D1, D2: SS34; D_SMA; LCSC Part Num C8678
F1: 500mA; Fuse_1206_3216Metric; LCSC Part Num C46641014
J2: USB_HOST; USB_A_Stewart_SS-52100-001_Horizontal; LCSC Part Num C456015
J3: POST_HEX; PinHeader_1x10_P2.54mm_Vertical; LCSC Part Num C2337
J4: CONSOLE; PinHeader_1x03_P2.54mm_Vertical; LCSC Part Num C2337
J5: SWD; PinHeader_1x03_P2.54mm_Vertical; LCSC Part Num C2337
J6: USB_PROG; USB_C_Receptacle_HRO_TYPE-C-31-M-12; LCSC Part Num C2765186
R1: 10k; R_0805_2012Metric; LCSC Part Num C17414
R2, R3: 27; R_0603_1608Metric; LCSC Part Num C25190
R4, R5: 1k; R_0603_1608Metric; LCSC Part Num C21190
R6, R7: 5.1k; R_0603_1608Metric; LCSC Part Num C23186
R8, R9: 4.7k; R_0603_1608Metric; LCSC Part Num C23162
SW1: BOOTSEL; SW_TS-1187A_5.1x5.1mm; LCSC Part Num C318884
SW2: PROG SEL; SW_MST22D18G2_9.1x3.6mm; LCSC Part Num C431544
U1: RP2040; QFN-56-1EP_7x7mm_P0.4mm_EP3.2x3.2mm; LCSC Part Num C2040
U2: W25Q128JVS; SOIC-8_5.3x5.3mm_P1.27mm; LCSC Part Num C97521
U3, U4: USBLC6-2SC6; SOT-23-6; LCSC Part Num C2687116
U5: PCF8563T; SOIC-8_3.9x4.9mm_P1.27mm; LCSC Part Num C7440
Y1: 12MHz; Crystal_SMD_3225-4Pin_3.2x2.5mm; LCSC Part Num C9002
Y2: 32.768kHz; Crystal_SMD_3215-2Pin_3.2x1.5mm; LCSC Part Num C32346

Connections:
+3V3: C4.1, C14.1, C15.1, C16.1, C17.1, C18.1, C19.1, C20.1, D1.2 (A), R1.2, R8.1, R9.1, U1.1 (IOVDD), U1.10 (IOVDD), U1.22 (IOVDD), U1.33 (IOVDD), U1.42 (IOVDD), U1.43 (ADC_AVDD), U1.44 (VREG_VIN), U1.48 (USB_VDD), U1.49 (IOVDD), U2.8 (VCC), U4.5 (VBUS)
+5V: F1.1
CONSOLE_RX: J4.2, U1.3 (GPIO1)
CONSOLE_TX: J4.1, U1.2 (GPIO0)
GND: BT1.2 (-), C1.2, C2.2, C3.2, C4.2, C5.2, C6.2, C7.2, C8.2, C13.2, C14.2, C15.2, C16.2, C17.2, C18.2, C19.2, C20.2, J2.4 (GND), J2.SH (Shield), J4.3, J5.3, J6.A1 (GND), J6.A12 (GND), J6.B1 (GND), J6.B12 (GND), J6.SH (SHIELD), R6.2, R7.2, SW1.2, U1.19 (TESTEN), U1.57 (GND), U2.4 (GND), U3.2 (GND), U4.2 (GND), U5.4 (VSS)
LINK_B2S: U1.7 (GPIO5)
LINK_S2B: U1.6 (GPIO4)
unnamed: J6.A4 (VBUS), J6.A9 (VBUS), J6.B4 (VBUS), J6.B9 (VBUS)
OSCI_RTC: C7.1, U5.1 (OSCI), Y2.1
OSCO_RTC: U5.2 (OSCO), Y2.2
PD_PG: U1.27 (GPIO16)
PGUS_USB_DM: SW2.6 (C)
PGUS_USB_DP: SW2.3 (C)
POST_A: J3.1, U1.8 (GPIO6)
POST_B: J3.2, U1.9 (GPIO7)
POST_C: J3.3, U1.11 (GPIO8)
POST_D: J3.4, U1.12 (GPIO9)
POST_DIG0: J3.9, U1.17 (GPIO14)
POST_DIG1: J3.10, U1.18 (GPIO15)
POST_DP: J3.8, U1.16 (GPIO13)
POST_E: J3.5, U1.13 (GPIO10)
POST_F: J3.6, U1.14 (GPIO11)
POST_G: J3.7, U1.15 (GPIO12)
PROG_CC1: J6.A5 (CC1), R6.1
PROG_CC2: J6.B5 (CC2), R7.1
PROG_DM: J6.A7 (D-), J6.B7 (D-), SW2.5 (B), U4.1 (I/O1), U4.6 (I/O1)
PROG_DP: J6.A6 (D+), J6.B6 (D+), SW2.2 (B), U4.3 (I/O2), U4.4 (I/O2)
QSPI_CS: R5.1, U1.56 (~QSPI_SS), U2.1 (~CS)
QSPI_SCLK: U1.52 (QSPI_SCLK), U2.6 (CLK)
QSPI_SD0: U1.53 (QSPI_SD0), U2.5 (DI/IO_{0})
QSPI_SD1: U1.55 (QSPI_SD1), U2.2 (DO/IO_{1})
QSPI_SD2: U1.54 (QSPI_SD2), U2.3 (~WP/IO_{2})
QSPI_SD3: U1.51 (QSPI_SD3), U2.7 (~HOLD/~RESET/IO_{3})
RTC_SCL: R9.2, U1.5 (GPIO3), U5.6 (SCL)
RTC_SDA: R8.2, U1.4 (GPIO2), U5.5 (SDA)
RUN: C3.1, R1.1, U1.26 (RUN)
SWCLK: J5.2, U1.24 (SWCLK)
SWDIO: J5.1, U1.25 (SWDIO)
USB_DM: R3.1, U1.46 (USB_DM)
USB_DM_J: J2.2 (D-), R3.2, SW2.4 (A), U3.1 (I/O1), U3.6 (I/O1)
USB_DP: R2.1, U1.47 (USB_DP)
USB_DP_J: J2.3 (D+), R2.2, SW2.1 (A), U3.3 (I/O2), U3.4 (I/O2)
VBAT_RTC: BT1.1 (+), D2.2 (A)
VBUS_KBD: C13.1, F1.2, J2.1 (VBUS), U3.5 (VBUS)
VCORE: C5.1, C6.1, U1.23 (DVDD), U1.45 (VREG_VOUT), U1.50 (DVDD)
VDD_RTC: C8.1, D1.1 (K), D2.1 (K), U1.35 (GPIO23), U1.36 (GPIO24), U5.8 (VDD)
XOUT_R: R4.1, U1.21 (XOUT)
XTAL_IN: C1.1, U1.20 (XIN), Y1.1
XTAL_OUT: C2.1, R4.2, Y1.2
~USB_BOOT: R5.2, SW1.1
