vaelen/mini-xt/hardware/sheets/video.kicad_sch

## KiCad design hardware/sheets/video.kicad_sch (2026-07-23)

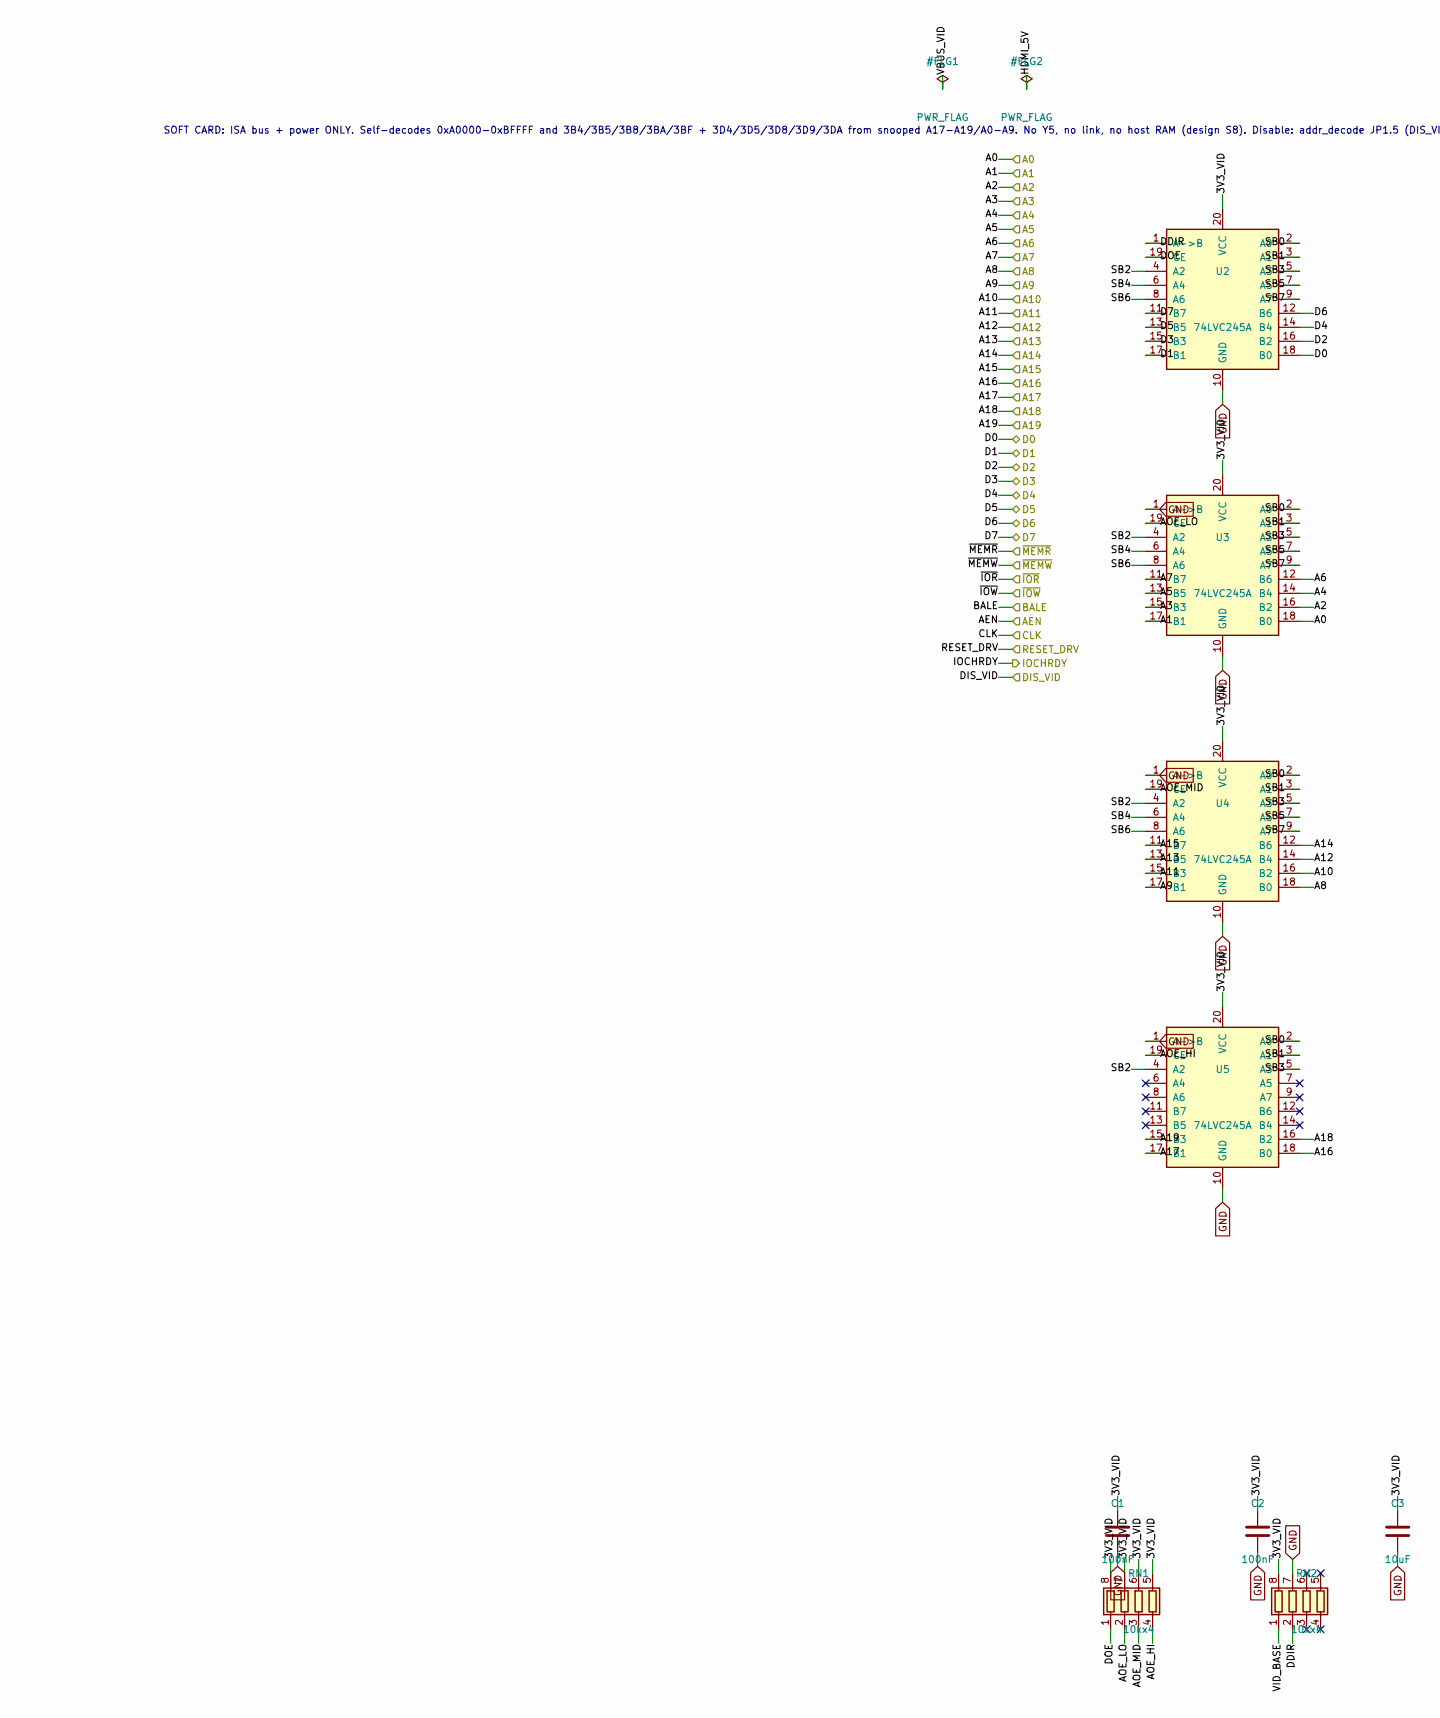
[picture p36: schematic video.kicad_sch, part in row 1, column 1]

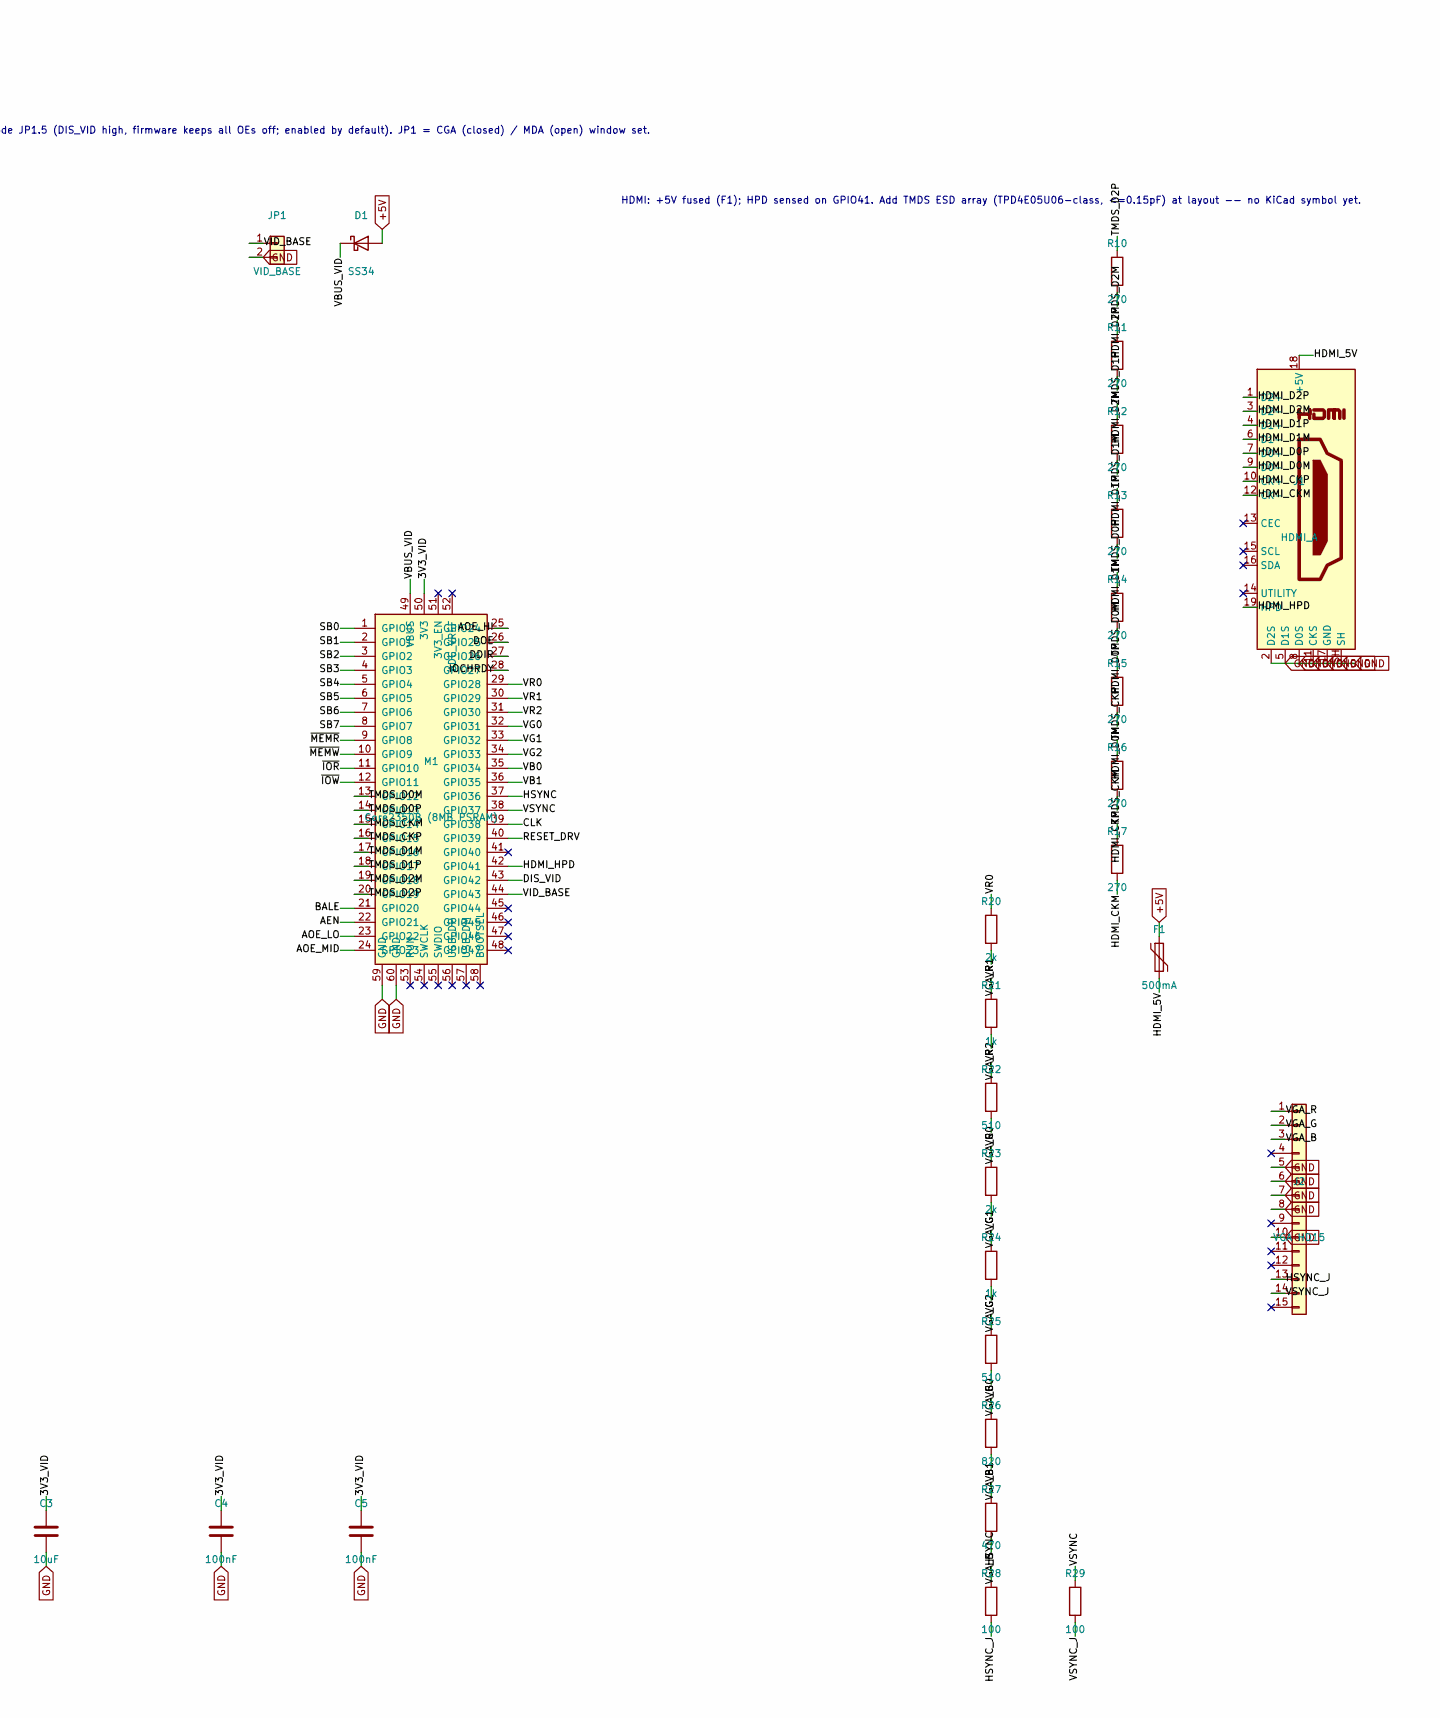
[picture p37: schematic video.kicad_sch, part in row 1, column 2]

Parts:
C1, C2, C4, C5: 100nF; C_0603_1608Metric; LCSC Part Num C14663
C3: 10uF; C_0805_2012Metric; LCSC Part Num C15850
D1: SS34; D_SMA; LCSC Part Num C8678
F1: 500mA; Fuse_1206_3216Metric; LCSC Part Num C46641014
J1: HDMI_A; HDMI_A_SHOUHAN_043; LCSC Part Num C2858275
J2: VGA HD15; DSUB-15-HD_Socket_Horizontal_P2.29x2.54mm_EdgePinOffset8.35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
JP1: VID_BASE; PinHeader_1x02_P2.54mm_Vertical; LCSC Part Num C492401
M1: Core2350B (8MB PSRAM); Core2350B_PGA; LCSC Part Num C2897411
R10, R11, R12, R13, R14, R15, R16, R17: 270; R_0603_1608Metric; LCSC Part Num C22966
R20, R23: 2k; R_0603_1608Metric; LCSC Part Num C22975
R21, R24: 1k; R_0603_1608Metric; LCSC Part Num C21190
R22, R25: 510; R_0603_1608Metric; LCSC Part Num C23193
R26: 820; R_0603_1608Metric; LCSC Part Num C23253
R27: 470; R_0603_1608Metric; LCSC Part Num C23179
R28, R29: 100; R_0603_1608Metric; LCSC Part Num C22775
RN1, RN2: 10kx4; R_Array_Convex_4x0603; LCSC Part Num C29718
U2, U3, U4, U5: 74LVC245A; TSSOP-20_4.4x6.5mm_P0.65mm; LCSC Part Num C6082

Connections:
3V3_VID: C1.1, C2.1, C3.1, C4.1, C5.1, M1.50 (3V3), RN1.5 (R4.2), RN1.6 (R3.2), RN1.7 (R2.2), RN1.8 (R1.2), RN2.8 (R1.2), U2.20 (VCC), U3.20 (VCC), U4.20 (VCC), U5.20 (VCC)
+5V: D1.2 (A), F1.1
A0: U3.18 (B0)
A1: U3.17 (B1)
A2: U3.16 (B2)
A3: U3.15 (B3)
A4: U3.14 (B4)
A5: U3.13 (B5)
A6: U3.12 (B6)
A7: U3.11 (B7)
A8: U4.18 (B0)
A9: U4.17 (B1)
A10: U4.16 (B2)
A11: U4.15 (B3)
A12: U4.14 (B4)
A13: U4.13 (B5)
A14: U4.12 (B6)
A15: U4.11 (B7)
A16: U5.18 (B0)
A17: U5.17 (B1)
A18: U5.16 (B2)
A19: U5.15 (B3)
AEN: M1.22 (GPIO21)
AOE_HI: M1.25 (GPIO24), RN1.4 (R4.1), U5.19 (CE)
AOE_LO: M1.23 (GPIO22), RN1.2 (R2.1), U3.19 (CE)
AOE_MID: M1.24 (GPIO23), RN1.3 (R3.1), U4.19 (CE)
BALE: M1.21 (GPIO20)
CLK: M1.39 (GPIO38)
D0: U2.18 (B0)
D1: U2.17 (B1)
D2: U2.16 (B2)
D3: U2.15 (B3)
D4: U2.14 (B4)
D5: U2.13 (B5)
D6: U2.12 (B6)
D7: U2.11 (B7)
DDIR: M1.27 (GPIO26), RN2.2 (R2.1), U2.1 (A->B)
DIS_VID: M1.43 (GPIO42)
DOE: M1.26 (GPIO25), RN1.1 (R1.1), U2.19 (CE)
GND: C1.2, C2.2, C3.2, C4.2, C5.2, J1.2 (D2S), J1.5 (D1S), J1.8 (D0S), J1.11 (CKS), J1.17 (GND), J1.SH, J2.5, J2.6, J2.7, J2.8, J2.10, JP1.2, M1.59 (GND), M1.60 (GND), RN2.7 (R2.2), U2.10 (GND), U3.1 (A->B), U3.10 (GND), U4.1 (A->B), U4.10 (GND), U5.1 (A->B), U5.10 (GND)
HDMI_5V: F1.2, J1.18 (+5V)
HDMI_CKM: J1.12 (CK-), R17.2
HDMI_CKP: J1.10 (CK+), R16.2
HDMI_D0M: J1.9 (D0-), R15.2
HDMI_D0P: J1.7 (D0+), R14.2
HDMI_D1M: J1.6 (D1-), R13.2
HDMI_D1P: J1.4 (D1+), R12.2
HDMI_D2M: J1.3 (D2-), R11.2
HDMI_D2P: J1.1 (D2+), R10.2
HDMI_HPD: J1.19 (HPD), M1.42 (GPIO41)
HSYNC: M1.37 (GPIO36), R28.1
HSYNC_J: J2.13, R28.2
IOCHRDY: M1.28 (GPIO27)
RESET_DRV: M1.40 (GPIO39)
SB0: M1.1 (GPIO0), U2.2 (A0), U3.2 (A0), U4.2 (A0), U5.2 (A0)
SB1: M1.2 (GPIO1), U2.3 (A1), U3.3 (A1), U4.3 (A1), U5.3 (A1)
SB2: M1.3 (GPIO2), U2.4 (A2), U3.4 (A2), U4.4 (A2), U5.4 (A2)
SB3: M1.4 (GPIO3), U2.5 (A3), U3.5 (A3), U4.5 (A3), U5.5 (A3)
SB4: M1.5 (GPIO4), U2.6 (A4), U3.6 (A4), U4.6 (A4)
SB5: M1.6 (GPIO5), U2.7 (A5), U3.7 (A5), U4.7 (A5)
SB6: M1.7 (GPIO6), U2.8 (A6), U3.8 (A6), U4.8 (A6)
SB7: M1.8 (GPIO7), U2.9 (A7), U3.9 (A7), U4.9 (A7)
TMDS_CKM: M1.15 (GPIO14), R17.1
TMDS_CKP: M1.16 (GPIO15), R16.1
TMDS_D0M: M1.13 (GPIO12), R15.1
TMDS_D0P: M1.14 (GPIO13), R14.1
TMDS_D1M: M1.17 (GPIO16), R13.1
TMDS_D1P: M1.18 (GPIO17), R12.1
TMDS_D2M: M1.19 (GPIO18), R11.1
TMDS_D2P: M1.20 (GPIO19), R10.1
VB0: M1.35 (GPIO34), R26.1
VB1: M1.36 (GPIO35), R27.1
VBUS_VID: D1.1 (K), M1.49 (VBUS)
VG0: M1.32 (GPIO31), R23.1
VG1: M1.33 (GPIO32), R24.1
VG2: M1.34 (GPIO33), R25.1
VGA_B: J2.3, R26.2, R27.2
VGA_G: J2.2, R23.2, R24.2, R25.2
VGA_R: J2.1, R20.2, R21.2, R22.2
VID_BASE: JP1.1, M1.44 (GPIO43), RN2.1 (R1.1)
VR0: M1.29 (GPIO28), R20.1
VR1: M1.30 (GPIO29), R21.1
VR2: M1.31 (GPIO30), R22.1
VSYNC: M1.38 (GPIO37), R29.1
VSYNC_J: J2.14, R29.2
~IOR: M1.11 (GPIO10)
~IOW: M1.12 (GPIO11)
~MEMR: M1.9 (GPIO8)
~MEMW: M1.10 (GPIO9)

Notes on the sheet:
SOFT CARD: ISA bus + power ONLY. Self-decodes 0xA0000-0xBFFFF and 3B4/3B5/3B8/3BA/3BF + 3D4/3D5/3D8/3D9/3DA from snooped A17-A19/A0-A9. No Y5, no link, no host RAM (design S8). Disable: addr_decode JP1.5 (DIS_VID high, firmware keeps all OEs off; enabled by default). JP1 = CGA (closed) / MDA (open)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
HDMI: +5V fused (F1); HPD sensed on GPIO41. Add TMDS ESD array (TPD4E05U06-class, <=0.15pF) at layout -- no KiCad symbol yet.
