vaelen/mini-xt/hardware/sheets/storage.py

"""Storage -- XT-IDE rev2 / "Chuck-mod" 8-bit interface + CompactFlash @ I/O 0x300.

Design doc S10. A discrete, period-correct mass-storage soft card:

  * 16-bit IDE data register made accessible as two 8-bit transfers
    ("Chuck-mod" high-byte latch):
      - 74LVC245A buffers bus D0-D7  <-> IDE/CF D0-D7  (low byte, direct).
      - 74LVC573A WRITE latch: bus D0-D7 -> IDE D8-D15, loaded on a write to the
        high-byte register, output-enabled only on the IDE data-register write.
      - 74LVC573A READ  latch: IDE D8-D15 -> bus D0-D7, loaded on the IDE
        data-register read, output-enabled when reading the high-byte register.
  * Address decode: TRUE rev-2 / Chuck-mod map = rev 1 with bus A0<->A3 swapped
    at the card, giving XTIDE Universal BIOS's "XT-IDE rev 2" layout in a
    16-byte window (0x300-0x30F):
      data 0x300, HIGH-BYTE LATCH 0x301, count 0x302, cyl-lo 0x304, drv/head
      0x306, altstatus/devctl 0x307, error/feat 0x308, sector 0x30A, cyl-hi
      0x30C, status/cmd 0x30E, drive-addr 0x30F.  Drive DA0 = bus A3 (!),
      DA1 = A1, DA2 = A2.
      - Block match (A9/A8/~A7/~A6/A5-strap, AEN low) arrives ready-made as
        ~{IDE_CS} from the central addr_decode sheet (2026-07-14 chip-count
        reduction; the old on-card 74HC08 qualifier + A5/A6/A7 inverters and
        the 0x300/0x320 strap live there now -- mxbus.PRIV_CS, so lifting
        this to a standalone card means re-adding that decode).
      - 74HC138 (DEC1) splits the window on A0/A4: ~Y0 = /CS0 (even offsets =
        command block), ~Y1 = /ODD_SEL (odd offsets: latch + control block).
      - 74HC138 (DEC2) decodes A1,A2,A3 inside ODD: ~Y0 = high-byte latch
        (0x301); ~Y3/~Y7 (0x307/0x30F) AND together (U3) into /CS1, so the
        latch address never asserts a drive CS or the low-byte buffer.
      - 74HC138 (DEC3/U11) decodes A1,A2,A3 inside CS0: ~Y0 = data reg 0x300.
      - glue: 74HC08 (buffer enable + CS1 combine), 74HC32 (strobe
        combiners), 74HC04 (latch strobes + IDE -RESET).
  * 40-pin IDE header (Conn_02x20) and a CompactFlash True-IDE socket
    (Conn_02x25, 50-pin -- no CF symbol in lib, see questions-storage.md) wired
    in parallel.
  * Drive INTRQ -> 2N7002 inverter -> ~{IRQ_IDE} request (mxbus.PRIV_IRQREQ)
    -> addr_decode's shared 74LVC125A -> IRQ14, hardwired (AT primary-IDE
    convention; the soft PIC is AT-style anyway). Poll vs interrupt is an
    XTIDE UB config choice -- the '125 only drives while INTRQ is asserted.
  * Base address hardwired 0x300 (the 0x320 strap is gone); the disable
    jumper is addr_decode JP1.4 (DIS_IDE; enabled by default, cap to disable).

3.3V single-board redesign (spec 2026-07-14, task 7): all logic on this
sheet moves to +3V3 (decode glue -> HC-grade, the data-path/IRQ buffers
facing the IDE header/CF socket -> LVC-grade for 5V-tolerant inputs, since
an external drive or CF adapter may drive 5V back). The CompactFlash
socket's own VCC feed pins (J2 13/36/38/44) stay +5V -- a real power-supply
requirement of the CF slot, not a logic signal.

Soft card: exposes ONLY ISA signals + power. The IDE/CF connectors are local.
See hardware/notes/questions-storage.md for the register-map / topology picks.
Card can be disabled or re-strapped so an external XT-IDE on the sidecar
doesn't conflict.
"""
import mxbus
from mxbus import pin

NAME = "storage"
TITLE = "Storage -- XT-IDE (Chuck-mod) + CompactFlash @ 0x300"

PINS = (
    [pin(s, "input") for s in mxbus.ADDR[:5]] +           # A0..A4 (in-window decode + drive DA lines)
    [pin(s, "bidirectional") for s in mxbus.DATA] +       # D0..D7
    [pin(s, "input") for s in ["~{IOR}", "~{IOW}", "RESET_DRV",
                               "~{IDE_CS}"]] +   # central block decode (addr_decode)
    [pin("~{IRQ_IDE}", "output")]  # active-low IRQ request -> addr_decode's
                                   # '125 drives IRQ14 (AT primary-IDE convention)
)


def build(sch, lib, expose=True):
    if expose:        # standalone dev-card PCBs tie to on-card headers, not a parent
        mxbus.emit_interface(sch, PINS, at=(25.4, 25.4))

    def L(c, p, net, dx=2.54, dy=0.0):
        sch.net(c, p, net, kind="label", dx=dx, dy=dy)

    def pwr(c, vpin, gpin, vnet="+3V3"):
        L(c, vpin, vnet, dx=0, dy=-2.54)
        L(c, gpin, "GND", dx=0, dy=2.54)

    def decouple(ref, at):
        c = sch.place("Device:C", ref, "100nF", at=at)
        sch.net(c, "1", "+3V3", kind="label", dx=0, dy=-2.54)
        sch.net(c, "2", "GND", kind="label", dx=0, dy=2.54)

    # ============================================================ glue logic ===
    # ---- 74HC04 hex inverter: latch strobes, address inverts, IDE -RESET ----
    # 74HC04 value override (spec 2026-07-14): 74HCT is out of spec below
    # 4.5V VCC; all inputs here are 3.3V-driven decode/address signals.
    INV = sch.place("mini-xt:74HCT04", "U1", "74HC04", at=(38.1, 76.2))
    pwr(INV, "VCC", "GND")
    L(INV, "P1", "HBW_N", dx=-2.54);  L(INV, "P2", "LE_W")     # write-latch Load
    L(INV, "P3", "DR_N",  dx=-2.54);  L(INV, "P4", "LE_RD")    # read-latch  Load
    # (the A5/A6/A7 inverters moved to the central addr_decode sheet with the
    # block qualifier; three spare gates)
    for ip in ("P5", "P9", "P11"):
        L(INV, ip, "GND", dx=-2.54)
    for op in ("P6", "P8", "P10"):
        sch.no_connect(INV.pin_xy(op))
    L(INV, "P13", "RESET_DRV", dx=-2.54); L(INV, "P12", "~{IDE_RST}")

    # ---- 74HC08: low-byte buffer enable + CS1 combine ----
    AND2 = sch.place("mini-xt:74HCT08", "U3", "74HC08", at=(38.1, 205.74))
    pwr(AND2, "VCC", "GND")
    L(AND2, "P1", "~{IDE_CS0}", dx=-2.54); L(AND2, "P2", "~{IDE_CS1}", dx=-2.54)
    L(AND2, "P3", "~{DBUF_OE}")            # buffer on for any DRIVE access (not the latch)
    # /CS1 = control-block regs only (0x307 altstatus, 0x30F drive-addr): AND of
    # the two active-low DEC2 outputs -- low when either decodes.
    L(AND2, "P4", "~{CS1_A}", dx=-2.54); L(AND2, "P5", "~{CS1_B}", dx=-2.54)
    L(AND2, "P6", "~{IDE_CS1}")
    for u in ("P9", "P10", "P12", "P13"):        # spare gates: tie inputs
        L(AND2, u, "GND", dx=-2.54)
    sch.no_connect(AND2.pin_xy("P8")); sch.no_connect(AND2.pin_xy("P11"))

    # ---- 74HC32: strobe combiners (active-low pins -> active-low strobe) ----
    # 74HC32 value override (same rationale as U1).
    OR = sch.place("mini-xt:74HCT32", "U4", "74HC32", at=(114.3, 210.82))
    pwr(OR, "VCC", "GND")
    L(OR, "P1", "~{DATA_SEL}", dx=-2.54); L(OR, "P2", "~{IOW}", dx=-2.54); L(OR, "P3", "~{DWR_N}")   # data write
    L(OR, "P4", "~{DATA_SEL}", dx=-2.54); L(OR, "P5", "~{IOR}", dx=-2.54); L(OR, "P6", "DR_N")        # data read
    L(OR, "P9", "~{HB_SEL}", dx=-2.54);  L(OR, "P10", "~{IOR}", dx=-2.54); L(OR, "P8", "~{HBRD_N}")  # HB read
    L(OR, "P12", "~{HB_SEL}", dx=-2.54); L(OR, "P13", "~{IOW}", dx=-2.54); L(OR, "P11", "HBW_N")      # HB write

    # ---- IRQ request: Q1 (2N7002) inverts INTRQ into ~{IRQ_IDE} ----
    # INTRQ=1 -> ~{IRQ_IDE}=0 -> addr_decode's shared '125 drives IRQ14 high
    # (its input straps high there); INTRQ=0 -> R4 parks the request high ->
    # Z, so the line stays shareable. (The '125 itself moved to addr_decode
    # with the rest of the IRQ mapping, 2026-07-14.)
    Q1 = sch.place("Device:Q_NMOS", "Q1", "2N7002", at=(76.2, 256.54))
    L(Q1, "G", "IDE_IRQ", dx=-2.54)
    L(Q1, "D", "~{IRQ_IDE}", dx=0, dy=-2.54)
    L(Q1, "S", "GND", dx=0, dy=2.54)

    # ============================================================== decode ====
    # Rev-2 = A0<->A3 swap: A0 splits even (drive command block) vs odd (latch
    # + control block); the drive's DA0 is bus A3 (wired at the connectors).
    # ---- DEC1: window split on A0/A4 -> /CS0 (even), /ODD_SEL (odd) ----
    # 74HC138 value override (spec 2026-07-14): all inputs 3.3V-driven.
    DEC1 = sch.place("mini-xt:74HCT138", "U6", "74HC138", at=(114.3, 63.5))
    pwr(DEC1, "VCC", "GND")
    L(DEC1, "A0", "A0", dx=-2.54); L(DEC1, "A1", "A4", dx=-2.54); L(DEC1, "A2", "GND", dx=-2.54)
    L(DEC1, "~{E0}", "~{IDE_CS}", dx=-2.54)   # central block match (AEN-gated there;
    L(DEC1, "~{E1}", "GND", dx=-2.54)         #  its DIS_IDE jumper is the disable)
    L(DEC1, "E2", "+3V3", dx=-2.54)
    L(DEC1, "~{Y0}", "~{IDE_CS0}")     # even offsets 0x300..0x30E: command block
    L(DEC1, "~{Y1}", "~{ODD_SEL}")     # odd offsets 0x301..0x30F: latch + ctrl
    for y in ("~{Y2}", "~{Y3}", "~{Y4}", "~{Y5}", "~{Y6}", "~{Y7}"):
        sch.no_connect(DEC1.pin_xy(y))  # A4=1 region unused (16-byte window)

    # ---- DEC2: odd-side decode (A1,A2,A3): latch @0x301, CS1 @0x307/0x30F ----
    DEC2 = sch.place("mini-xt:74HCT138", "U7", "74HC138", at=(114.3, 142.24))
    pwr(DEC2, "VCC", "GND")
    L(DEC2, "A0", "A1", dx=-2.54); L(DEC2, "A1", "A2", dx=-2.54); L(DEC2, "A2", "A3", dx=-2.54)
    L(DEC2, "~{E0}", "~{ODD_SEL}", dx=-2.54); L(DEC2, "~{E1}", "GND", dx=-2.54); L(DEC2, "E2", "+3V3", dx=-2.54)
    L(DEC2, "~{Y0}", "~{HB_SEL}")      # 0x301 = high-byte latch register
    L(DEC2, "~{Y3}", "~{CS1_A}")       # 0x307 = altstatus / device control
    L(DEC2, "~{Y7}", "~{CS1_B}")       # 0x30F = drive address
    for y in ("~{Y1}", "~{Y2}", "~{Y4}", "~{Y5}", "~{Y6}"):
        sch.no_connect(DEC2.pin_xy(y))

    # ---- DEC3: even-side decode (A1,A2,A3) inside CS0; ~Y0 = data reg 0x300 ----
    DEC3 = sch.place("mini-xt:74HCT138", "U11", "74HC138", at=(152.4, 63.5))
    pwr(DEC3, "VCC", "GND")
    L(DEC3, "A0", "A1", dx=-2.54); L(DEC3, "A1", "A2", dx=-2.54); L(DEC3, "A2", "A3", dx=-2.54)
    L(DEC3, "~{E0}", "~{IDE_CS0}", dx=-2.54); L(DEC3, "~{E1}", "GND", dx=-2.54); L(DEC3, "E2", "+3V3", dx=-2.54)
    L(DEC3, "~{Y0}", "~{DATA_SEL}")    # 0x300 = 16-bit data register
    for y in ("~{Y1}", "~{Y2}", "~{Y3}", "~{Y4}", "~{Y5}", "~{Y6}", "~{Y7}"):
        sch.no_connect(DEC3.pin_xy(y))

    # =========================================================== data path ====
    # ---- 74LVC245A low-byte buffer: bus D0-D7 <-> IDE/CF D0-D7 ----
    # 74LVC245A value override (spec 2026-07-14): this buffer's B-side faces
    # the IDE header/CF socket -- an external drive or CF adapter may drive
    # 5V signal levels back onto ID0-7, so the connector-facing part needs
    # LVC's 5V-tolerant inputs even though it's now +3V3-powered (same rule
    # as the LPT card's connector-facing buffers).
    LB = sch.place("mini-xt:74HCT245", "U8", "74LVC245A", at=(190.5, 63.5))
    pwr(LB, "VCC", "GND")
    L(LB, "A->B", "~{IOR}", dx=-2.54)    # write (IOR high) drives bus->IDE
    L(LB, "CE", "~{DBUF_OE}", dx=-2.54)  # enabled for any IDE register access
    for i in range(8):
        L(LB, "A%d" % i, "D%d" % i, dx=-2.54)     # bus side
        L(LB, "B%d" % i, "ID%d" % i)              # IDE side (low byte)

    # ---- 74LVC573A high-byte WRITE latch: bus D0-D7 -> IDE D8-D15 ----
    # 74LVC573A value override: same IDE-connector-facing rationale as U8.
    HW = sch.place("mini-xt:74HCT573", "U9", "74LVC573A", at=(190.5, 142.24))
    pwr(HW, "VCC", "GND")
    L(HW, "Load", "LE_W", dx=-2.54)      # capture on write to HB register
    L(HW, "OE", "~{DWR_N}", dx=-2.54)    # drive IDE high byte only on data write
    for i in range(8):
        L(HW, "D%d" % i, "D%d" % i, dx=-2.54)     # bus side
        L(HW, "Q%d" % i, "ID%d" % (8 + i))        # IDE high byte D8..D15

    # ---- 74LVC573A high-byte READ latch: IDE D8-D15 -> bus D0-D7 ----
    # 74LVC573A value override: same IDE-connector-facing rationale as U8.
    HR = sch.place("mini-xt:74HCT573", "U10", "74LVC573A", at=(190.5, 215.9))
    pwr(HR, "VCC", "GND")
    L(HR, "Load", "LE_RD", dx=-2.54)     # capture IDE high byte on data read
    L(HR, "OE", "~{HBRD_N}", dx=-2.54)   # present to bus when reading HB register
    for i in range(8):
        L(HR, "D%d" % i, "ID%d" % (8 + i), dx=-2.54)   # IDE high byte
        L(HR, "Q%d" % i, "D%d" % i)                    # bus side

    # ============================================================ connectors ==
    def conn_wire(conn, mapping, nc):
        for num, net in mapping.items():
            dx = -2.54 if int(num) % 2 == 1 else 2.54   # odd col left, even col right
            sch.net(conn, str(num), net, kind="label", dx=dx)
        for num in nc:
            sch.no_connect(conn.pin_xy(str(num)))

    # ---- 40-pin IDE header (standard ATA pinout) ----
    # Value "IDE 40-pin (boxed)" binds a SHROUDED IDC box header in parts.py
    # (C9138) instead of the generic breakaway strip -- an IDE ribbon plug
    # gets polarized instead of relying on silkscreen pin-1. Pin 20 (the ATA
    # keypin) is NC below; clip it at assembly if using keyed (plugged-20)
    # cables.
    IDE = sch.place("Connector_Generic:Conn_02x20_Odd_Even", "J1",
                    "IDE 40-pin (boxed)", at=(292.1, 127.0))
    ide_map = {
        1: "~{IDE_RST}", 2: "GND",  3: "ID7", 4: "ID8", 5: "ID6", 6: "ID9",
        7: "ID5", 8: "ID10", 9: "ID4", 10: "ID11", 11: "ID3", 12: "ID12",
        13: "ID2", 14: "ID13", 15: "ID1", 16: "ID14", 17: "ID0", 18: "ID15",
        19: "GND", 22: "GND", 23: "~{IOW}", 24: "GND", 25: "~{IOR}", 26: "GND",
        27: "~{IORDY}", 28: "GND", 30: "GND", 31: "IDE_IRQ", 33: "A1", 35: "A3",
        36: "A2", 37: "~{IDE_CS0}", 38: "~{IDE_CS1}", 40: "GND",   # DA0 = bus A3 (rev-2 swap)
    }
    conn_wire(IDE, ide_map, nc=[20, 21, 29, 32, 34, 39])

    # ---- 50-pin CompactFlash socket, True-IDE mode (parallel to IDE) ----
    # Pins 13/36/38/44 stay +5V (unchanged): these are the CF slot's own VCC
    # power-feed pins per the CF pinout spec (the card has no separate power
    # connector), not logic signals -- see questions-storage.md.
    CF = sch.place("Connector_Generic:Conn_02x25_Odd_Even", "J2", at=(368.3, 127.0))
    cf_map = {
        1: "GND", 2: "ID3", 3: "ID4", 4: "ID5", 5: "ID6", 6: "ID7",
        7: "~{IDE_CS0}", 8: "GND", 9: "GND", 10: "GND", 11: "GND", 12: "GND",
        13: "+5V", 14: "GND", 15: "GND", 16: "GND", 17: "GND", 18: "A2",
        19: "A1", 20: "A3", 21: "ID0", 22: "ID1", 23: "ID2", 26: "GND",  # DA0 = bus A3
        27: "ID11", 28: "ID12", 29: "ID13", 30: "ID14", 31: "ID15",
        32: "~{IDE_CS1}", 34: "~{IOR}", 35: "~{IOW}", 36: "+5V", 37: "IDE_IRQ",
        38: "+5V", 39: "GND", 41: "~{IDE_RST}", 42: "~{IORDY}", 44: "+5V",
        47: "ID8", 48: "ID9", 49: "ID10", 50: "GND",
    }
    conn_wire(CF, cf_map, nc=[24, 25, 33, 40, 43, 45, 46])

    # =============================================================== passives =
    # Idle parks, consolidated into one 4x10k basic array (2026-07-14;
    # isolated elements, so the pack mixes rails -- one spare):
    #  * ~{IORDY} idle-high (8-bit PIO)
    #  * ~{IRQ_IDE} request parks high (Z) when INTRQ low
    #  * IDE_IRQ: ATA INTRQ is ACTIVE-HIGH and tri-stated whenever no drive
    #    is selected (or nIEN=1), so it parks DEASSERTED: pull-DOWN. (A
    #    pull-up would hold IRQ14 asserted -> interrupt storm once unmasked.)
    mxbus.r_pack4(sch, "RN1", "10kx4", (228.6, 25.4),
                  [("~{IORDY}", "+3V3"), ("~{IRQ_IDE}", "+3V3"),
                   ("IDE_IRQ", "GND")])
    # (Base hardwired 0x300; the disable is addr_decode JP1.4 (DIS_IDE) --
    # fitting it forces ~{IDE_CS} inactive, so /CS0, /ODD_SEL and
    # everything downstream (DEC2/DEC3, both '573 latch clocks, the '245
    # enable) are inert and IRQ14 stays quiet: the drive is never selected
    # and R2 holds INTRQ low.)
    for i, x in enumerate(range(30, 210, 20)):
        decouple("C%d" % (1 + i), (float(x), 276.86))
    cb = sch.place("Device:C", "C12", "10uF", at=(256.54, 276.86))   # card bulk (+3V3: sheet's logic domain)
    sch.net(cb, "1", "+3V3", kind="label", dx=0, dy=-2.54)
    sch.net(cb, "2", "GND", kind="label", dx=0, dy=2.54)

    # =============== strapping notes ==
    sch.text("Base hardwired 0x300; disable: addr_decode JP1.4 (cap to disable); IRQ14 hardwired (poll vs IRQ = XTIDE UB config).", at=(266.7, 17.78))
    sch.text("Populate ONE of J1 (IDE) / J2 (CF): both CSELs are grounded, so both "
             "devices ID as master on the shared cable.", at=(266.7, 12.7))
